pjcau/esp32-emu-turbo/docs/REPO_MAP.md

# Repo map — scripts

<!-- GENERATED by scripts/generate_repo_map.py — do not edit. -->
<!-- Regenerate: make repo-map    Verify: make repo-map-check -->

210 scripts, ~867,666 tokens of source. This index exists so that
finding the right one costs a single read instead of a repo-wide grep.

**gate** = exits non-zero on failure, so it can block a pipeline.
**~tok** = cost of opening the file, in tokens.

## `scripts/`

| script | gate | make | ~tok | purpose |
|---|:--:|---|--:|---|
| `analyze_pad_distances.py` | ✅ |  | 5,229 | Analytical pad distance checker for KiCad PCB files |
| `analyze_pin1_marker.py` |  | `analyze-pin1` | 3,075 | Locate the PHYSICAL pin-1 / polarity marker of an LCSC part, analytically |
| `arcade_art.py` | ✅ |  | 1,116 | arcade_art.py: launcher covers for the Neo Geo and CPS1 games, and the list of CPS1 sets |
| `audio_compare.py` | ✅ |  | 2,374 | audio_compare.py: can a listener tell two renderings of the same sound apart? |
| `board_cam.py` |  |  | 372 | Grab one frame from the webcam pointed at the board's screen |
| `board_ctl.py` |  |  | 4,471 | Drive the ESP32 Emu Turbo board over its USB console (bench remote control) |
| `console_art.py` | ✅ |  | 2,322 | console_art.py: launcher covers for the console games (the arcade ones: arcade_art.py) |
| `context_budget.py` |  | `context-budget` | 2,218 | Measure what this repo costs an AI agent's context window |
| `cps1_modern_sets.py` |  |  | 2,029 | Generate MAME 0.37b5 definitions for modern CPS1 ROM sets |
| `drc_check.py` | ✅ |  | 8,442 | DRC (Design Rule Check) for JLCPCB 4-layer PCB |
| `drc_native.py` | ✅ |  | 5,131 | Smart KiCad DRC analysis with JLCPCB rules and fix suggestions |
| `emu_check.py` |  |  | 1,176 | Quick 60 fps check across the non-SNES emulators on the card |
| `enclosure_placement.py` | ✅ |  | 1,624 | Place the PRINT files in the assembly — the viewer shows what you print |
| `erc_check.py` | ✅ |  | 3,867 | ERC (Electrical Rules Check) automation for KiCad schematics |
| `generate-schematic.py` |  |  | 96 | Thin wrapper: generate multi-sheet KiCad schematics for ESP32 Emu Turbo |
| `generate_board_config.py` | ✅ |  | 1,096 | Generate board_config.h GPIO #defines from config.py GPIO_NETS |
| `generate_docs_bom.py` | ✅ | `docs-bom` | 1,663 | Generate the docs BOM table from release_jlcpcb/bom.csv — the shipped BOM |
| `generate_enclosure_pcb.py` | ✅ | `generate-pcb` | 1,426 | Emit hardware/enclosure/pcb_parts.scad — the PCB, to the millimetre, for |
| `generate_net_explorer.py` | ✅ | `generate-pcb` | 5,986 | Emit the data file behind website/static/net-explorer.html |
| `generate_repo_map.py` | ✅ | `repo-map` | 1,219 | Generate docs/REPO_MAP.md — one line per script, so nobody greps 447k tokens |
| `generate_splash_preview.py` | ✅ |  | 3,457 | Build the web preview of the launcher boot splash from the firmware source |
| `inject-3d-models.py` | ✅ |  | 2,398 | Inject KiCad standard 3D model references into PCB footprints |
| `issue_dispatch.py` |  | `dispatch` | 7,473 | Turn failing hardware gates into briefings addressed to a named agent |
| `jlcpcb_parts.py` | ✅ |  | 2,090 | JLCPCB BOM parser and parts checker |
| `kicad_fill_zones.py` | ✅ |  | 1,582 | Fill all zones in a KiCad PCB file using the pcbnew Python API |
| `neogeo_frames.py` | ✅ |  | 2,808 | neogeo_frames.py: build and run the x86 harness (retro-go/mame-go/tools/neoframes.c) |
| `neogeo_modern_sets.py` |  |  | 2,583 | Generate MAME 0.37b5 ROM definitions for modern Neo Geo ROM sets |
| `neogeo_prepare.py` | ✅ |  | 1,203 | Prepare Neo Geo games for mame-go on the PC instead of on the board |
| `net_classifier.py` |  |  | 1,559 | Net Function Classifier — infers signal function from net names |
| `open_issues_report.py` | ✅ | `open-issues` | 1,832 | Report which hardware gates are currently failing, at session start |
| `order_manifest.py` | ✅ | `order-manifest` | 1,448 | Order manifest — SHA256 fingerprint of exactly what goes to JLCPCB |
| `pcb_cache.py` |  |  | 3,554 | PCB parse cache — parse .kicad_pcb once, cache as JSON for all consumers |
| `pcb_copper_graph.py` |  |  | 3,634 | Zone-aware copper graph — what the fabricated board is actually connected to |
| `pcb_optimize.py` |  |  | 5,102 | PCB Layout Optimization Analysis |
| `pcb_query.py` |  |  | 1,098 | Copper queries against the pcb_cache — answers in ~10 lines, not 265k tokens |
| `pcb_review.py` | ✅ |  | 11,434 | Comprehensive PCB Design Review |
| `render_3v3_rework_figures.py` |  |  | 4,058 | Render the +3V3 split-plane rework figures from the real PCB geometry |
| `saveload_check.py` |  |  | 2,810 | saveload_check.py: save / resume / in-session load of every game, on the board |
| `sd_update.py` |  |  | 878 | Firmware update through the SD card (roadmap Phase 6) |
| `short_circuit_analysis.py` | ✅ | `pcb-check` | 2,546 | Short circuit and zone fill analysis for JLCPCB 4-layer PCB |
| `simulate_circuit.py` | ✅ | `simulate` | 10,560 | Electrical verification and simulation for ESP32 Emu Turbo |
| `snes_bench.py` |  |  | 1,008 | SNES renderer benchmark on the first article: resume each saved scene, capture PROF |
| `spice_power_check.py` | ✅ |  | 1,917 | SPICE power supply simulation for ESP32 Emu Turbo |
| `test_claims_ledger.py` | ✅ |  | 912 | Mutation tests for verify_claims_ledger.py — the ledger gate must be |
| `test_collision_pad_nets.py` | ✅ |  | 2,208 | Mutation tests for the pad side of generate_pcb/collision.py |
| `test_collision_via_metric.py` | ✅ |  | 1,550 | Mutation tests for the via clearance checker in generate_pcb/collision.py |
| `test_cpl_rotation_law.py` | ✅ | `test-cpl-law` | 1,436 | Mutation tests for the CPL rotation law gate |
| `test_enclosure_requirements.py` | ✅ | `test-enclosure-requirements` | 1,770 | Mutation tests for verify_enclosure_requirements.py — every user |
| `test_enclosure_stl_solidity.py` | ✅ | `test-enclosure-stl-solidity` | 986 | Mutation tests for the S12 solidity check in verify_enclosure_stl.py |
| `test_enclosure_sync.py` | ✅ | `test-enclosure-sync` | 1,416 | Mutation tests for verify_enclosure_sync.py — the sync gate must fail |
| `test_erc_severity.py` | ✅ |  | 1,738 | Mutation tests for the ERC verdict in erc_check.py |
| `test_esd_protection.py` | ✅ |  | 898 | Mutation tests for verify_esd_protection.py — the promoted gate must fail |
| `test_gate_coverage.py` | ✅ |  | 1,449 | Mutation tests for verify_gate_coverage.py — the auditor must itself |
| `test_gerber_etest.py` | ✅ |  | 1,676 | Mutation tests for verify_gerber_etest.py — prove the gate can fail |
| `test_issue_dispatch.py` | ✅ |  | 1,958 | Mutation tests for the issue dispatcher's routing law |
| `test_order_manifest.py` | ✅ |  | 973 | Mutation tests for order_manifest.py — the freshness gate must be |
| `test_pcb_connectivity.py` | ✅ |  | 7,342 | Comprehensive PCB connectivity verification |
| `test_power_net_integrity.py` | ✅ | `test-power-nets` | 2,886 | Regression tests for the power-net integrity detector |
| `test_power_via_ampacity.py` | ✅ |  | 3,019 | Mutation tests for verify_power_via_ampacity.py — the gate must object |
| `test_strapping_en_rc.py` | ✅ |  | 2,222 | Mutation tests for the EN check in verify_strapping_pins.test_en_rc_delay |
| `test_test_points.py` | ✅ |  | 852 | Mutation tests for verify_test_points.py — the promoted gate must fail |
| `test_vbench.py` | ✅ | `bench-test` | 17,519 | Mutation tests for the Virtual Bench (Phase 0 foundation, Phase 1 physics, |
| `test_vbench_display.py` | ✅ | `bench-display-test` | 7,090 | Mutation tests for the Virtual Bench display half (T3.1) |
| `test_vbench_dynamics.py` | ✅ |  | 1,488 | Mutation-paired gate for vbench/dynamics.py — the dynamic scenarios |
| `test_vbench_sdcard.py` | ✅ | `bench-sdcard-test` | 5,988 | Mutation tests for the modelled microSD card (Virtual Bench T3.3) |
| `test_verify_memory.py` |  | `test-memory` | 3,325 | Mutation tests for verify_memory.py |
| `test_zone_fill_sanity.py` | ✅ | `test-zone-fill` | 4,118 | Regression tests for the zone-fill duplication bug and its detector |
| `update_component.py` | ✅ |  | 2,854 | Update a component across all BOM, CPL, and documentation files |
| `validate_jlcpcb.py` | ✅ | `validate-jlcpcb` | 7,487 | JLCPCB DFM Validation — comprehensive manufacturing rule checks |
| `validate_skills.py` | ✅ |  | 2,936 | Validator for Claude Code skills, slash commands, and plugin metadata |
| `verify_antenna_keepout.py` | ✅ |  | 3,178 | Antenna Keep-Out Zone verification for ESP32-S3-WROOM-1 (U1) |
| `verify_battery_protection.py` | ✅ |  | 1,517 | Battery Protection Verification — check reverse-polarity and over-voltage protection |
| `verify_bom_cpl_pcb.py` | ✅ |  | 3,391 | Cross-check BOM, CPL, and PCB for consistency |
| `verify_bom_values.py` | ✅ |  | 3,110 | BOM vs Schematic Value Cross-Check |
| `verify_bringup_fresh.py` | ✅ |  | 308 | Fail when the bring-up firmware is stale w.r.t. board_config.h |
| `verify_claims_ledger.py` | ✅ | `verify-claims` | 1,300 | Gate the load-bearing claims ledger — hardware/CLAIMS.md |
| `verify_component_bodies.py` | ✅ |  | 3,614 | Component BODY collision + board-edge gate (JLC SMT DFM classes) |
| `verify_component_connectivity.py` | ✅ |  | 2,224 | Component connectivity verification — catches phantom components |
| `verify_context_budget.py` |  |  | 722 | Gate on the context budget: fail when the repo's per-session cost regresses |
| `verify_copper_balance.py` | ✅ |  | 4,029 | Copper Balance Between Layers — verify copper distribution across all 4 layers |
| `verify_copper_clearance.py` | ✅ | `verify-copper-clearance` | 3,961 | Copper-to-copper clearance gate — catches what DRC misses at ≥ 0.09mm |
| `verify_cpl_rotation_law.py` | ✅ | `verify-cpl-law` | 4,314 | Assert that every CPL rotation obeys ONE global law, instead of a table |
| `verify_crosstalk.py` | ✅ |  | 7,582 | Fail on tightly coupled parallel runs between signals that cannot tolerate them |
| `verify_dangling_copper.py` | ✅ | `verify-dangling` | 865 | Fail on copper that stops in the air — track ends reaching nothing |
| `verify_datasheet.py` | ✅ |  | 6,541 | Datasheet vs PCB physical characteristics cross-verification |
| `verify_datasheet_nets.py` | ✅ | `verify-datasheet` | 2,546 | Verify PCB pad-to-net assignments against datasheet specifications |
| `verify_decoupling_adequacy.py` | ✅ |  | 3,179 | Decoupling Capacitor Adequacy Check |
| `verify_decoupling_paths.py` | ✅ |  | 2,432 | Decoupling Cap Path Length — verify caps have short routing paths to ICs |
| `verify_design_intent.py` | ✅ | `verify-intent` | 13,576 | Design Intent Adversary — cross-checks PCB against ALL design sources |
| `verify_dfa.py` | ✅ | `verify-dfa` | 5,600 | Design for Assembly (DFA) verification — Tier 1 + Tier 2 SMT DFM checks |
| `verify_dfm_v2.py` | ✅ | `verify-fast` | 39,241 | Verify DFM v2 fixes: CPL alignment, silkscreen, spacing, gerbers |
| `verify_drill_standards.py` | ✅ |  | 2,669 | Standard Drill Size Audit |
| `verify_easyeda_footprint.py` | ✅ | `verify-easyeda` | 13,008 | Proactive EasyEDA reference-footprint verification |
| `verify_enclosure_collision.py` | ✅ | `verify-enclosure-collision` | 1,269 | Enclosure interference gate — the shells must not share volume with |
| `verify_enclosure_requirements.py` | ✅ | `verify-enclosure-requirements` | 8,721 | Enclosure REQUIREMENTS gate — the user's constraints, one check each |
| `verify_enclosure_stl.py` | ✅ | `verify-enclosure-stl` | 9,121 | The OTHER road: measure the exported STLs, not the scad |
| `verify_enclosure_sync.py` | ✅ | `verify-enclosure-sync` | 9,434 | Enclosure <-> PCB mechanical sync gate — the shell must fit the board |
| `verify_erc.py` | ✅ | `verify-erc` | 1,080 | Gate: KiCad ERC on the generated schematic — zero findings, ANY severity |
| `verify_esd_protection.py` | ✅ |  | 5,039 | ESD Protection Verification — net-verified evidence for external interfaces |
| `verify_firmware_retrogo_sync.py` | ✅ |  | 3,248 | Retro-go target ↔ board GPIO sync gate |
| `verify_gate_coverage.py` | ✅ | `verify-gate-coverage` | 4,893 | Gate-coverage audit — inject known faults, demand the gate NETWORK object |
| `verify_gerber_etest.py` | ✅ | `verify-gerber-etest` | 5,818 | Gerber-level electrical test — opens and shorts from the SHIPPED artifacts |
| `verify_gerber_integrity.py` | ✅ |  | 1,950 | Gerber Integrity Verification — verify gerber files match the PCB layout |
| `verify_ground_loops.py` | ✅ |  | 1,503 | Test 11: Ground Loop Analysis |
| `verify_isolation.py` | ✅ | `verify-isolation` | 1,564 | Every conductor is connected where intended and isolated everywhere else |
| `verify_jlcpcb_capabilities.py` | ✅ |  | 4,956 | JLCPCB Official Capabilities Cross-Check |
| `verify_jlcpcb_via_rules.py` | ✅ | `verify-jlcpcb-vias` | 1,878 | Via and hole rules straight from JLCPCB's own design guide |
| `verify_length_match.py` | ✅ |  | 5,282 | Trace-length matching on the buses whose members must switch together |
| `verify_memory.py` | ✅ | `verify-memory` | 4,386 | Memory / context-preamble integrity verification |
| `verify_net_class_widths.py` | ✅ |  | 4,128 | Net Class Width Enforcement verification |
| `verify_net_connectivity.py` | ✅ | `verify-net-connectivity` | 6,863 | Net connectivity verification — walks the per-net copper graph and |
| `verify_net_explorer_fresh.py` |  |  | 226 | Fail when the Net Explorer data is stale vs the .kicad_pcb |
| `verify_netlist_diff.py` | ✅ |  | 6,645 | Netlist Diff — exports KiCad schematic netlist and cross-checks it against PCB cache |
| `verify_netlist_vs_kicad.py` | ✅ | `verify-netlist-kicad` | 1,242 | Cross-check our parsed netlist against KiCad's own IPC-D-356 export |
| `verify_order_manifest.py` |  | `verify-order-manifest` | 189 | Fail when release_jlcpcb/order-manifest.json is stale vs the order files |
| `verify_pad_land.py` | ✅ |  | 1,592 | Pad-vs-reference-land coverage gate (JLC SMT DFM pin/lead classes) |
| `verify_polarity.py` |  |  | 10,998 | Polarity and pin-to-net verification for ALL components on the PCB |
| `verify_power_net_integrity.py` | ✅ | `verify-power-nets` | 2,109 | Power-net integrity gate — every power net must be ONE piece of copper |
| `verify_power_paths.py` | ✅ |  | 3,296 | Power Delivery Path Tracing |
| `verify_power_resonance.py` | ✅ |  | 1,715 | Power Plane Resonance Check — estimate LC resonance of +3V3 plane |
| `verify_power_sequence.py` | ✅ |  | 4,008 | Power Sequencing Verification |
| `verify_power_trace_ampacity.py` | ✅ |  | 4,980 | Power-TRACE ampacity — can the copper itself carry the declared rail? |
| `verify_power_via_ampacity.py` | ✅ |  | 8,236 | Power-via ampacity gate — the layer transitions must carry the rail |
| `verify_reference_plane.py` | ✅ |  | 6,247 | Fail on signals whose reference plane changes underneath them mid-run |
| `verify_rpp_polarity.py` | ✅ |  | 1,068 | Q1 reverse-polarity-protection orientation, proven from the ORDER artifacts |
| `verify_schematic_crossings.py` | ✅ | `verify-sch-crossings` | 1,362 | Fail when two schematic wires cross without being connected |
| `verify_schematic_label_attach.py` | ✅ | `verify-sch-labels` | 1,292 | Fail when a schematic label does not lie on the wire it is meant to name |
| `verify_schematic_overlaps.py` | ✅ | `verify-sch-overlaps` | 3,276 | Schematic legibility gate — nothing printable may overlap anything else |
| `verify_schematic_pcb.py` |  | `firmware-sync-check` | 1,708 | Verify consistency between schematic sheets, main schematic, PCB, and JLCPCB exports |
| `verify_schematic_pcb_sync.py` | ✅ |  | 5,826 | Verify that the Python-generated schematic and the Python-generated PCB agree |
| `verify_schematic_pin_connectivity.py` | ✅ | `verify-sch-pins` | 2,110 | Fail when a placed schematic symbol has a pin that nothing lands on |
| `verify_schematic_render_overlaps.py` | ✅ | `verify-sch-render-overlaps` | 1,869 | Schematic legibility gate #2 — no two RENDERED text runs may overlap |
| `verify_sd_interface.py` | ✅ |  | 1,742 | SD Card Interface Verification — check SPI signal routing and support circuitry |
| `verify_signal_chain_complete.py` | ✅ |  | 3,504 | Signal chain completeness verification — catches broken copper paths |
| `verify_silk_holes.py` | ✅ |  | 2,287 | Silkscreen legibility gate — silk vs drill holes and mask openings |
| `verify_stackup.py` | ✅ |  | 1,794 | Stackup Layer-Net Verification for 4-layer PCB |
| `verify_stencil_aperture.py` | ✅ |  | 2,446 | IPC-7525 Stencil Aperture Analysis |
| `verify_strapping_pins.py` | ✅ |  | 4,172 | ESP32-S3 Strapping Pin Verification — check boot configuration |
| `verify_test_points.py` | ✅ |  | 2,379 | Test 12: Test Point Accessibility — blocking gate |
| `verify_thermal_budget.py` | ✅ |  | 2,839 | Thermal Budget Verification — junction temperature for power ICs |
| `verify_thermal_relief.py` | ✅ |  | 1,414 | Test 10: Thermal Relief Verification |
| `verify_trace_crossings.py` | ✅ | `verify-trace-crossings` | 1,884 | Trace-crossings check — detect pairs of copper segments on the same |
| `verify_trace_through_pad.py` | ✅ | `verify-trace-through-pad` | 2,196 | Trace-through-pad overlap check — detect copper traces physically |
| `verify_usb_impedance.py` | ✅ |  | 6,014 | USB D+/D- signal-integrity check, calibrated to the link's actual bit rate |
| `verify_usb_impedance_stackup.py` | ✅ |  | 2,699 | USB D+/D- Impedance Verification from JLCPCB 4-layer stackup parameters |
| `verify_usb_return_path.py` | ✅ |  | 1,283 | USB GND Return Path Density — verify GND via stitching near USB D+/D- traces |
| `verify_via_discontinuity.py` | ✅ |  | 4,221 | Via count and pair symmetry on the nets where layer changes matter |
| `verify_via_in_pad.py` | ✅ |  | 1,745 | Via-in-Pad Comprehensive Check — via holes must clear SMD pad edges |
| `verify_zone_connectivity.py` | ✅ |  | 2,616 | Zone Connectivity Verification — verify vias/pads on zone nets are covered by fill |
| `verify_zone_fill_sanity.py` | ✅ | `verify-zone-fill` | 2,376 | Zone-fill sanity gate — catches duplicated / impossible poured copper |
| `violation_matrix.py` |  |  | 3,340 | Violation matrix: parse .kicad_pcb and find ALL pad/via spacing violations |
| `zone_fill_inject.py` |  |  | 818 | Pure-text injection of zone fill data into a .kicad_pcb |

## `scripts/generate_pcb/`

| script | gate | make | ~tok | purpose |
|---|:--:|---|--:|---|
| `__main__.py` | ✅ |  | 56 | CLI entry point: python -m scripts.generate_pcb <output_dir> |
| `board.py` |  |  | 8,866 | Generate the complete KiCad PCB board |
| `collision.py` |  |  | 8,752 | Spatial collision detection for PCB trace routing |
| `footprints.py` |  |  | 12,472 | KiCad PCB footprint definitions with real pad geometries |
| `jlcpcb_export.py` |  |  | 8,483 | Generate JLCPCB CPL (Component Placement List) from board data |
| `pad_positions.py` |  |  | 1,550 | Compute absolute PCB-level pad positions for all components |
| `primitives.py` |  |  | 4,092 | KiCad PCB S-expression primitives |

## `scripts/generate_pcb/routing/`

| script | gate | make | ~tok | purpose |
|---|:--:|---|--:|---|
| `_assemble.py` |  |  | 2,268 | Split from routing.py 2026-07-26 — mechanical, AST-driven, proven by a |
| `_shared.py` |  |  | 17,758 | Complete PCB trace routing with Manhattan (orthogonal) paths |
| `audio.py` |  | `bench-audio` | 9,068 | Split from routing.py 2026-07-26 — mechanical, AST-driven, proven by a |
| `buttons.py` |  | `bench-buttons` | 29,484 | Split from routing.py 2026-07-26 — mechanical, AST-driven, proven by a |
| `display.py` |  | `bench-display` | 10,887 | Split from routing.py 2026-07-26 — mechanical, AST-driven, proven by a |
| `passives.py` |  |  | 8,336 | Split from routing.py 2026-07-26 — mechanical, AST-driven, proven by a |
| `power.py` |  |  | 29,065 | Split from routing.py 2026-07-26 — mechanical, AST-driven, proven by a |
| `sd.py` |  |  | 3,604 | Split from routing.py 2026-07-26 — mechanical, AST-driven, proven by a |
| `usb.py` |  |  | 8,917 | Split from routing.py 2026-07-26 — mechanical, AST-driven, proven by a |

## `scripts/generate_schematics/`

| script | gate | make | ~tok | purpose |
|---|:--:|---|--:|---|
| `__main__.py` |  |  | 187 | CLI entry point: python -m generate_schematics /output/dir |
| `config.py` |  |  | 984 | Shared configuration: GPIO mapping, ESP32 pin definitions, layout constants |
| `kicad_primitives.py` |  |  | 3,591 | KiCad S-expression primitives for schematic generation |
| `lib_symbols.py` |  |  | 11,708 | KiCad library symbol definitions for all components |
| `root_schematic.py` |  |  | 757 | Generate a hierarchical root schematic referencing all sub-sheets |
| `sheet_base.py` |  |  | 1,721 | Base class for KiCad schematic sheet generation |

## `scripts/generate_schematics/sheets/`

| script | gate | make | ~tok | purpose |
|---|:--:|---|--:|---|
| `audio.py` |  | `bench-audio` | 3,541 | Sheet 4: Audio - I2S DAC -> PAM8403 -> Speaker |
| `controls.py` |  |  | 2,296 | Sheet 6: Controls - 12 buttons with pull-ups and debounce capacitors |
| `display.py` |  | `bench-display` | 2,912 | Sheet 3: Display — ILI9488 3.95" 320×480 8-bit 8080 parallel interface |
| `mcu.py` |  |  | 4,677 | Sheet 2: MCU - ESP32-S3-WROOM-1 N16R8 with decoupling and GPIO labels |
| `power_supply.py` |  |  | 14,594 | Sheet 1: Power Supply - USB-C -> IP5306 bare IC -> SY8089 buck -> 3.3V |
| `sd_card.py` |  |  | 910 | Sheet 5: SD Card - SPI interface for ROM storage |

## `scripts/mamebench/`

| script | gate | make | ~tok | purpose |
|---|:--:|---|--:|---|
| `mbsum.py` |  |  | 597 | mbsum.py <log>: MAMEBENCH hashes, the average NEOPROF ms (68000, video, total core 0) |
| `wait_launcher.py` |  |  | 120 | wait_launcher.py: wait (60 s max) until the board answers ping from the launcher |

## `scripts/vbench/`

| script | gate | make | ~tok | purpose |
|---|:--:|---|--:|---|
| `audio.py` | ✅ | `bench-audio` | 3,017 | Virtual Bench T3.2 — the audio chain, and the current it pulls off the rail |
| `buttons.py` | ✅ | `bench-buttons` | 3,760 | Virtual Bench T2.2 + T2.3 — the buttons' debounce RC, and the power switch |
| `conflicts.py` | ✅ | `bench-conflicts` | 2,316 | Virtual Bench T1.3 — electrical conflicts: two things fighting over one net |
| `corpus.py` | ✅ | `bench-retro` | 3,420 | Virtual Bench T0.3 — the retro corpus, and the proof it is not fiction |
| `detectors.py` |  |  | 3,016 | Virtual Bench T5.1 — does the bench actually rediscover the known bugs? |
| `display.py` | ✅ | `bench-display` | 5,696 | Virtual Bench T3.1 — the display: the panel's wiring, and the controller |
| `dynamics.py` | ✅ | `bench-dynamics` | 4,387 | Virtual Bench T1.4b — dynamic corner scenarios (containment layer 3) |
| `export_header.py` | ✅ | `bench-header` | 2,935 | Virtual Bench T4.1 — export the derived board facts as a C header |
| `ili9488_ctrl.py` | ✅ | `bench-display-frame` | 7,983 | Virtual Bench T3.1 — the ILI9488 controller, as a state machine |
| `mutate.py` |  |  | 1,861 | Break the board on purpose, in memory, so the bench can be measured |
| `netlist.py` | ✅ | `bench-netlist` | 7,575 | Virtual Bench T0.1 — the netlist the bench stands on, and its disputes |
| `pins.py` | ✅ | `bench-pins` | 2,442 | Virtual Bench T2.1 + T2.4 — the pin fabric, and what this board boots into |
| `rails.py` | ✅ | `bench-rails` | 5,336 | Virtual Bench T1.1 — the DC operating point: what voltage sits on every net |
| `scenario.py` | ✅ | `bench-ci` | 2,501 | Virtual Bench T4.3 — scenarios with assertions, headless, for CI |
| `sdcard.py` | ✅ | `bench-sd` | 2,424 | Virtual Bench T3.3 — the SD card's bus, and the pads it shares with signals |
| `sdcard_protocol.py` | ✅ | `bench-sdcard` | 9,830 | Virtual Bench T3.3 — a microSD card that answers, and a host that asks |
| `sources.py` |  |  | 988 | Virtual PSU and virtual LiPo — what the bench connects the board to |
| `thermal.py` | ✅ | `bench-thermal` | 3,214 | Virtual Bench T1.5 — junction temperatures, and which ones are guesses |
| `transients.py` | ✅ | `bench-transients` | 5,190 | Virtual Bench T1.4 — transients: cold start, inrush, load steps, brownout |

## `scripts/vbench/models/`

| script | gate | make | ~tok | purpose |
|---|:--:|---|--:|---|
| `_schema.py` |  |  | 3,691 | Virtual Bench T0.2 — what a component model must prove before it counts |
| `bt1_lp105080.py` |  |  | 907 | BT1 — the 105080 LiPo cell, modelled from a FAMILY datasheet |
| `card_microsd.py` |  |  | 5,058 | CARD — the microSD card itself, in SPI mode. The part the socket holds |
| `ds1_ili9488.py` |  |  | 6,333 | DS1 — the ILI9488 CONTROLLER, from the ILITEK specification itself |
| `q1_ao3401a.py` |  |  | 2,129 | Q1/Q2 — AO3401A P-channel MOSFET: battery RPP gate and +5V load switch |
| `u1_esp32s3.py` |  |  | 1,748 | U1 — ESP32-S3-WROOM-1-N16R8: the strapping pins and what they decide |
| `u2_ip5306.py` |  |  | 1,969 | U2 — IP5306, the charger + 5 V boost that feeds everything else |
| `u3_sy8089.py` |  |  | 1,890 | U3 — SY8089AAAC synchronous step-down regulator, the +3V3 source |
| `u5_pam8403.py` |  |  | 1,934 | U5 — PAM8403 filterless class-D amplifier, the speaker driver |
