pjcau/esp32-emu-turbo/docs/first-boot-session-2026-08-29.md

# First-boot session log — 2026-08-29 — article 0003 (v4.9.0, W2026081721393881)

Live session log for the staged sequence in
`website/docs/manufacturing/first-boot.md`. Resume point for any machine.

| Stage | Exit criterion | Result | Evidence |
|---|---|---|---|
| 0 pre-flight | board matches renders, both sides | ✅ PASS | `docs/first-article-phaseB-2026-08-29.md` (continuity check skipped — no multimeter, per "as far as your tools allow") |
| 1 USB only | VBUS LED on | ✅ PASS | `hardware/first-article/v4.9.0-W2026081721393881/IMG_5905.jpeg` — VBUS lit with SW16 OFF (rails correctly dark: Q2 gating works) |
| 2 rails | 5V/3V3 LEDs | ✅ PASS | `IMG_5906.jpeg` — SW16 ON: VBUS+5V+3V3 lit, HB dark (chip blank — expected). **Resolves the doc's open question: IP5306 DOES supply 5V batteryless.** CHG+FULL both lit with no cell (undefined-but-harmless, re-check at Stage 4) |
| 3 boot | HB LED 1 Hz + BRINGUP verdict | ✅ PASS | `hardware/first-article/v4.9.0-W2026081721393881/bringup-stage3-serial-2026-08-29.log` — **GREEN, 47 PASS / 0 FAIL / 11 expected SKIP**, reproduced on two consecutive warm resets; HB at 1 Hz confirmed by eye (operator, 2026-08-29). Two latent bring-up firmware bugs found and fixed on the way (see below) |
| 4 battery | boots from cell alone | ✅ PASS (2026-09-11) | 105080 cell on J3 via a soldered JST-PH pigtail: boots from the cell alone, charge-and-play (CHG with USB while running), OFF kills 5V/3V3/HB on battery and stays off, charge-only with USB in OFF (VBUS only), **wake test PASS — C33 4.7 µF closes its BENCH-VALIDATE**. Cell cool under load. See "Stage 4" below |
| 5 subsystems | blink codes clear one by one | ✅ PASS (SD, LCD, audio) | **SD: PASS** — `bringup-stage5-sd-serial-2026-08-29.log`, GREEN 52/0/6 with a 16GB card: full chain incl. FAT mount at 20 MHz. (A no-name 128GB card was rejected at CMD59/CRC_ON_OFF by the IDF driver on every try incl. freshly powered — card-side fault, do not use it.) **LCD: PASS (2026-09-11)** — `bringup-stage5-lcd-serial-2026-09-11.log`, GREEN 53/0/6 with the panel on the R37 workaround (40P extension board + type-B FFC): `lcd.data.risetime` 1000–1200 ns on all of D0–D7 (was ~200 ns unloaded), 8 colour bars confirmed by eye in the documented order, then the black/white load-test fills; no 3V3 event. R37-HIGH-1 stays open only as the v2 top-contact J4 item. **Audio: PASS (operator-confirmed)** — speaker soldered, 3×1 kHz beep pattern clearly recognizable over the R38 carrier hiss (test tone reworked for it; channel now silenced after the check). Clean audio deferred to the R38 v2 fix. Nothing remaining at stage 5 |

## R37-HIGH-1 — J4 contact face is inverted for the purchased panel (found at first article, 2026-08-29)

The purchased panel (marked **LHC400IT005-9488**, ILI9488, 40P 0.5 mm,
separate 4-wire resistive-touch tail left unconnected) carries its tail
contacts on the **opposite face** from what J4 expects. J4 (FPC-05F-NPH20,
C2856812) is a flip-lock **bottom-contact** ("翻盖下接") connector, and its
mouth faces the FPC slot, so the ribbon's entry direction is fixed —
which locks contact-face and pin-order parity together: **no fold or
twist can give "contacts toward PCB + pin 40 on pad 1" at the same
time.** Confirmed on the bench both ways: contacts-up = correct 41−N
order but zero contact (rise-time probe flat at ~200 ns, backlight dark);
flipped = contact but mirrored order → **+3V3 rail collapse** (panel GND
onto 3V3 — operator cut power immediately, board unharmed, next runs
GREEN).

- **First-article workaround**: 40P 0.5 mm FPC extension adapter board +
  **type-B ("opposite side") FFC cable**, as short as possible (3-5 cm —
  the 8080 bus runs at 20 MHz). Type A does not invert; do not use it.
- **v2 fix**: change J4 to the **top-contact** variant of the same
  connector family ("翻盖上接", same footprint) — inverts the face,
  keeps the routed 41−N order, no adapter needed.
- New bring-up check `lcd.data.risetime` (added this session) is the
  no-multimeter contact probe: ~200 ns = panel not loading the data
  lines; a seated panel must slow every line.

## R38-MED-1 — no PDM reconstruction filter in the audio path (found at first article, 2026-08-29)

Speaker soldered (SPK+/SPK− pads, BTL) and the 440 Hz bring-up tone IS
audible — the chain GPIO17 → C22 → PAM8403 → speaker is electrically
alive — but it sounds like a loud fan-like hiss with a faint tone under
it, and cutting the tone amplitude −12 dB did not reduce the hiss:
**the PDM carrier dominates**. Root cause: the board has NO low-pass
between the PDM pin and the amplifier input — C22 is a series DC-block
(a high-pass), and the `audio.c` comment claiming the "existing RC
network acts as a low-pass filter" was wrong (there is no shunt element).
The full-swing MHz PDM stream drives the PAM8403 input directly.

- **v2 fix**: series R (~1k) + shunt C (~10 nF) between C22 and
  PAM_IN_AC — or moot entirely under the planned v2 audio coprocessor
  with a true I2S DAC.
- **First-article rework (optional, fiddly)**: requires inserting a
  series element — deferred unless audio testing needs it.
- Firmware mitigation this session: the bring-up suite now calls
  `audio_stop()` after the audio checks — an enabled-but-idle PDM
  channel emits its 50%-density carrier continuously, which was a
  constant hiss for as long as the board stayed on.
- `audio.audible` verdict: chain alive = the check's purpose met;
  fidelity is R38's problem, not the board assembly's.

## Session close (2026-08-29 evening)

Final board state: **BRINGUP GREEN 53/0/6, HB steady at 1 Hz,
operator-verified.** LED legend learned on the bench: 10-blinks/s
flutter + 1 s pause = "failure with no code", in practice almost always
`bringup.previous_run` after a capture-harness reset killed a run
mid-flight — one clean run (or SW16 power-cycle) clears it; a flutter
that survives a power-cycle would be a real failure.

Resume points, in arrival order:
1. ~~**~2026-09-12** — type-B FFC adapter arrives → LCD retry~~ **DONE
   2026-09-11, PASS** — see "LCD retry" below.
2. Battery cell → stage 4 (LIVE operation, C33 wake test).
3. v2 backlog from today: R37 (top-contact J4), R38 (PDM RC filter),
   plus a +/− silkscreen for the SPK pads.

## LCD retry (2026-09-11) — R37-HIGH-1 workaround validated, stage 5 complete

Parts arrived: 40P 0.5 mm FPC extension board + type-B ("opposite side")
FFC, operator-verified as type B (contacts on opposite faces at the two
ends) and kept short. Chain: panel tail → extension board → type-B FFC →
J4, pin 40 toward the "LCD" silk. Powered from USB, 3V3 LED steady.

Operator observation at power-up: panel white (backlight on, panel not
yet initialised — normal), then **8 vertical colour bars** in the
documented order, then the slow black and white full-screen wipes of
`power.load` (each `display_fill` takes ~1.5 s while both cores are
saturated by the load tasks — 2 fills in 3 s — so the wipes read as a
"curtain"; not a panel symptom), ending on white. HB 1 Hz throughout.

Serial: `bringup-stage5-lcd-serial-2026-09-11.log`, **GREEN 53/0/6**,
`bringup.previous_run` clean (reset=11). The contact probe that was
flat at ~200 ns in August now reads **D0–D3 = 1000 ns, D4–D7 = 1200 ns**
— every data line is loaded by the panel, which with the bars by eye
closes the only LCD check the firmware cannot make itself
(`lcd.panel.readback` is SKIP by design, LCD_RD tied HIGH).

Capture recipe used (same as August, now as a one-shot script): open the
port with DTR=RTS=1 (no reset on open), drain 12 s, one esptool-style
reset (DTR low → RTS high 0.2 s → RTS low), read until a line starting
with `BRINGUP-END`.

Stage 5 is therefore complete on article 0003: SD, LCD and audio all
PASS. Still open on the board: stage 4 (battery — no cell yet). The v2
backlog is unchanged: R37 top-contact J4 (the adapter is a first-article
workaround, not a fix), R38 PDM RC filter, SPK +/− silkscreen.

All seven LED polarities are now physically confirmed (HB beating at 1 Hz
at Stage 3 closed the last one) — the LED `_PENDING_VALIDATION` is fully
closed.

## Stage 3 — how to flash (machine-specific)

Binaries are reproducible from the repo: `make bringup-build` (Docker;
`bringup-check` must stay green). Flash offsets (from
`software/bringup_test/build/flasher_args.json`): `0x0` bootloader,
`0x8000` partition-table, `0x20000` app; DIO, 80 MHz, 16 MB.

- **Linux**: `make bringup-flash` works natively (Docker maps the port).
  The blank S3's USB-Serial-JTAG enumerates as **`/dev/ttyACM0`**, not
  ttyUSB0 — run `ESP_PORT=/dev/ttyACM0 make bringup-flash`.
- **macOS**: Docker cannot pass USB through — flash with local esptool
  (`pip3 install --user esptool`), port `/dev/cu.usbmodem*`:
  `python3 -m esptool --chip esp32s3 -p /dev/cu.usbmodem* -b 460800 \
   write_flash --flash_mode dio --flash_freq 80m --flash_size 16MB \
   0x0 build/bootloader/bootloader.bin 0x8000 build/partition_table/partition-table.bin \
   0x20000 build/esp32-emu-turbo-bringup.bin` (from `software/bringup_test/`).

Board prerequisites for flashing: **USB-C to the computer, SW16 ON** (with
the switch OFF there is no +3V3 and the chip never enumerates). Flash is
factory-blank so the ROM enters download mode by itself; after the first
flash, reset (replug) and expect HB at 1 Hz + the 58-check serial report at
115200 baud (`BRINGUP-SUMMARY` / `BRINGUP-LED` lines are the verdict).

## Stage 3 findings (2026-08-29) — two firmware bugs, zero board defects

Both bugs lived in the bring-up firmware itself and produced false RED
verdicts on a healthy board; both fixed in `generate.py` and re-verified:

1. **`bringup.previous_run` self-poisoning** — `run_check()` stamps the
   crash-forensics marker with the check's own id *before* running it, so
   check 01 read its own freshly-written marker instead of the previous
   run's, and failed on every warm (USB) reset by construction. It only
   ever passed on a true power-on, which is why the doc's "replug" flow
   never showed it. Fix: snapshot the marker in `app_main()` before the
   first `run_check()`.
2. **`usb.serial_jtag` FIFO race** — the check sampled
   `usb_serial_jtag_ll_txfifo_writable()` once, while the report itself
   was filling that FIFO; whenever the host's read cadence left the FIFO
   momentarily full, a live link was reported dead. Fix: poll up to 50 ms
   (an attached host drains it in microseconds).

Capture-harness gotchas for any future machine (all reproduced here):
- **Any DTR/RTS edge on the port resets the chip** (USB-Serial-JTAG reset
  logic; `rst:0x15 USB_UART_CHIP_RESET`): Linux cdc-acm raises DTR on
  open, drops it on close — so `stty`+`cat`, idf_monitor attach, or a
  pyserial open/close each reboot the board mid-run.
- To capture a clean full run: open the port plainly (lines settle at
  DTR=RTS=1, no reset), wait ~12 s for any in-flight run to finish, then
  do one esptool-style reset (DTR low → RTS high 0.2 s → RTS low) and
  read to `BRINGUP-END` while draining continuously.
- Grep for `BRINGUP-END` at start-of-line only: check 01's PASS detail
  contains the literal string "reached BRINGUP-END".

## Retro-Go first boot (2026-09-11) — Phase 2.8 reached, R39-HIGH-1 found

Retro-Go (fork, target `esp32-emu-turbo`) built from the submodule and
flashed as a full image (`rg_tool.py install` at 0x0 — `make
retro-go-flash` cannot be the first flash: it writes per-partition and
the board still carried the bring-up partition table). Card: the 16 GB
SD, FAT32, `roms/<system>/` with the free test ROMs from `test-roms/`.
Four firmware findings, all fixed in the fork (commit 0e533078 +
follow-ups) — none is a board defect:

1. **Half-drawn windows.** `rg_display` streams a window as 4-line DMA
   chunks and the IDF i80 IO sends a command with every chunk; the driver
   sent 0x2C each time, which resets the write pointer to the window
   origin, so only the first 4 rows of every rectangle were written (half
   glyphs, stale rows from the previous image). Fix: 0x2C on the first
   chunk after `set_window`, 0x3C (Memory Write Continue) after. The
   bring-up never showed it because `esp_lcd` sends a whole bitmap in one
   0x2C.
2. **Portrait target on a landscape handheld.** The panel sits along the
   board's long axis (D-pad left, ABXY right); the target was 320x480
   portrait. Now 480x320, MADCTL 0x28 — operator-confirmed upright with
   the clusters on the correct sides. The docs' "2x vertical" scaling
   plan is void (see Phase 2 docs).
3. **PDM carrier hiss in the launcher.** With no reconstruction filter
   (R38) an enabled PDM channel is a loud hiss even on zero samples.
   `pdm.c` now keeps the channel disabled while muted or at volume 0
   (time-paced like the dummy driver) and this target starts at volume 0
   (`RG_AUDIO_DEFAULT_VOLUME`, generic default 50 unchanged).
4. **R39-HIGH-1 — module pins 38/39 swapped in every project table.**
   Symptom: D-pad RIGHT opened the game menu (the A action) and A did
   nothing. The WROOM-1 datasheet on disk (`hardware/datasheets/U1_…pdf`,
   "Pin Definitions") has **pin 38 = IO2, pin 39 = IO1**; `_PIN_TO_GPIO`,
   `datasheet_specs.py`, the schematic symbol/pin table, `board_config.h`
   and the Retro-Go target all had 38=GPIO1/39=GPIO2, and the gate
   `Pin 38 = GPIO1` asserted the wrong fact (a table copied into its own
   check). Pins 4-37 verified against the datasheet: only this pair.
   **The copper is right**: BTN_RIGHT lands on pad 38 = GPIO2, BTN_A on
   pad 39 = GPIO1 — so the fix is names only: `BTN_RIGHT=GPIO2`,
   `BTN_A=GPIO1` in board_config.h / config.py / Retro-Go target, tables
   and symbol corrected, gate now asserts 38=GPIO2 and 39=GPIO1. The
   regenerated PCB is byte-identical to the built board. Bring-up
   firmware regenerated (its 2026-09-11 log predates the rename: its
   `btn.RIGHT` lines really exercised GPIO1 = the A button, and vice
   versa — idle/pull checks only, verdict unaffected).

Result: launcher usable (L/R added as system prev/next), all 12 buttons
operator-verified in the launcher, **Owlia (NES) launched and played** —
Phase 2.8 done on free homebrew; Super Mario Bros is the user's own copy,
kept out of git (`.gitignore` now ignores every ROM under `test-roms/`
except the committed homebrew set).

## Stage 4 — battery (2026-09-11), PASS

Cell: the 105080 LiPo, wired to a JST-PH pigtail by solder joints (J3 has
no "+" silkscreen — only "BATT"; pad 1 = BAT_IN, pad 2 = GND; v2: add a
polarity mark). Polarity checked by continuity to the USB-C shell before
joining. Screen and SD fitted, bring-up firmware re-flashed for the HB
LED (GREEN 53/0/6 on USB first).

Sequence and results:
- **First cold start from a freshly connected cell**: SW16 ON gave only a
  faint 5V LED (the IP5306 load-detect pulses), nothing else. A USB
  "kick" (charger, 2 s) started the IP5306; from then on every test
  below passed, including the wake test. Reading: an IP5306 that has
  just been connected to a cell does not start from the KEY pulse
  alone; once it has seen VIN it wakes from KEY reliably. Once per cell
  insertion, not a defect — note it in the user docs.
- Boots from the cell alone, USB unplugged while running → keeps
  running: boost (U2, L1), Q1 and the BAT+ copper are good.
- Charge-and-play: CHG lights with USB while running. On battery,
  CHG+FULL both lit = the IP5306's discharge-mode level display, not a
  fault (closes the August "CHG+FULL with no cell" question).
- SW16 OFF on battery: 5V/3V3/HB/screen all off, still off after a
  minute (Q2 gates the loads on battery too).
- USB in with SW16 OFF: VBUS only — charge-only path works. CHG stayed
  dark with this (fresh, likely full) cell; re-check with a partly
  discharged cell that CHG lights in charge-only.
- **Wake test: USB out, OFF for a full minute (IP5306 32 s light-load
  shutdown has fired), ON → 5V → 3V3 → HB on its own.** C33 4.7 µF is
  validated; SW17 stays DNP.
- Cell cool throughout; no thermal observation on Q1/U2.
- **Bench rule, proven the hard way**: with the cell on J3 the board does
  NOT enumerate on the MacBook's USB port (`device not accepting
  address, error -71`, chip resetting in a loop) — the IP5306 starts
  charging as soon as it sees VBUS and the 500 mA port collapses. Unplug
  J3 for any flash/serial session from a laptop port (a wall charger or a
  powered hub is fine for charge-and-play). Matches the schematics.md
  note that "battery isolation for bench work is unplug J3".

First article status: **stages 0-5 all PASS.** Remaining bench items are
performance (SNES fps on the real board) and the v2 backlog (R37
top-contact J4, R38 PDM RC filter, SPK and J3 polarity silkscreen).

## SNES on the real board — first numbers (2026-09-11, late)

Read from the USB serial (`[debug] ... BUSY:x%, FPS:t (S:s R:r+p)` line,
printed once a second by `rg_system`; t = emulated frames/s, s = skipped,
r = rendered). Board on the Mac's USB, battery unplugged.

| ROM | Core state | Emulated fps | Drawn fps | BUSY |
|---|---|---|---|---|
| Super Boss Gaiden (homebrew) | reading later identified as the LAUNCHER idle loop (107 fps, 2% busy) — game not actually measured | — | — | — |
| Super Mario World (U) | runs, playable | **42 / 60 = 70%** | ~11 (frameskip 3 fixed in `main_snes.c`) | 68–75% |

Baseline for Phase 4 (30→60 fps) is therefore **70% speed, 11 drawn fps,
~28% of wall time NOT spent in the core** — worth checking whether the
audio pacing (`rg_audio_submit`, PDM channel off at volume 0 so paced by
sleep) or `rg_display_sync` is the idle 28% before touching the emulator.
Audio: crackles as expected (R38 + underruns at 70% speed). Free heap
under SNES: 167 KB internal, 566 KB PSRAM.

## SNES — where the time goes (2026-09-12, instrumented build)

After fixing the per-frame audio size (533 samples for NTSC, fork
8164755a) Super Mario World runs at 45-52 emulated fps. Instrumenting the
loop (`RG_ENABLE_PROFILING`, fork commit after 8164755a) and the audio
pacing sleep gave the breakdown per frame:

| Piece | Time | Note |
|---|---|---|
| `S9xMainLoop`, frame NOT rendered | ~8.5 ms | CPU + APU emulation alone would do 60 fps with margin |
| `S9xMainLoop`, frame rendered | ~40-50 ms | PPU tile renderer — the bottleneck |
| `rg_display_submit` | 5 µs | asynchronous, display path is not a factor |
| audio mix | 1.5 ms | |
| audio pacing sleep | exact (requested = actual) | Dummy and PDM identical; the ~3 ms/frame "idle" was the late arrival after rendered frames |

With `frameskip = 3` (fixed in `main_snes.c`) ~13 rendered frames/s eat
about half the machine time. Consequences: emulated speed 75-85%, ~10-13
visual fps. Phase 4's target is therefore the snes9x renderer (gfx/tile):
a ~5x speed-up on rendered frames is what 30 visual fps at real speed
needs. Super Boss Gaiden (homebrew) hangs snes9x and is not usable as a
benchmark; Super Mario Kart (Mode 7) behaves like Super Mario World.

## NES 60 fps + PDM DAC mode (2026-09-12)

- **Super Mario Bros (NES, nofrendo): 60 fps, BUSY 35%** — Phase 2.8's
  stated target met on the first article.
- Audio: the PDM driver now uses IDF's **DAC line mode** (fork, carrier
  128 x 48 kHz, tuned sigma-delta scaling) instead of codec line mode.
  Operator A/B: "much better, the music is distinct", a hiss remains —
  the expected R38 residual; the RC rework sheet (1 kΩ + 10 nF at C22) is
  the next step, software has no further lever on a full-swing carrier.
- The per-frame SNES audio size fix is confirmed by ear: pitch and tempo
  correct.

## Phase 4 step 4.0 — the renderer instrumented, two fixes, SMW at 60 fps (2026-09-13)

Bench: board on USB (`/dev/ttyACM0`), battery off J3, volume 0, Super Mario
World, the heavy scene (1 strip/frame, ~2950 tiles/frame, Mode 1). Fork
commit 3e444cd9 + the Transparency knob.

**Tooling correction.** Yesterday's 40–50 ms "rendered frame" came from
`rg_tool.py profile` = `RG_ENABLE_PROFILING`, which also passes
`-finstrument-functions` to every component (mutex + linear lookup on every
function entry/exit — the tile writers are called thousands of times a
frame). New switch `SNES_PROF=1` (env var, `retro-core/CMakeLists.txt`):
counters and timer reads only, `PROF` / `PROF/drawn-frame` lines once a
second, plus a 7-column HUD in the 57 px letterbox bar left of the viewport
(drawn from the loop only when the display is idle, outside the timed
sections). Build: docker `retro-go-flash` service with `-e SNES_PROF=1`,
`rg_tool.py build retro-core` then `flash retro-core`.

**Measured, production code (per drawn frame):**

| | before | blank-tile fix | + pacing credit | Transparency Off (not a fix) |
|---|---|---|---|---|
| emulated fps | 45–47 | 47–48 | **60** | 60 |
| drawn fps | 11–12 | 12 | 15 (auto-frameskip 3–5), 20–30 in light scenes | 30 |
| busy | 65–72% | 66–71% | 80–95% | 92–95% |
| `S9xMainLoop` drawn / skipped | 34.5 / 8–10.5 ms | 36 / 9 | 30 / 9 | 17.5 / 10 |
| **R** (renderer) | **24.0 ms** | 21.3 | 21.0 | 7.5 |
| `S9xUpdateScreen` = clear + sub + main + combine | 24.2 = 3.1 + 6.1 + 8.1 + 6.7 | 21.8 = 3.1 + 5.8 + 6.4 + 6.2 | same | 9.0 = 4.5 + 0 + 4.4 + 0 |
| BG0 / BG1 / BG2 / OBJ | 3.1 / 6.1 / 4.3 / 0.7 | 2.4 / 5.8 / 3.7 / 0.3 | same | 3.2 / **0** / 0.7 / 0.5 |
| tiles entered / blank / ConvertTile | 3050 / 1500 / **1520** | 2900 / 1480 / **25** | same | 2100 / 1570 / 30 |
| audio submit (skipped frames) | 3.5–5.5 ms | same | 0.1–2 | |

- **Blank tiles were never cached.** `ConvertTile()` returned a depth-less
  `BLANK_TILE` that could not satisfy the "cached at this depth"
  test, so every blank tile was re-converted every draw (VRAM read + 64 B
  cache write, both PSRAM). Now `0x20|depth` is a cached state. R −11%.
- **The audio pacing threw away the skipped frames' slack.** Muted PDM path
  slept "chunk duration from now" on each submit: the three 12 ms frames of
  a frameskip-3 group were stretched to 16.7 ms each while the 36 ms drawn
  frame's overrun was never recovered → 86 ms per 4 frames = 46 fps at
  65–72% busy. `busy_until` now models a queue allowed to run up to the DMA
  lead ahead, and DMA goes 4 → 8 × 256 frames (32 → 64 ms) so the unmuted
  path matches. **SMW at 60 fps, 100% speed**; audio ON re-measured:
  identical (58–62 fps, R 22, 20 drawn).
- `rg_system`'s auto-frameskip (1..5 on speed/busy) is live — the plan doc's
  "adaptive branch is dead code" was wrong; only the initial value is 3.
- **Colour math is on in every frame of this scene and BG1 lives on the
  sub-screen only** (`bg1=0` with transparency off): the new
  "Transparency Off" option drops that layer (operator-confirmed missing
  elements in several screens), so it stays a knob, not a fix. Its numbers
  give the ceiling: the colour-math path costs ~14 of the 21 ms.

**Next**: 4.1 cache config (I-cache 32 KB, D-cache 64 KB / 64 B — bootloader
applies it, full `install`), 4.2 z-buffers internal + `IRAM_ATTR` writers,
then the combine loop (6.5 ms = 113 ns/pixel in C) and the sub-screen pass.
Milestone A (60 emulated / 20 drawn on the heavy scene) needs R ≤ 14 ms.

### Same day, later — cache, z-buffer, Super Mario Kart (fork 48cedc75)

Second reference scene: **Super Mario Kart, race** (Mode 7 + DSP-1
coprocessor, 27 strips/frame from HDMA, OAM rewritten mid-frame). Before
any of this it ran at 38–40 fps: a **non-drawn frame costs 17.3 ms** there
(CPU + DSP-1 + APU alone exceed the 16.7 ms budget — the DSP-1 is emulated
in software, `dsp.c`), R 28 ms, `S9xSetupOBJ` 24×/frame = 6 ms, Mode 7 main
pass 20 ms.

| Mario Kart race | before | I-cache 32 KB + D-cache 64 KB/64 B | + main z-buffer internal |
|---|---|---|---|
| non-drawn frame | 17.3 ms | **11.7** | 10.7 |
| R | 28 | 24.5 | 22 |
| fps | 38–40 | 56–58 | **60** |
| busy | 96% | 98% | 96–97% |
| free internal heap | 164 KB | 117 | 80 (largest block 31 KB) |

- The cache change is the biggest single win so far and it helps the CPU
  side more than the renderer: everything the 65C816/DSP-1 touches (WRAM,
  ROM, SRAM) is in PSRAM. Gotcha: `rg_tool.py` passes the target sdkconfig
  as `SDKCONFIG_DEFAULTS`, which never rewrites an existing app sdkconfig —
  the first "install" changed nothing; `clean` + `install` did.
- The second z-buffer (61 KB) no longer fits internal (31 KB largest block).
- **Tried and reverted**: per-strip `S9xSetupOBJ` with per-line OAM
  generations. Calls rose 24 → 46–61/frame and the time did not move —
  137 µs per 8-line strip, not proportional to lines, i.e. the cost is
  fetching the function from flash on every strip, not the work. 60 → 53
  fps. The lever is `IRAM_ATTR` on the strip-path code, not fewer lines.
- Benchmark set agreed with the user (light → heavy, one save state each):
  Super Mario World, Zelda ALttP, Mega Man X, Super Metroid, Super Mario
  Kart. Super FX / SA-1 titles are out of scope.
- Open cosmetic: a light-blue rectangle refreshing every ~2 s on Mario
  Kart's selection screen (SNES_PROF builds only — most likely the HUD
  write colliding with a full-viewport update; not seen in-race).

State at close: fork 48cedc75, SMW and Mario Kart both at 60 fps emulated
on the profiling build; drawn 10–15/s on the heavy scenes. Next: IRAM
placement of the tile writers / UpdateScreen / SetupOBJ, then the
colour-math combine loop.

## 2026-09-15 — article 0004: bring-up GREEN, R38 rework on the bench

Second board of the same order (W2026081721393881), bare: no SD, no
panel, no speaker at first power-on. Bring-up flashed with local esptool
(pipx) and captured with the August recipe.

- **Stage 3: GREEN 48 PASS / 0 FAIL / 11 SKIP**, two consecutive warm
  resets (`art0004-bringup-stage3-run{1,2}-serial-2026-09-15.log`). Same
  baseline as article 0003 pre-peripherals: button RC 706–737 µs, D0–D7
  ~200 ns unloaded, load test +2.0 °C, no brownout. Capture artifact seen
  once: a `BRINGUP;` prefix dropped on the `psram.pattern` line in run 2
  (USB-serial, the SUMMARY still counted it) — not a board finding.
- **R38 rework applied** (1 kΩ + 10 nF at C22 / PAM_IN_AC, per the rework
  sheet) and the 28 mm 8 Ω / 2 W speaker soldered. Post-rework run
  GREEN 48/0/11 (`art0004-bringup-stage5-audio-rework-serial-2026-09-15.log`);
  DC checks on U5: pin 7 = 2.5 V (bias intact after the rework), pin 12 =
  4.8–5 V (not shut down), pins 14–16 = 0–1.6 V AC pulsing with the tone.
- **First "no sound" was the speaker wiring, not the board**: pins 14–16
  read OL with the amp driving; the speaker itself measured 8 Ω before
  fitting. Re-done joints on the SPK pads → audible. SPK pads are two
  unmarked 2×3 mm SMD rectangles 19 mm apart under the speaker (the
  missing ± silk is already a v2 item).
- **R38 verdict: carrier hiss reduced but still present** with 1 kΩ + 10 nF
  (fc ≈ 16 kHz). Next try if it matters: 22 nF (fc ≈ 7 kHz) — the ear
  should not miss anything below that on this speaker.
- Firmware added this session: `audio_play_note()` / `audio_play_melody()`
  (SMB overworld intro) in the production driver, and an opt-in bench
  build of the bring-up (`EXTRA_CFLAGS=-DBRINGUP_TONE_LOOP`) that repeats
  the melody every ~4 s after the report, disabling the PDM channel
  between repeats so the gaps are true silence. The report itself is
  unchanged. Article 0004 is left with this build on it.
