pjcau/esp32-emu-turbo/website/docs/claude-agents.md

---
id: claude-agents
title: Claude Code Agents
sidebar_position: 12
---

# Claude Code Agent Infrastructure

This project uses **Claude Code** as its AI-powered development assistant, with a multi-agent architecture that coordinates PCB design, firmware development, and CAD engineering.

## Architecture Overview

The system uses a **team-lead + 3 specialist agents** model:

```
team-lead (Sonnet) ──── orchestrator, task coordination
  ├── pcb-engineer (Opus) ───── 24 skills, PCB design + manufacturing
  ├── software-dev (Opus) ───── 4 skills, firmware + website
  └── cad-engineer (Haiku) ──── 3 skills, OpenSCAD enclosure

scout (Opus) ──── 1 skill, GitHub pattern discovery (weekly via GitHub Action)
```

### Architecture Graph

```mermaid
graph TB
    TL["TEAM-LEAD<br/><i>sonnet - orchestrator</i>"]

    PCB["PCB-ENGINEER<br/><i>opus - 24 skills</i>"]
    SW["SOFTWARE-DEV<br/><i>opus - 4 skills</i>"]
    CAD["CAD-ENGINEER<br/><i>haiku - 3 skills</i>"]

    TL -->|coordinates| PCB
    TL -->|coordinates| SW
    TL -->|coordinates| CAD

    PCB <-.->|"GPIO sync<br/>config.py - board_config.h"| SW
    PCB <-.->|"dimensions sync<br/>board.py 160x75mm - enclosure.scad"| CAD
    SW <-.->|"docs + renders"| CAD

    subgraph PCB_PIPE["Pipeline 7"]
        s_gen["/generate"]
        s_rel["/release"]
        s_relp["/release-prep"]
        s_frel["/full-release"]
        s_ren["/render"]
        s_pcba["/pcba-render"]
        s_chk["/check"]
    end

    subgraph PCB_VER["Verification 9"]
        s_ver["/verify"]
        s_dfm["/dfm-test"]
        s_drc["/drc-native"]
        s_opt["/pcb-optimize"]
        s_rev["/pcb-review"]
        s_dsv["/datasheet-verify"]
        s_pad["/pad-analysis"]
        s_jalign["/jlcpcb-alignment"]
        s_jval["/jlcpcb-validate"]
    end

    subgraph PCB_FIX["Fix and Debug 4"]
        s_dfix["/dfm-fix"]
        s_frot["/fix-rotation"]
        s_jchk["/jlcpcb-check"]
        s_jpar["/jlcpcb-parts"]
    end

    subgraph PCB_MCP["MCP Design 5"]
        s_sch["/pcb-schematic"]
        s_comp["/pcb-components"]
        s_rout["/pcb-routing"]
        s_lib["/pcb-library"]
        s_brd["/pcb-board"]
    end

    PCB --- PCB_PIPE
    PCB --- PCB_VER
    PCB --- PCB_FIX
    PCB --- PCB_MCP

    subgraph SW_SK["Firmware and Web 4"]
        s_fw["/firmware-build"]
        s_sync["/firmware-sync"]
        s_web["/website-dev"]
        s_doc["/doc"]
    end
    SW --- SW_SK

    subgraph CAD_SK["Enclosure 3"]
        s_edesign["/enclosure-design"]
        s_erender["/enclosure-render"]
        s_eexport["/enclosure-export"]
    end
    CAD --- CAD_SK

    subgraph CROSS["Cross-Agent 1"]
        s_ufb["/user-feedback"]
    end
    TL --- CROSS

    SCOUT["SCOUT<br/>opus - 1 skill<br/>weekly GitHub Action"]
    subgraph SCOUT_SK["Pattern Discovery 1"]
        s_scout["/scout"]
    end
    SCOUT --- SCOUT_SK
    SCOUT -.->|"integrates patterns"| TL

    s_sch ==>|"nets"| s_brd
    s_brd ==>|"outline"| s_comp
    s_comp ==>|"placed"| s_rout
    s_rout ==>|"routed"| s_gen
    s_gen ==>|"PCB ready"| s_ver
    s_ver ==>|"must pass"| s_rel
    s_dfix -->|"fixes then regen"| s_gen
```

### Why This Structure?

- **Isolated contexts**: each agent has its own conversation context, preventing RAM bloat
- **Parallel execution**: independent tasks run simultaneously (e.g., PCB verify + render)
- **Right-sized models**: Haiku for repetitive CAD tasks (cheaper, faster), Opus for complex PCB/firmware reasoning
- **Skill-based dispatch**: 33 skills map to specific workflows, reducing prompt engineering overhead

### Why Opus for PCB and Software?

- **pcb-engineer**: routing with JLCPCB constraints (clearance, drill, annular ring) requires deep multi-step reasoning. DFM violations need root-cause analysis across multiple scripts. Errors cost real money (JLCPCB rework)
- **software-dev**: ESP-IDF firmware involves low-level GPIO, DMA, I2S, SPI debugging. Cross-domain sync (firmware ↔ schematic ↔ PCB) requires broad contextual understanding

## Skills System (33 Skills)

### PCB Engineer — 25 Skills

| Category | Skills | Description |
|---|---|---|
| **Pipeline (7)** | `/generate`, `/release`, `/release-prep`, `/full-release`, `/render`, `/pcba-render`, `/check` | Full PCB generation → JLCPCB export flow |
| **Verification (9)** | `/verify`, `/dfm-test`, `/drc-native`, `/pcb-optimize`, `/pcb-review`, `/datasheet-verify`, `/pad-analysis`, `/jlcpcb-alignment`, `/jlcpcb-validate` | 115 DFM + 9 DFA + 26 JLCPCB tests, DRC checks, layout scoring |
| **Fix & Debug (4)** | `/dfm-fix`, `/fix-rotation`, `/jlcpcb-check`, `/jlcpcb-parts` | Automated issue resolution |
| **MCP Design (5)** | `/pcb-schematic`, `/pcb-components`, `/pcb-routing`, `/pcb-library`, `/pcb-board` | Direct KiCad manipulation via MCP protocol |

**Standard workflow:** `/pcb-schematic` → `/pcb-board` → `/pcb-components` → `/pcb-routing` → `/generate` → `/verify` → `/release`

### Software Dev — 4 Skills

| Skill | Description |
|---|---|
| `/firmware-build` | Build, flash, test ESP-IDF firmware via Docker |
| `/firmware-sync` | Verify GPIO pins match between firmware and schematic |
| `/website-dev` | Develop, build, deploy this Docusaurus website |
| `/doc` | Audit docs against source-of-truth files, fix outdated values |

### CAD Engineer — 3 Skills

| Skill | Description |
|---|---|
| `/enclosure-design` | OpenSCAD parametric enclosure design |
| `/enclosure-render` | Render enclosure views to PNG via Docker |
| `/enclosure-export` | Export STL files for 3D printing |

### Cross-Agent — 1 Skill

| Skill | Description |
|---|---|
| `/user-feedback` | Record user preferences and distribute to agents/memory |

### Scout (Autonomous) — 1 Skill

| Skill | Description |
|---|---|
| `/scout` | Search GitHub for new Claude Code patterns, evaluate relevance, integrate, create PR |

The scout agent runs **autonomously** via a weekly GitHub Action (Monday 02:00 UTC) or on-demand via `/scout`. It searches GitHub for new Claude Code skills, agents, hooks, and CLAUDE.md patterns, evaluates their relevance to this project, and creates PRs with useful integrations.

**State tracking**: `.claude/scout-state.json` persists seen repos and integrated patterns across runs.

## Cross-Agent Dependencies

```
PCB ↔ SW:   config.py ↔ board_config.h   (GPIO pins sync)
PCB ↔ CAD:  board.py 160×75mm ↔ enclosure.scad   (dimensions sync)
SW  ↔ CAD:  website/docs/   (renders + documentation)
```

The `/firmware-sync` skill verifies GPIO consistency between the schematic Python scripts and the C firmware header, preventing hardware/software mismatches.

## Performance Optimizations

### Token Optimization: RTK

[RTK (Rust Token Killer)](https://github.com/rtk-ai/rtk) is a token-optimized CLI proxy that reduces Claude Code token consumption by **60-90%** on dev operations. It works as a transparent hook-based rewriter — commands like `git status` are automatically routed through `rtk git status`, which filters and compresses output before it reaches the LLM context window.

Key features:
- **Zero-config**: hooks rewrite commands transparently, no workflow changes needed
- **Analytics**: `rtk gain` shows cumulative token savings across sessions
- **Discovery**: `rtk discover` analyzes Claude Code history for missed optimization opportunities
- **Rust-native**: minimal overhead, single binary

### Container Runtime: OrbStack

Replaced Docker Desktop with **OrbStack** for dramatically faster container operations:

| Metric | Docker Desktop | OrbStack | Improvement |
|---|---|---|---|
| Container startup | 3.2s | 0.2s | **16x faster** |
| Idle RAM | 2+ GB | ~180 MB | **11x less** |
| Idle CPU | ~5% | ~0.1% | **50x less** |

### Hybrid Local + Docker Pipeline

Instead of running everything inside Docker containers, critical operations use local `kicad-cli` while Docker handles only what requires the full KiCad Python API:

| Operation | All-Docker | Hybrid | Speedup |
|---|---|---|---|
| Full check pipeline | 15-20s | ~5s | **3-4x** |
| Gerber export | 4.7s | 4.0s | 1.2x |
| DFM quick check | N/A | 1.4s | Local only |

### PCB Parse Cache

The `.kicad_pcb` file (~750 KB) was parsed independently by 9 verification scripts using near-identical regex patterns. A centralized cache (`scripts/pcb_cache.py`) now parses once and stores results in `.pcb_cache.json`:

- **Parse once**: canonical parser extracts pads, vias, segments, zones, nets, refs
- **SHA-256 invalidation**: cache auto-rebuilds when `.kicad_pcb` changes
- **Auto-build**: cache is rebuilt automatically after every `make generate-pcb`
- **Lazy loading**: consumers call `load_cache()` (~8ms) instead of parsing (~120ms)

| Metric | Before | After | Improvement |
|---|---|---|---|
| Single script parse | ~120ms | ~8ms load | **93% faster** |
| 9 scripts total parse | ~1000ms | ~190ms (1 parse + 9 loads) | **81% less** |
| `make verify-all` | ~3.0s | 0.11s | **27x faster** |

### Parallel Execution

Build and verification targets run in parallel where possible:

- **`verify-all`**: 6 Python verification scripts run simultaneously (DFM + DFA + DRC + sim + consistency + short-circuit)
- **`render-all`**: schematics, enclosure, and PCB renders run in parallel (~8s vs ~20s)
- **Docker cached builds**: skip rebuild when images are unchanged (0s vs 15-20s)

### Session Management

Claude Code conversation history can grow to gigabytes over time. Our management strategy:

| Strategy | Impact |
|---|---|
| Max session length: 1-2 hours | Prevents context window bloat |
| Weekly session archive (>7 days) | Reduced from 1.4 GB to ~100 MB |
| Subagent delegation | Isolates heavy work from main context |
| Max 3 concurrent subagents | Prevents API contention |

## Automated Guards (Hooks)

Hooks run automatically to prevent workflow errors (committed in `.claude/settings.json`):

| Trigger | Condition | Action |
|---|---|---|
| After `Bash` | Command contains `generate_pcb` | Reminds to run DFM verification |
| After `Edit` | File path in `scripts/generate_pcb/` | Reminds to regenerate PCB |
| After `Edit` | PCB/PCBA file modified | Reminds to run DFA verification |
| After `Write` | PCB/PCBA file modified | Reminds to run DFA verification |
| **Pre-commit** | PCB files staged | Runs `make verify-fast` (blocks commit on failure) |

These prevent common mistakes: editing PCB generation scripts without regenerating and re-verifying.

## Anti-Stall Protocol

Rules that prevent agents from getting stuck in loops:

1. **Max 3 failed attempts** per approach — then change strategy
2. **Max 4 steps per agent task** — split larger tasks into sub-tasks
3. **Verify after each fix** — regenerate + analyze after every change
4. **User feedback every 2-3 minutes** during long tasks
5. **Kill stalled agents after 5 minutes** — relaunch with narrower scope
6. **Analytical over heuristic** — always parse actual files, never guess

## Makefile Quick Reference

| Target | Time | Description |
|---|---|---|
| `make verify-fast` | ~1.5s | Quick DFM check (115 tests) |
| `make verify-dfa` | ~1.1s | Quick DFA check (9 assembly tests) |
| `make verify-all` | ~1.6s | All verification checks (DFM + DFA + DRC + sim + consistency) |
| `make fast-check` | ~5s | Full pipeline (local kicad-cli) |
| `make render-all` | ~8s | Full render pipeline (parallel) |
| `make release-prep` | ~15s | Generate → gerbers → verify → render |
| `make firmware-sync-check` | under 1s | GPIO sync verification |
