pjcau/esp32-emu-turbo/hardware/enclosure/preview-v3/back.png

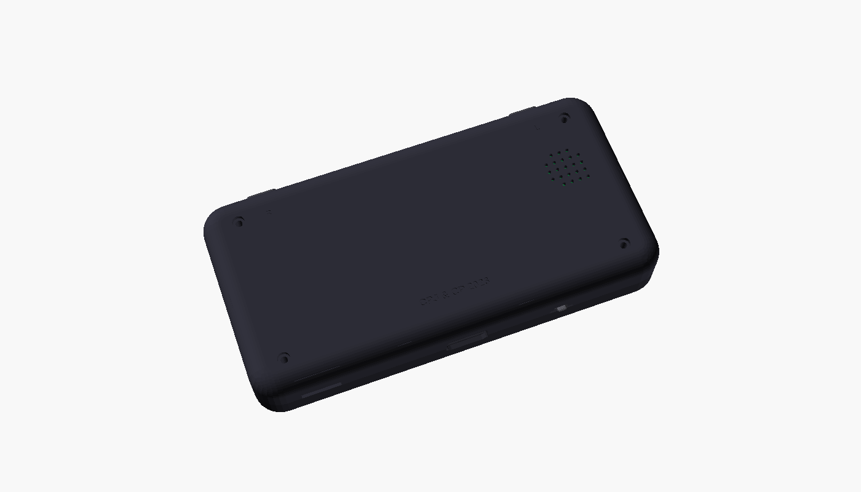
hardware/enclosure/preview-v3/back.png
