pjcau/esp32-emu-turbo/hardware/enclosure/preview-v3/exploded.png

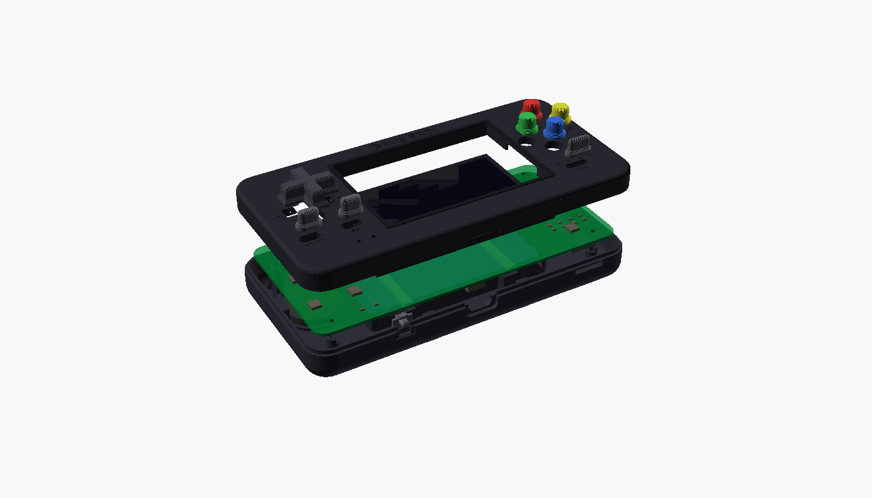
hardware/enclosure/preview-v3/exploded.png
