pjcau/esp32-emu-turbo/hardware/enclosure/preview-v3/leva-3d.png

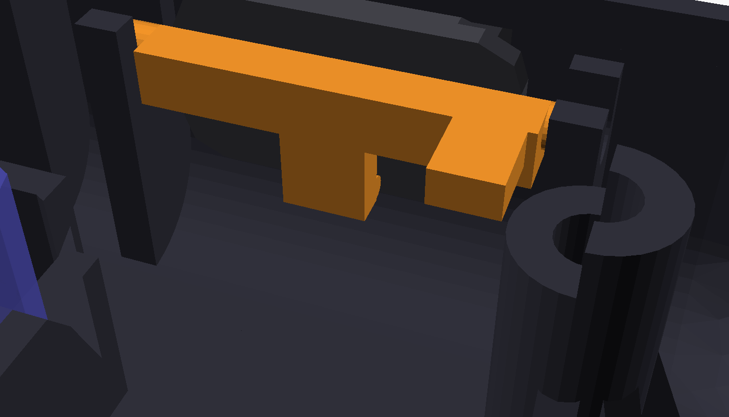
hardware/enclosure/preview-v3/leva-3d.png
