pjcau/esp32-emu-turbo/hardware/enclosure/preview-v3/lr-detail.png

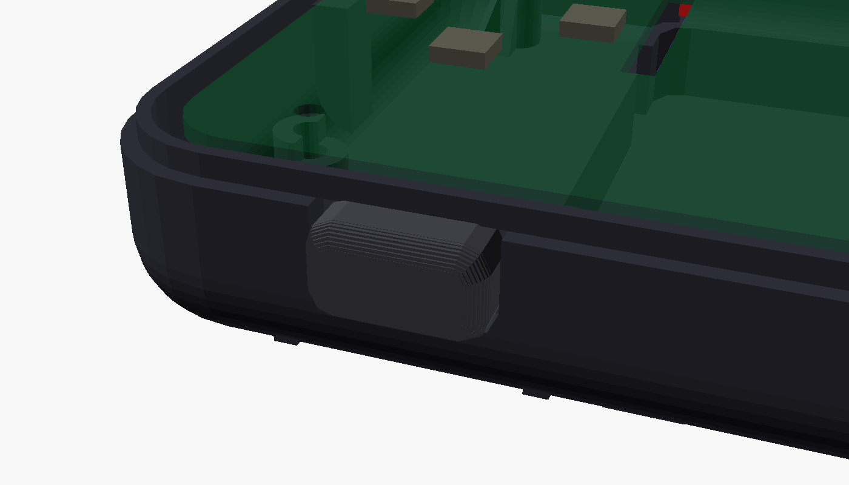
hardware/enclosure/preview-v3/lr-detail.png
