pjcau/esp32-emu-turbo/hardware/enclosure/preview-v3/meccanismo-lr-giro.gif

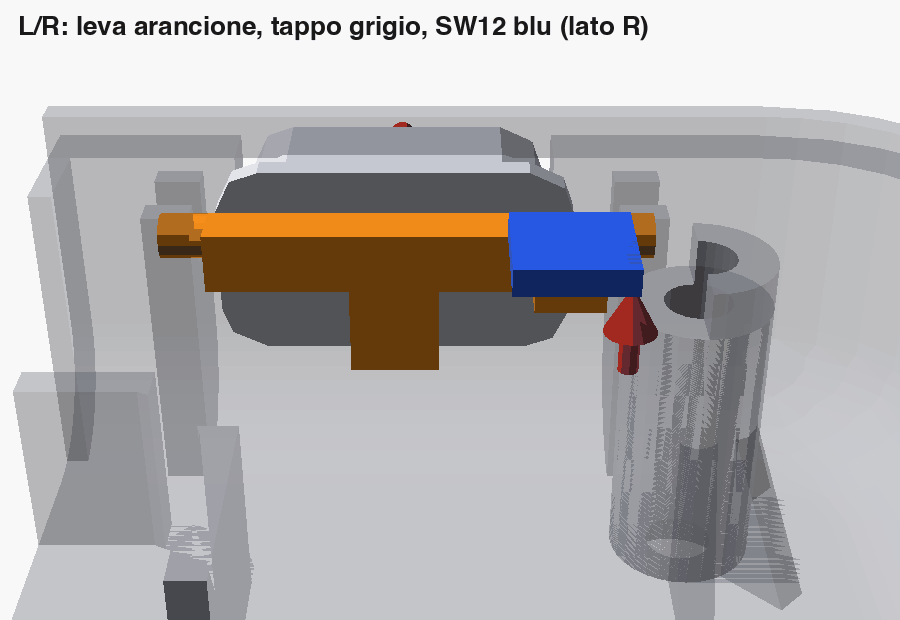
hardware/enclosure/preview-v3/meccanismo-lr-giro.gif
