pjcau/esp32-emu-turbo/hardware/enclosure/preview-v3/pwr-detail.png

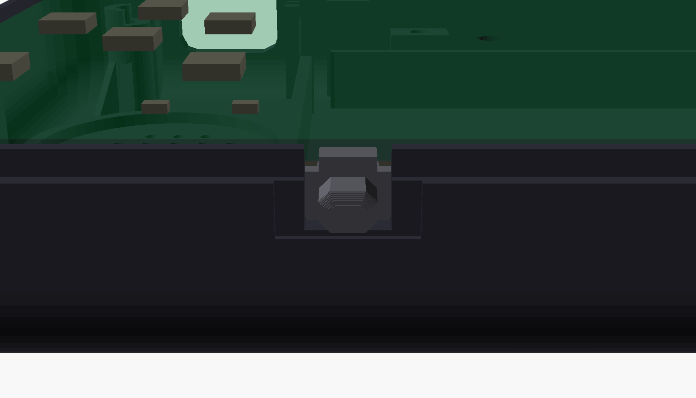
hardware/enclosure/preview-v3/pwr-detail.png
