pjcau/esp32-emu-turbo/hardware/enclosure/preview-v3/xsec.png

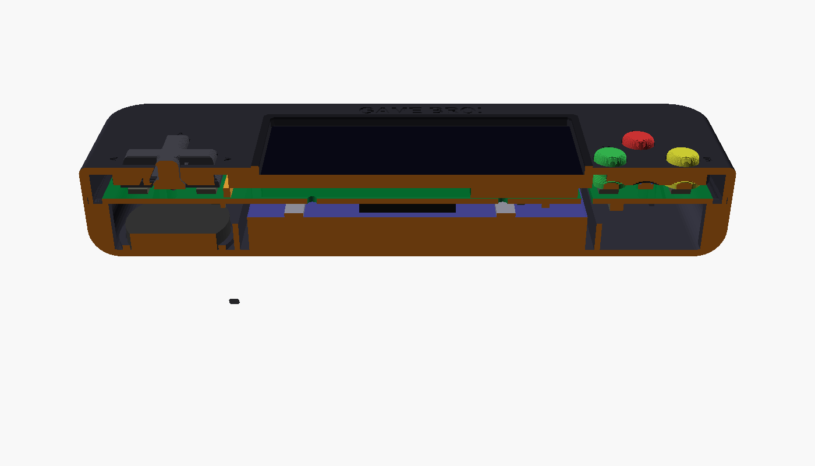
hardware/enclosure/preview-v3/xsec.png
