pjcau/esp32-emu-turbo/hardware/first-article/v4.9.0-W2026081721393881/IMG_5901.jpeg

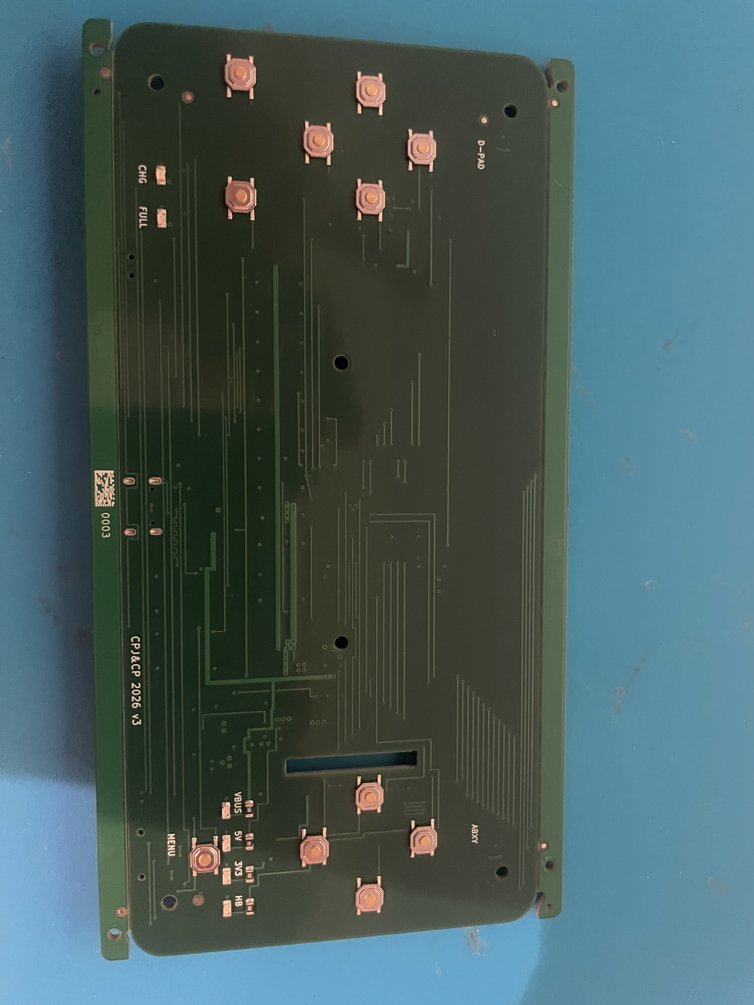
hardware/first-article/v4.9.0-W2026081721393881/IMG_5901.jpeg
