pjcau/esp32-emu-turbo/hardware/enclosure/preview-v3/parts.png

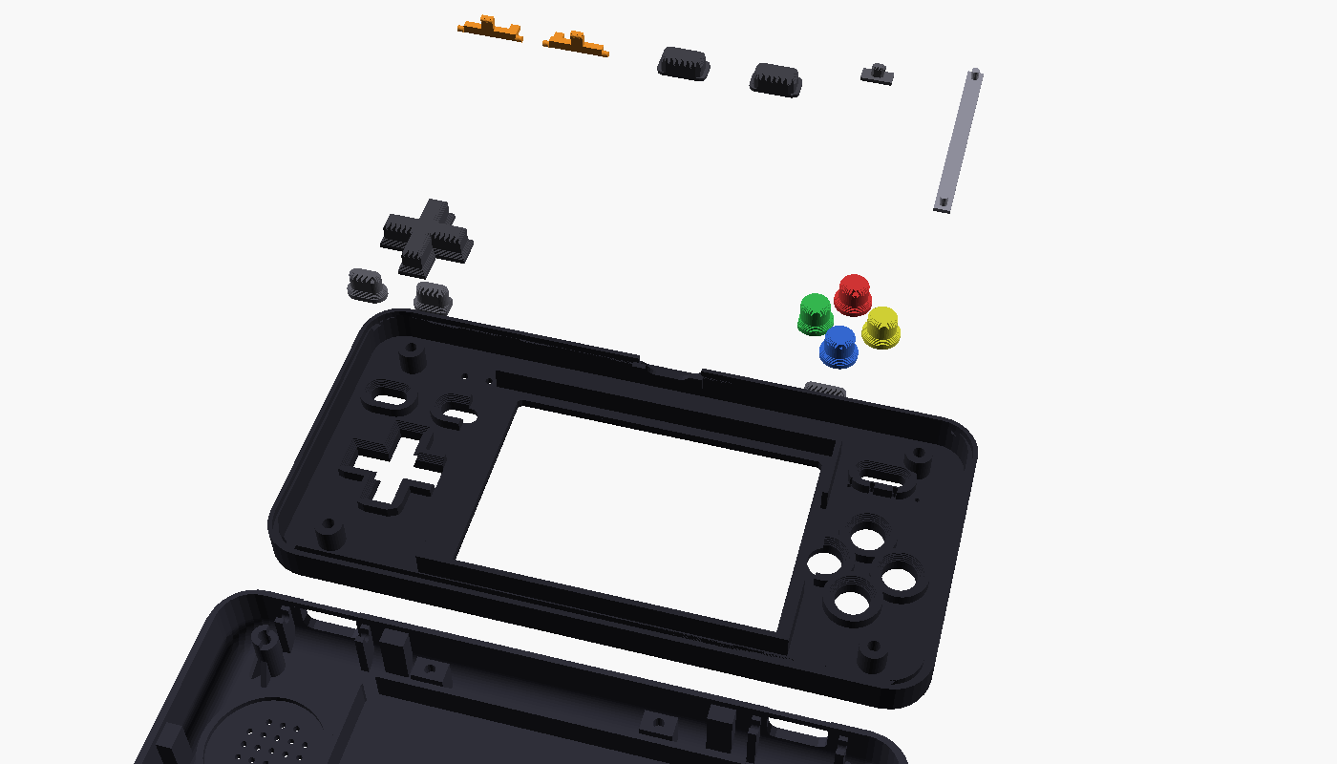
hardware/enclosure/preview-v3/parts.png
