pjcau/esp32-emu-turbo/hardware/enclosure/reference/part_btn_y.stl

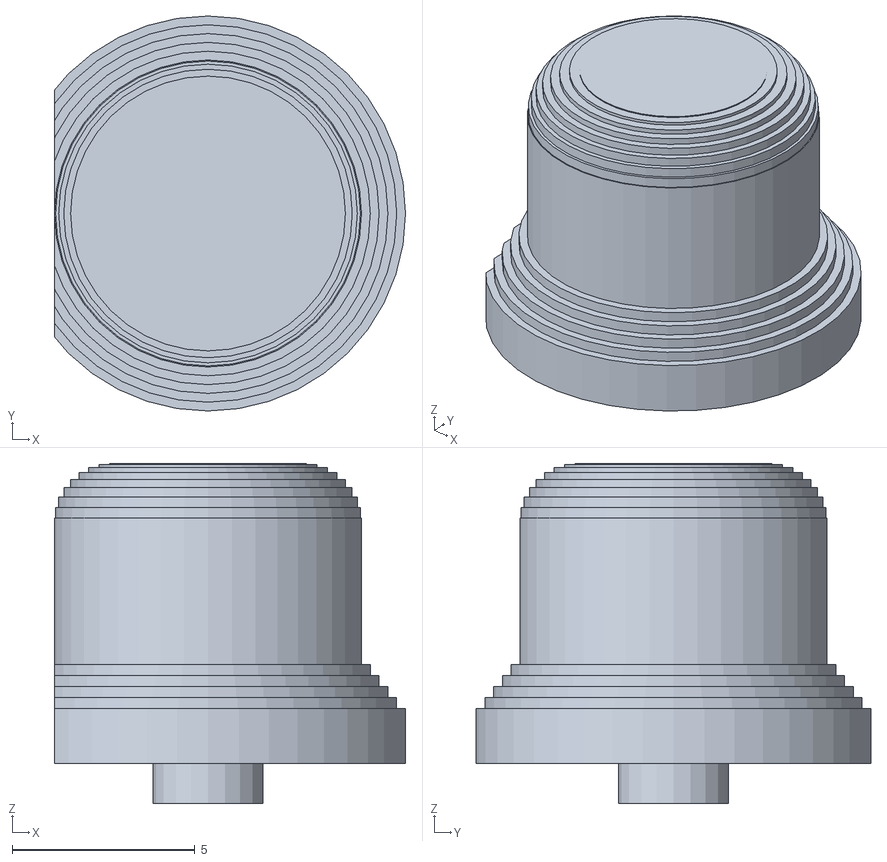
[picture p79: CAD file, 2026-10-10]
hardware/enclosure/reference/part_btn_y.stl
9.60 x 10.8 x 9.31
