pjcau/esp32-emu-turbo/hardware/enclosure/reference/part_straps.stl

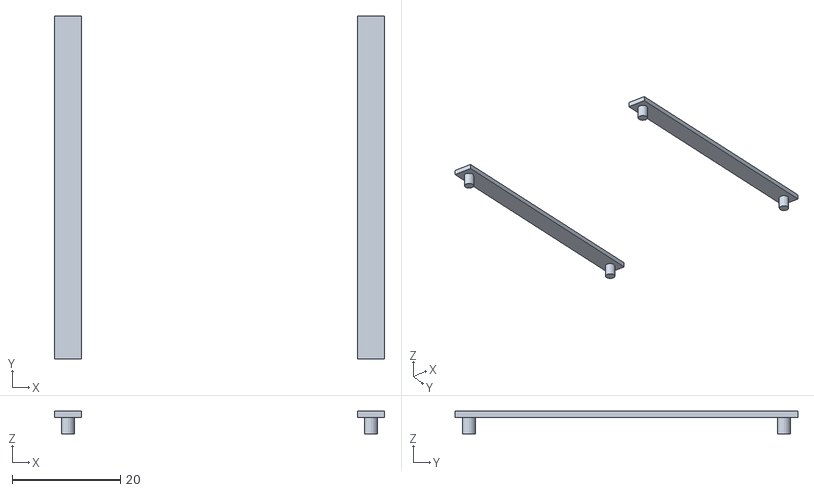
[picture p80: CAD file, 2026-10-10]
hardware/enclosure/reference/part_straps.stl
61.0 x 63.4 x 4.20
