pjcau/esp32-emu-turbo/3d_case/case_bottom.stl

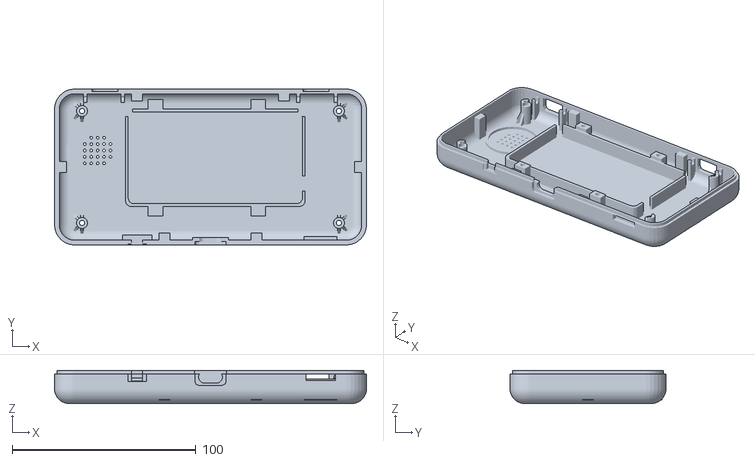
[picture p81: CAD file, 2026-10-10]
3d_case/case_bottom.stl
170.0 x 85.0 x 18.0
