pjcau/esp32-emu-turbo/hardware/enclosure/preview-v3/pwr-guide.png

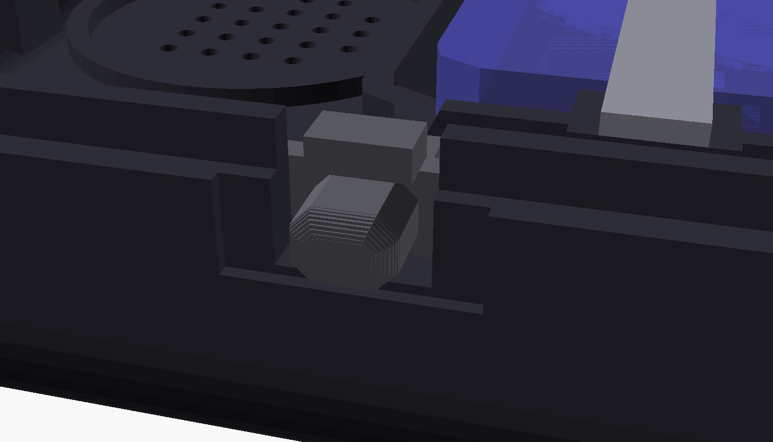
hardware/enclosure/preview-v3/pwr-guide.png
