pjcau/esp32-emu-turbo/website/docs/manufacturing/production-test-map.md

---
id: production-test-map
title: Production Test Map
sidebar_position: 4
---

# Production Test Map

**99 automated gates** stand between `make generate` and a JLCPCB order.
This page is the picture of them: what each one prevents, how the EMC surface
is covered, and how the network grew release by release.

:::info Source of truth
The roster below is `VERIFY_ALL_SCRIPTS` in the `Makefile` (95 gates) plus the
4 EMC gates being registered now. Severity is not editorial — it is what
`scripts/issue_dispatch.py` assigns each gate through its routing law.
:::

---

## A. Production test coverage map

### Severity ranking

<div style={{display: "flex", flexWrap: "wrap", gap: "0.5rem", margin: "1rem 0 1.5rem"}}>
<div style={{flex: "1 1 220px", display: "flex", gap: "0.5rem", alignItems: "flex-start", padding: "0.5rem 0.65rem", borderRadius: "8px", background: "#a855f71a", border: "1px solid #a855f755"}}><span style={{width: "10px", height: "10px", borderRadius: "50%", background: "#a855f7", marginTop: "0.32rem", flexShrink: 0}} /><span><strong style={{fontSize: "0.85rem"}}>blind-spot</strong><br /><span style={{fontSize: "0.75rem", opacity: 0.75}}>the gate network itself is broken, so no other verdict is trustworthy</span></span></div>
<div style={{flex: "1 1 220px", display: "flex", gap: "0.5rem", alignItems: "flex-start", padding: "0.5rem 0.65rem", borderRadius: "8px", background: "#ef44441a", border: "1px solid #ef444455"}}><span style={{width: "10px", height: "10px", borderRadius: "50%", background: "#ef4444", marginTop: "0.32rem", flexShrink: 0}} /><span><strong style={{fontSize: "0.85rem"}}>dead-board</strong><br /><span style={{fontSize: "0.75rem", opacity: 0.75}}>the board does not work, or is assembled wrong</span></span></div>
<div style={{flex: "1 1 220px", display: "flex", gap: "0.5rem", alignItems: "flex-start", padding: "0.5rem 0.65rem", borderRadius: "8px", background: "#f59e0b1a", border: "1px solid #f59e0b55"}}><span style={{width: "10px", height: "10px", borderRadius: "50%", background: "#f59e0b", marginTop: "0.32rem", flexShrink: 0}} /><span><strong style={{fontSize: "0.85rem"}}>degraded</strong><br /><span style={{fontSize: "0.75rem", opacity: 0.75}}>it works, but out of spec — margin, heat, EMC</span></span></div>
<div style={{flex: "1 1 220px", display: "flex", gap: "0.5rem", alignItems: "flex-start", padding: "0.5rem 0.65rem", borderRadius: "8px", background: "#94a3b81a", border: "1px solid #94a3b855"}}><span style={{width: "10px", height: "10px", borderRadius: "50%", background: "#94a3b8", marginTop: "0.32rem", flexShrink: 0}} /><span><strong style={{fontSize: "0.85rem"}}>cosmetic</strong><br /><span style={{fontSize: "0.75rem", opacity: 0.75}}>documentation and rendering only</span></span></div>
</div>

### Pipeline

Production test pipeline: eight gate stages between make generate and the JLCPCB order

<p style={{fontSize: "0.8rem", opacity: 0.7, marginTop: "-0.5rem"}}>
Stage colour = the severity most of its gates carry. Individual gates vary — the roster below is per-gate.
</p>

### The 99 gates

<div style={{margin: "1.25rem 0"}}>
<div style={{display: "flex", alignItems: "baseline", gap: "0.6rem", flexWrap: "wrap", marginBottom: "0.35rem"}}>
<strong style={{fontSize: "1.02rem"}}>Source sync</strong>
<code style={{fontSize: "0.78rem"}}>11 gates</code>
<span style={{fontSize: "0.85rem", opacity: 0.75}}>Does the copper still match the drawing?</span>
</div>
<div style={{display: "flex", flexWrap: "wrap", gap: "0.3rem"}}>
<span title="blind-spot" style={{display: "inline-flex", alignItems: "center", gap: "0.3rem", padding: "0.15rem 0.5rem", borderRadius: "999px", fontSize: "0.74rem", fontFamily: "var(--ifm-font-family-monospace)", background: "#a855f722", border: "1px solid #a855f777"}}><span style={{width: "6px", height: "6px", borderRadius: "50%", background: "#a855f7", flexShrink: 0}} />test_enclosure_sync</span>
<span title="degraded" style={{display: "inline-flex", alignItems: "center", gap: "0.3rem", padding: "0.15rem 0.5rem", borderRadius: "999px", fontSize: "0.74rem", fontFamily: "var(--ifm-font-family-monospace)", background: "#f59e0b22", border: "1px solid #f59e0b77"}}><span style={{width: "6px", height: "6px", borderRadius: "50%", background: "#f59e0b", flexShrink: 0}} />verify_enclosure_sync</span>
<span title="dead-board" style={{display: "inline-flex", alignItems: "center", gap: "0.3rem", padding: "0.15rem 0.5rem", borderRadius: "999px", fontSize: "0.74rem", fontFamily: "var(--ifm-font-family-monospace)", background: "#ef444422", border: "1px solid #ef444477"}}><span style={{width: "6px", height: "6px", borderRadius: "50%", background: "#ef4444", flexShrink: 0}} />verify_firmware_retrogo_sync</span>
<span title="dead-board" style={{display: "inline-flex", alignItems: "center", gap: "0.3rem", padding: "0.15rem 0.5rem", borderRadius: "999px", fontSize: "0.74rem", fontFamily: "var(--ifm-font-family-monospace)", background: "#ef444422", border: "1px solid #ef444477"}}><span style={{width: "6px", height: "6px", borderRadius: "50%", background: "#ef4444", flexShrink: 0}} />verify_netlist_diff</span>
<span title="dead-board" style={{display: "inline-flex", alignItems: "center", gap: "0.3rem", padding: "0.15rem 0.5rem", borderRadius: "999px", fontSize: "0.74rem", fontFamily: "var(--ifm-font-family-monospace)", background: "#ef444422", border: "1px solid #ef444477"}}><span style={{width: "6px", height: "6px", borderRadius: "50%", background: "#ef4444", flexShrink: 0}} />verify_netlist_vs_kicad</span>
<span title="dead-board" style={{display: "inline-flex", alignItems: "center", gap: "0.3rem", padding: "0.15rem 0.5rem", borderRadius: "999px", fontSize: "0.74rem", fontFamily: "var(--ifm-font-family-monospace)", background: "#ef444422", border: "1px solid #ef444477"}}><span style={{width: "6px", height: "6px", borderRadius: "50%", background: "#ef4444", flexShrink: 0}} />verify_schematic_crossings</span>
<span title="dead-board" style={{display: "inline-flex", alignItems: "center", gap: "0.3rem", padding: "0.15rem 0.5rem", borderRadius: "999px", fontSize: "0.74rem", fontFamily: "var(--ifm-font-family-monospace)", background: "#ef444422", border: "1px solid #ef444477"}}><span style={{width: "6px", height: "6px", borderRadius: "50%", background: "#ef4444", flexShrink: 0}} />verify_schematic_label_attach</span>
<span title="dead-board" style={{display: "inline-flex", alignItems: "center", gap: "0.3rem", padding: "0.15rem 0.5rem", borderRadius: "999px", fontSize: "0.74rem", fontFamily: "var(--ifm-font-family-monospace)", background: "#ef444422", border: "1px solid #ef444477"}}><span style={{width: "6px", height: "6px", borderRadius: "50%", background: "#ef4444", flexShrink: 0}} />verify_schematic_overlaps</span>
<span title="dead-board" style={{display: "inline-flex", alignItems: "center", gap: "0.3rem", padding: "0.15rem 0.5rem", borderRadius: "999px", fontSize: "0.74rem", fontFamily: "var(--ifm-font-family-monospace)", background: "#ef444422", border: "1px solid #ef444477"}}><span style={{width: "6px", height: "6px", borderRadius: "50%", background: "#ef4444", flexShrink: 0}} />verify_schematic_pcb</span>
<span title="dead-board" style={{display: "inline-flex", alignItems: "center", gap: "0.3rem", padding: "0.15rem 0.5rem", borderRadius: "999px", fontSize: "0.74rem", fontFamily: "var(--ifm-font-family-monospace)", background: "#ef444422", border: "1px solid #ef444477"}}><span style={{width: "6px", height: "6px", borderRadius: "50%", background: "#ef4444", flexShrink: 0}} />verify_schematic_pcb_sync</span>
<span title="dead-board" style={{display: "inline-flex", alignItems: "center", gap: "0.3rem", padding: "0.15rem 0.5rem", borderRadius: "999px", fontSize: "0.74rem", fontFamily: "var(--ifm-font-family-monospace)", background: "#ef444422", border: "1px solid #ef444477"}}><span style={{width: "6px", height: "6px", borderRadius: "50%", background: "#ef4444", flexShrink: 0}} />verify_schematic_pin_connectivity</span>
</div>
</div>

<div style={{margin: "1.25rem 0"}}>
<div style={{display: "flex", alignItems: "baseline", gap: "0.6rem", flexWrap: "wrap", marginBottom: "0.35rem"}}>
<strong style={{fontSize: "1.02rem"}}>Copper integrity</strong>
<code style={{fontSize: "0.78rem"}}>14 gates</code>
<span style={{fontSize: "0.85rem", opacity: 0.75}}>Is every net one piece of copper, and nothing else touching it?</span>
</div>
<div style={{display: "flex", flexWrap: "wrap", gap: "0.3rem"}}>
<span title="dead-board" style={{display: "inline-flex", alignItems: "center", gap: "0.3rem", padding: "0.15rem 0.5rem", borderRadius: "999px", fontSize: "0.74rem", fontFamily: "var(--ifm-font-family-monospace)", background: "#ef444422", border: "1px solid #ef444477"}}><span style={{width: "6px", height: "6px", borderRadius: "50%", background: "#ef4444", flexShrink: 0}} />short_circuit_analysis</span>
<span title="blind-spot" style={{display: "inline-flex", alignItems: "center", gap: "0.3rem", padding: "0.15rem 0.5rem", borderRadius: "999px", fontSize: "0.74rem", fontFamily: "var(--ifm-font-family-monospace)", background: "#a855f722", border: "1px solid #a855f777"}}><span style={{width: "6px", height: "6px", borderRadius: "50%", background: "#a855f7", flexShrink: 0}} />test_collision_pad_nets</span>
<span title="blind-spot" style={{display: "inline-flex", alignItems: "center", gap: "0.3rem", padding: "0.15rem 0.5rem", borderRadius: "999px", fontSize: "0.74rem", fontFamily: "var(--ifm-font-family-monospace)", background: "#a855f722", border: "1px solid #a855f777"}}><span style={{width: "6px", height: "6px", borderRadius: "50%", background: "#a855f7", flexShrink: 0}} />test_collision_via_metric</span>
<span title="dead-board" style={{display: "inline-flex", alignItems: "center", gap: "0.3rem", padding: "0.15rem 0.5rem", borderRadius: "999px", fontSize: "0.74rem", fontFamily: "var(--ifm-font-family-monospace)", background: "#ef444422", border: "1px solid #ef444477"}}><span style={{width: "6px", height: "6px", borderRadius: "50%", background: "#ef4444", flexShrink: 0}} />test_pcb_connectivity</span>
<span title="dead-board" style={{display: "inline-flex", alignItems: "center", gap: "0.3rem", padding: "0.15rem 0.5rem", borderRadius: "999px", fontSize: "0.74rem", fontFamily: "var(--ifm-font-family-monospace)", background: "#ef444422", border: "1px solid #ef444477"}}><span style={{width: "6px", height: "6px", borderRadius: "50%", background: "#ef4444", flexShrink: 0}} />test_power_net_integrity</span>
<span title="dead-board" style={{display: "inline-flex", alignItems: "center", gap: "0.3rem", padding: "0.15rem 0.5rem", borderRadius: "999px", fontSize: "0.74rem", fontFamily: "var(--ifm-font-family-monospace)", background: "#ef444422", border: "1px solid #ef444477"}}><span style={{width: "6px", height: "6px", borderRadius: "50%", background: "#ef4444", flexShrink: 0}} />verify_component_connectivity</span>
<span title="dead-board" style={{display: "inline-flex", alignItems: "center", gap: "0.3rem", padding: "0.15rem 0.5rem", borderRadius: "999px", fontSize: "0.74rem", fontFamily: "var(--ifm-font-family-monospace)", background: "#ef444422", border: "1px solid #ef444477"}}><span style={{width: "6px", height: "6px", borderRadius: "50%", background: "#ef4444", flexShrink: 0}} />verify_dangling_copper</span>
<span title="dead-board" style={{display: "inline-flex", alignItems: "center", gap: "0.3rem", padding: "0.15rem 0.5rem", borderRadius: "999px", fontSize: "0.74rem", fontFamily: "var(--ifm-font-family-monospace)", background: "#ef444422", border: "1px solid #ef444477"}}><span style={{width: "6px", height: "6px", borderRadius: "50%", background: "#ef4444", flexShrink: 0}} />verify_isolation</span>
<span title="dead-board" style={{display: "inline-flex", alignItems: "center", gap: "0.3rem", padding: "0.15rem 0.5rem", borderRadius: "999px", fontSize: "0.74rem", fontFamily: "var(--ifm-font-family-monospace)", background: "#ef444422", border: "1px solid #ef444477"}}><span style={{width: "6px", height: "6px", borderRadius: "50%", background: "#ef4444", flexShrink: 0}} />verify_net_connectivity</span>
<span title="dead-board" style={{display: "inline-flex", alignItems: "center", gap: "0.3rem", padding: "0.15rem 0.5rem", borderRadius: "999px", fontSize: "0.74rem", fontFamily: "var(--ifm-font-family-monospace)", background: "#ef444422", border: "1px solid #ef444477"}}><span style={{width: "6px", height: "6px", borderRadius: "50%", background: "#ef4444", flexShrink: 0}} />verify_power_net_integrity</span>
<span title="degraded" style={{display: "inline-flex", alignItems: "center", gap: "0.3rem", padding: "0.15rem 0.5rem", borderRadius: "999px", fontSize: "0.74rem", fontFamily: "var(--ifm-font-family-monospace)", background: "#f59e0b22", border: "1px solid #f59e0b77"}}><span style={{width: "6px", height: "6px", borderRadius: "50%", background: "#f59e0b", flexShrink: 0}} />verify_trace_crossings</span>
<span title="dead-board" style={{display: "inline-flex", alignItems: "center", gap: "0.3rem", padding: "0.15rem 0.5rem", borderRadius: "999px", fontSize: "0.74rem", fontFamily: "var(--ifm-font-family-monospace)", background: "#ef444422", border: "1px solid #ef444477"}}><span style={{width: "6px", height: "6px", borderRadius: "50%", background: "#ef4444", flexShrink: 0}} />verify_trace_through_pad</span>
<span title="dead-board" style={{display: "inline-flex", alignItems: "center", gap: "0.3rem", padding: "0.15rem 0.5rem", borderRadius: "999px", fontSize: "0.74rem", fontFamily: "var(--ifm-font-family-monospace)", background: "#ef444422", border: "1px solid #ef444477"}}><span style={{width: "6px", height: "6px", borderRadius: "50%", background: "#ef4444", flexShrink: 0}} />verify_zone_connectivity</span>
<span title="dead-board" style={{display: "inline-flex", alignItems: "center", gap: "0.3rem", padding: "0.15rem 0.5rem", borderRadius: "999px", fontSize: "0.74rem", fontFamily: "var(--ifm-font-family-monospace)", background: "#ef444422", border: "1px solid #ef444477"}}><span style={{width: "6px", height: "6px", borderRadius: "50%", background: "#ef4444", flexShrink: 0}} />verify_zone_fill_sanity</span>
</div>
</div>

<div style={{margin: "1.25rem 0"}}>
<div style={{display: "flex", alignItems: "baseline", gap: "0.6rem", flexWrap: "wrap", marginBottom: "0.35rem"}}>
<strong style={{fontSize: "1.02rem"}}>Fabrication</strong>
<code style={{fontSize: "0.78rem"}}>14 gates</code>
<span style={{fontSize: "0.85rem", opacity: 0.75}}>Will the fab build it as drawn, without silently correcting it?</span>
</div>
<div style={{display: "flex", flexWrap: "wrap", gap: "0.3rem"}}>
<span title="dead-board" style={{display: "inline-flex", alignItems: "center", gap: "0.3rem", padding: "0.15rem 0.5rem", borderRadius: "999px", fontSize: "0.74rem", fontFamily: "var(--ifm-font-family-monospace)", background: "#ef444422", border: "1px solid #ef444477"}}><span style={{width: "6px", height: "6px", borderRadius: "50%", background: "#ef4444", flexShrink: 0}} />analyze_pad_distances</span>
<span title="dead-board" style={{display: "inline-flex", alignItems: "center", gap: "0.3rem", padding: "0.15rem 0.5rem", borderRadius: "999px", fontSize: "0.74rem", fontFamily: "var(--ifm-font-family-monospace)", background: "#ef444422", border: "1px solid #ef444477"}}><span style={{width: "6px", height: "6px", borderRadius: "50%", background: "#ef4444", flexShrink: 0}} />drc_check</span>
<span title="dead-board" style={{display: "inline-flex", alignItems: "center", gap: "0.3rem", padding: "0.15rem 0.5rem", borderRadius: "999px", fontSize: "0.74rem", fontFamily: "var(--ifm-font-family-monospace)", background: "#ef444422", border: "1px solid #ef444477"}}><span style={{width: "6px", height: "6px", borderRadius: "50%", background: "#ef4444", flexShrink: 0}} />validate_jlcpcb</span>
<span title="degraded" style={{display: "inline-flex", alignItems: "center", gap: "0.3rem", padding: "0.15rem 0.5rem", borderRadius: "999px", fontSize: "0.74rem", fontFamily: "var(--ifm-font-family-monospace)", background: "#f59e0b22", border: "1px solid #f59e0b77"}}><span style={{width: "6px", height: "6px", borderRadius: "50%", background: "#f59e0b", flexShrink: 0}} />verify_copper_balance</span>
<span title="dead-board" style={{display: "inline-flex", alignItems: "center", gap: "0.3rem", padding: "0.15rem 0.5rem", borderRadius: "999px", fontSize: "0.74rem", fontFamily: "var(--ifm-font-family-monospace)", background: "#ef444422", border: "1px solid #ef444477"}}><span style={{width: "6px", height: "6px", borderRadius: "50%", background: "#ef4444", flexShrink: 0}} />verify_copper_clearance</span>
<span title="dead-board" style={{display: "inline-flex", alignItems: "center", gap: "0.3rem", padding: "0.15rem 0.5rem", borderRadius: "999px", fontSize: "0.74rem", fontFamily: "var(--ifm-font-family-monospace)", background: "#ef444422", border: "1px solid #ef444477"}}><span style={{width: "6px", height: "6px", borderRadius: "50%", background: "#ef4444", flexShrink: 0}} />verify_dfm_v2</span>
<span title="dead-board" style={{display: "inline-flex", alignItems: "center", gap: "0.3rem", padding: "0.15rem 0.5rem", borderRadius: "999px", fontSize: "0.74rem", fontFamily: "var(--ifm-font-family-monospace)", background: "#ef444422", border: "1px solid #ef444477"}}><span style={{width: "6px", height: "6px", borderRadius: "50%", background: "#ef4444", flexShrink: 0}} />verify_drill_standards</span>
<span title="dead-board" style={{display: "inline-flex", alignItems: "center", gap: "0.3rem", padding: "0.15rem 0.5rem", borderRadius: "999px", fontSize: "0.74rem", fontFamily: "var(--ifm-font-family-monospace)", background: "#ef444422", border: "1px solid #ef444477"}}><span style={{width: "6px", height: "6px", borderRadius: "50%", background: "#ef4444", flexShrink: 0}} />verify_gerber_integrity</span>
<span title="dead-board" style={{display: "inline-flex", alignItems: "center", gap: "0.3rem", padding: "0.15rem 0.5rem", borderRadius: "999px", fontSize: "0.74rem", fontFamily: "var(--ifm-font-family-monospace)", background: "#ef444422", border: "1px solid #ef444477"}}><span style={{width: "6px", height: "6px", borderRadius: "50%", background: "#ef4444", flexShrink: 0}} />verify_jlcpcb_capabilities</span>
<span title="dead-board" style={{display: "inline-flex", alignItems: "center", gap: "0.3rem", padding: "0.15rem 0.5rem", borderRadius: "999px", fontSize: "0.74rem", fontFamily: "var(--ifm-font-family-monospace)", background: "#ef444422", border: "1px solid #ef444477"}}><span style={{width: "6px", height: "6px", borderRadius: "50%", background: "#ef4444", flexShrink: 0}} />verify_jlcpcb_via_rules</span>
<span title="degraded" style={{display: "inline-flex", alignItems: "center", gap: "0.3rem", padding: "0.15rem 0.5rem", borderRadius: "999px", fontSize: "0.74rem", fontFamily: "var(--ifm-font-family-monospace)", background: "#f59e0b22", border: "1px solid #f59e0b77"}}><span style={{width: "6px", height: "6px", borderRadius: "50%", background: "#f59e0b", flexShrink: 0}} />verify_net_class_widths</span>
<span title="degraded" style={{display: "inline-flex", alignItems: "center", gap: "0.3rem", padding: "0.15rem 0.5rem", borderRadius: "999px", fontSize: "0.74rem", fontFamily: "var(--ifm-font-family-monospace)", background: "#f59e0b22", border: "1px solid #f59e0b77"}}><span style={{width: "6px", height: "6px", borderRadius: "50%", background: "#f59e0b", flexShrink: 0}} />verify_stackup</span>
<span title="degraded" style={{display: "inline-flex", alignItems: "center", gap: "0.3rem", padding: "0.15rem 0.5rem", borderRadius: "999px", fontSize: "0.74rem", fontFamily: "var(--ifm-font-family-monospace)", background: "#f59e0b22", border: "1px solid #f59e0b77"}}><span style={{width: "6px", height: "6px", borderRadius: "50%", background: "#f59e0b", flexShrink: 0}} />verify_thermal_relief</span>
<span title="dead-board" style={{display: "inline-flex", alignItems: "center", gap: "0.3rem", padding: "0.15rem 0.5rem", borderRadius: "999px", fontSize: "0.74rem", fontFamily: "var(--ifm-font-family-monospace)", background: "#ef444422", border: "1px solid #ef444477"}}><span style={{width: "6px", height: "6px", borderRadius: "50%", background: "#ef4444", flexShrink: 0}} />verify_via_in_pad</span>
</div>
</div>

<div style={{margin: "1.25rem 0"}}>
<div style={{display: "flex", alignItems: "baseline", gap: "0.6rem", flexWrap: "wrap", marginBottom: "0.35rem"}}>
<strong style={{fontSize: "1.02rem"}}>Assembly</strong>
<code style={{fontSize: "0.78rem"}}>13 gates</code>
<span style={{fontSize: "0.85rem", opacity: 0.75}}>Will the pick-and-place put the right part down the right way round?</span>
</div>
<div style={{display: "flex", flexWrap: "wrap", gap: "0.3rem"}}>
<span title="dead-board" style={{display: "inline-flex", alignItems: "center", gap: "0.3rem", padding: "0.15rem 0.5rem", borderRadius: "999px", fontSize: "0.74rem", fontFamily: "var(--ifm-font-family-monospace)", background: "#ef444422", border: "1px solid #ef444477"}}><span style={{width: "6px", height: "6px", borderRadius: "50%", background: "#ef4444", flexShrink: 0}} />test_cpl_rotation_law</span>
<span title="blind-spot" style={{display: "inline-flex", alignItems: "center", gap: "0.3rem", padding: "0.15rem 0.5rem", borderRadius: "999px", fontSize: "0.74rem", fontFamily: "var(--ifm-font-family-monospace)", background: "#a855f722", border: "1px solid #a855f777"}}><span style={{width: "6px", height: "6px", borderRadius: "50%", background: "#a855f7", flexShrink: 0}} />test_test_points</span>
<span title="dead-board" style={{display: "inline-flex", alignItems: "center", gap: "0.3rem", padding: "0.15rem 0.5rem", borderRadius: "999px", fontSize: "0.74rem", fontFamily: "var(--ifm-font-family-monospace)", background: "#ef444422", border: "1px solid #ef444477"}}><span style={{width: "6px", height: "6px", borderRadius: "50%", background: "#ef4444", flexShrink: 0}} />verify_bom_cpl_pcb</span>
<span title="dead-board" style={{display: "inline-flex", alignItems: "center", gap: "0.3rem", padding: "0.15rem 0.5rem", borderRadius: "999px", fontSize: "0.74rem", fontFamily: "var(--ifm-font-family-monospace)", background: "#ef444422", border: "1px solid #ef444477"}}><span style={{width: "6px", height: "6px", borderRadius: "50%", background: "#ef4444", flexShrink: 0}} />verify_bom_values</span>
<span title="dead-board" style={{display: "inline-flex", alignItems: "center", gap: "0.3rem", padding: "0.15rem 0.5rem", borderRadius: "999px", fontSize: "0.74rem", fontFamily: "var(--ifm-font-family-monospace)", background: "#ef444422", border: "1px solid #ef444477"}}><span style={{width: "6px", height: "6px", borderRadius: "50%", background: "#ef4444", flexShrink: 0}} />verify_cpl_rotation_law</span>
<span title="dead-board" style={{display: "inline-flex", alignItems: "center", gap: "0.3rem", padding: "0.15rem 0.5rem", borderRadius: "999px", fontSize: "0.74rem", fontFamily: "var(--ifm-font-family-monospace)", background: "#ef444422", border: "1px solid #ef444477"}}><span style={{width: "6px", height: "6px", borderRadius: "50%", background: "#ef4444", flexShrink: 0}} />verify_datasheet</span>
<span title="dead-board" style={{display: "inline-flex", alignItems: "center", gap: "0.3rem", padding: "0.15rem 0.5rem", borderRadius: "999px", fontSize: "0.74rem", fontFamily: "var(--ifm-font-family-monospace)", background: "#ef444422", border: "1px solid #ef444477"}}><span style={{width: "6px", height: "6px", borderRadius: "50%", background: "#ef4444", flexShrink: 0}} />verify_datasheet_nets</span>
<span title="dead-board" style={{display: "inline-flex", alignItems: "center", gap: "0.3rem", padding: "0.15rem 0.5rem", borderRadius: "999px", fontSize: "0.74rem", fontFamily: "var(--ifm-font-family-monospace)", background: "#ef444422", border: "1px solid #ef444477"}}><span style={{width: "6px", height: "6px", borderRadius: "50%", background: "#ef4444", flexShrink: 0}} />verify_dfa</span>
<span title="dead-board" style={{display: "inline-flex", alignItems: "center", gap: "0.3rem", padding: "0.15rem 0.5rem", borderRadius: "999px", fontSize: "0.74rem", fontFamily: "var(--ifm-font-family-monospace)", background: "#ef444422", border: "1px solid #ef444477"}}><span style={{width: "6px", height: "6px", borderRadius: "50%", background: "#ef4444", flexShrink: 0}} />verify_easyeda_footprint</span>
<span title="dead-board" style={{display: "inline-flex", alignItems: "center", gap: "0.3rem", padding: "0.15rem 0.5rem", borderRadius: "999px", fontSize: "0.74rem", fontFamily: "var(--ifm-font-family-monospace)", background: "#ef444422", border: "1px solid #ef444477"}}><span style={{width: "6px", height: "6px", borderRadius: "50%", background: "#ef4444", flexShrink: 0}} />verify_polarity</span>
<span title="dead-board" style={{display: "inline-flex", alignItems: "center", gap: "0.3rem", padding: "0.15rem 0.5rem", borderRadius: "999px", fontSize: "0.74rem", fontFamily: "var(--ifm-font-family-monospace)", background: "#ef444422", border: "1px solid #ef444477"}}><span style={{width: "6px", height: "6px", borderRadius: "50%", background: "#ef4444", flexShrink: 0}} />verify_rpp_polarity</span>
<span title="degraded" style={{display: "inline-flex", alignItems: "center", gap: "0.3rem", padding: "0.15rem 0.5rem", borderRadius: "999px", fontSize: "0.74rem", fontFamily: "var(--ifm-font-family-monospace)", background: "#f59e0b22", border: "1px solid #f59e0b77"}}><span style={{width: "6px", height: "6px", borderRadius: "50%", background: "#f59e0b", flexShrink: 0}} />verify_stencil_aperture</span>
<span title="degraded" style={{display: "inline-flex", alignItems: "center", gap: "0.3rem", padding: "0.15rem 0.5rem", borderRadius: "999px", fontSize: "0.74rem", fontFamily: "var(--ifm-font-family-monospace)", background: "#f59e0b22", border: "1px solid #f59e0b77"}}><span style={{width: "6px", height: "6px", borderRadius: "50%", background: "#f59e0b", flexShrink: 0}} />verify_test_points</span>
</div>
</div>

<div style={{margin: "1.25rem 0"}}>
<div style={{display: "flex", alignItems: "baseline", gap: "0.6rem", flexWrap: "wrap", marginBottom: "0.35rem"}}>
<strong style={{fontSize: "1.02rem"}}>Electrical</strong>
<code style={{fontSize: "0.78rem"}}>22 gates</code>
<span style={{fontSize: "0.85rem", opacity: 0.75}}>Once powered, does the circuit do what it was specified to do?</span>
</div>
<div style={{display: "flex", flexWrap: "wrap", gap: "0.3rem"}}>
<span title="dead-board" style={{display: "inline-flex", alignItems: "center", gap: "0.3rem", padding: "0.15rem 0.5rem", borderRadius: "999px", fontSize: "0.74rem", fontFamily: "var(--ifm-font-family-monospace)", background: "#ef444422", border: "1px solid #ef444477"}}><span style={{width: "6px", height: "6px", borderRadius: "50%", background: "#ef4444", flexShrink: 0}} />erc_check</span>
<span title="degraded" style={{display: "inline-flex", alignItems: "center", gap: "0.3rem", padding: "0.15rem 0.5rem", borderRadius: "999px", fontSize: "0.74rem", fontFamily: "var(--ifm-font-family-monospace)", background: "#f59e0b22", border: "1px solid #f59e0b77"}}><span style={{width: "6px", height: "6px", borderRadius: "50%", background: "#f59e0b", flexShrink: 0}} />simulate_circuit</span>
<span title="dead-board" style={{display: "inline-flex", alignItems: "center", gap: "0.3rem", padding: "0.15rem 0.5rem", borderRadius: "999px", fontSize: "0.74rem", fontFamily: "var(--ifm-font-family-monospace)", background: "#ef444422", border: "1px solid #ef444477"}}><span style={{width: "6px", height: "6px", borderRadius: "50%", background: "#ef4444", flexShrink: 0}} />spice_power_check</span>
<span title="dead-board" style={{display: "inline-flex", alignItems: "center", gap: "0.3rem", padding: "0.15rem 0.5rem", borderRadius: "999px", fontSize: "0.74rem", fontFamily: "var(--ifm-font-family-monospace)", background: "#ef444422", border: "1px solid #ef444477"}}><span style={{width: "6px", height: "6px", borderRadius: "50%", background: "#ef4444", flexShrink: 0}} />test_erc_severity</span>
<span title="blind-spot" style={{display: "inline-flex", alignItems: "center", gap: "0.3rem", padding: "0.15rem 0.5rem", borderRadius: "999px", fontSize: "0.74rem", fontFamily: "var(--ifm-font-family-monospace)", background: "#a855f722", border: "1px solid #a855f777"}}><span style={{width: "6px", height: "6px", borderRadius: "50%", background: "#a855f7", flexShrink: 0}} />test_esd_protection</span>
<span title="blind-spot" style={{display: "inline-flex", alignItems: "center", gap: "0.3rem", padding: "0.15rem 0.5rem", borderRadius: "999px", fontSize: "0.74rem", fontFamily: "var(--ifm-font-family-monospace)", background: "#a855f722", border: "1px solid #a855f777"}}><span style={{width: "6px", height: "6px", borderRadius: "50%", background: "#a855f7", flexShrink: 0}} />test_power_via_ampacity</span>
<span title="dead-board" style={{display: "inline-flex", alignItems: "center", gap: "0.3rem", padding: "0.15rem 0.5rem", borderRadius: "999px", fontSize: "0.74rem", fontFamily: "var(--ifm-font-family-monospace)", background: "#ef444422", border: "1px solid #ef444477"}}><span style={{width: "6px", height: "6px", borderRadius: "50%", background: "#ef4444", flexShrink: 0}} />test_strapping_en_rc</span>
<span title="dead-board" style={{display: "inline-flex", alignItems: "center", gap: "0.3rem", padding: "0.15rem 0.5rem", borderRadius: "999px", fontSize: "0.74rem", fontFamily: "var(--ifm-font-family-monospace)", background: "#ef444422", border: "1px solid #ef444477"}}><span style={{width: "6px", height: "6px", borderRadius: "50%", background: "#ef4444", flexShrink: 0}} />verify_battery_protection</span>
<span title="degraded" style={{display: "inline-flex", alignItems: "center", gap: "0.3rem", padding: "0.15rem 0.5rem", borderRadius: "999px", fontSize: "0.74rem", fontFamily: "var(--ifm-font-family-monospace)", background: "#f59e0b22", border: "1px solid #f59e0b77"}}><span style={{width: "6px", height: "6px", borderRadius: "50%", background: "#f59e0b", flexShrink: 0}} />verify_decoupling_adequacy</span>
<span title="degraded" style={{display: "inline-flex", alignItems: "center", gap: "0.3rem", padding: "0.15rem 0.5rem", borderRadius: "999px", fontSize: "0.74rem", fontFamily: "var(--ifm-font-family-monospace)", background: "#f59e0b22", border: "1px solid #f59e0b77"}}><span style={{width: "6px", height: "6px", borderRadius: "50%", background: "#f59e0b", flexShrink: 0}} />verify_decoupling_paths</span>
<span title="dead-board" style={{display: "inline-flex", alignItems: "center", gap: "0.3rem", padding: "0.15rem 0.5rem", borderRadius: "999px", fontSize: "0.74rem", fontFamily: "var(--ifm-font-family-monospace)", background: "#ef444422", border: "1px solid #ef444477"}}><span style={{width: "6px", height: "6px", borderRadius: "50%", background: "#ef4444", flexShrink: 0}} />verify_design_intent</span>
<span title="dead-board" style={{display: "inline-flex", alignItems: "center", gap: "0.3rem", padding: "0.15rem 0.5rem", borderRadius: "999px", fontSize: "0.74rem", fontFamily: "var(--ifm-font-family-monospace)", background: "#ef444422", border: "1px solid #ef444477"}}><span style={{width: "6px", height: "6px", borderRadius: "50%", background: "#ef4444", flexShrink: 0}} />verify_erc</span>
<span title="degraded" style={{display: "inline-flex", alignItems: "center", gap: "0.3rem", padding: "0.15rem 0.5rem", borderRadius: "999px", fontSize: "0.74rem", fontFamily: "var(--ifm-font-family-monospace)", background: "#f59e0b22", border: "1px solid #f59e0b77"}}><span style={{width: "6px", height: "6px", borderRadius: "50%", background: "#f59e0b", flexShrink: 0}} />verify_esd_protection</span>
<span title="degraded" style={{display: "inline-flex", alignItems: "center", gap: "0.3rem", padding: "0.15rem 0.5rem", borderRadius: "999px", fontSize: "0.74rem", fontFamily: "var(--ifm-font-family-monospace)", background: "#f59e0b22", border: "1px solid #f59e0b77"}}><span style={{width: "6px", height: "6px", borderRadius: "50%", background: "#f59e0b", flexShrink: 0}} />verify_ground_loops</span>
<span title="dead-board" style={{display: "inline-flex", alignItems: "center", gap: "0.3rem", padding: "0.15rem 0.5rem", borderRadius: "999px", fontSize: "0.74rem", fontFamily: "var(--ifm-font-family-monospace)", background: "#ef444422", border: "1px solid #ef444477"}}><span style={{width: "6px", height: "6px", borderRadius: "50%", background: "#ef4444", flexShrink: 0}} />verify_power_paths</span>
<span title="dead-board" style={{display: "inline-flex", alignItems: "center", gap: "0.3rem", padding: "0.15rem 0.5rem", borderRadius: "999px", fontSize: "0.74rem", fontFamily: "var(--ifm-font-family-monospace)", background: "#ef444422", border: "1px solid #ef444477"}}><span style={{width: "6px", height: "6px", borderRadius: "50%", background: "#ef4444", flexShrink: 0}} />verify_power_resonance</span>
<span title="dead-board" style={{display: "inline-flex", alignItems: "center", gap: "0.3rem", padding: "0.15rem 0.5rem", borderRadius: "999px", fontSize: "0.74rem", fontFamily: "var(--ifm-font-family-monospace)", background: "#ef444422", border: "1px solid #ef444477"}}><span style={{width: "6px", height: "6px", borderRadius: "50%", background: "#ef4444", flexShrink: 0}} />verify_power_sequence</span>
<span title="degraded" style={{display: "inline-flex", alignItems: "center", gap: "0.3rem", padding: "0.15rem 0.5rem", borderRadius: "999px", fontSize: "0.74rem", fontFamily: "var(--ifm-font-family-monospace)", background: "#f59e0b22", border: "1px solid #f59e0b77"}}><span style={{width: "6px", height: "6px", borderRadius: "50%", background: "#f59e0b", flexShrink: 0}} />verify_power_via_ampacity</span>
<span title="dead-board" style={{display: "inline-flex", alignItems: "center", gap: "0.3rem", padding: "0.15rem 0.5rem", borderRadius: "999px", fontSize: "0.74rem", fontFamily: "var(--ifm-font-family-monospace)", background: "#ef444422", border: "1px solid #ef444477"}}><span style={{width: "6px", height: "6px", borderRadius: "50%", background: "#ef4444", flexShrink: 0}} />verify_sd_interface</span>
<span title="dead-board" style={{display: "inline-flex", alignItems: "center", gap: "0.3rem", padding: "0.15rem 0.5rem", borderRadius: "999px", fontSize: "0.74rem", fontFamily: "var(--ifm-font-family-monospace)", background: "#ef444422", border: "1px solid #ef444477"}}><span style={{width: "6px", height: "6px", borderRadius: "50%", background: "#ef4444", flexShrink: 0}} />verify_signal_chain_complete</span>
<span title="dead-board" style={{display: "inline-flex", alignItems: "center", gap: "0.3rem", padding: "0.15rem 0.5rem", borderRadius: "999px", fontSize: "0.74rem", fontFamily: "var(--ifm-font-family-monospace)", background: "#ef444422", border: "1px solid #ef444477"}}><span style={{width: "6px", height: "6px", borderRadius: "50%", background: "#ef4444", flexShrink: 0}} />verify_strapping_pins</span>
<span title="degraded" style={{display: "inline-flex", alignItems: "center", gap: "0.3rem", padding: "0.15rem 0.5rem", borderRadius: "999px", fontSize: "0.74rem", fontFamily: "var(--ifm-font-family-monospace)", background: "#f59e0b22", border: "1px solid #f59e0b77"}}><span style={{width: "6px", height: "6px", borderRadius: "50%", background: "#f59e0b", flexShrink: 0}} />verify_thermal_budget</span>
</div>
</div>

<div style={{margin: "1.25rem 0"}}>
<div style={{display: "flex", alignItems: "baseline", gap: "0.6rem", flexWrap: "wrap", marginBottom: "0.35rem"}}>
<strong style={{fontSize: "1.02rem"}}>Signal integrity / EMC</strong>
<code style={{fontSize: "0.78rem"}}>8 gates</code>
<span style={{fontSize: "0.85rem", opacity: 0.75}}>Does it still work at speed, and stay quiet while doing it?</span>
</div>
<div style={{display: "flex", flexWrap: "wrap", gap: "0.3rem"}}>
<span title="degraded" style={{display: "inline-flex", alignItems: "center", gap: "0.3rem", padding: "0.15rem 0.5rem", borderRadius: "999px", fontSize: "0.74rem", fontFamily: "var(--ifm-font-family-monospace)", background: "#f59e0b22", border: "1px solid #f59e0b77"}}><span style={{width: "6px", height: "6px", borderRadius: "50%", background: "#f59e0b", flexShrink: 0}} />verify_antenna_keepout</span>
<span title="degraded" style={{display: "inline-flex", alignItems: "center", gap: "0.3rem", padding: "0.15rem 0.5rem", borderRadius: "999px", fontSize: "0.74rem", fontFamily: "var(--ifm-font-family-monospace)", background: "#f59e0b22", border: "1px solid #f59e0b77"}}><span style={{width: "6px", height: "6px", borderRadius: "50%", background: "#f59e0b", flexShrink: 0}} />verify_crosstalk *</span>
<span title="degraded" style={{display: "inline-flex", alignItems: "center", gap: "0.3rem", padding: "0.15rem 0.5rem", borderRadius: "999px", fontSize: "0.74rem", fontFamily: "var(--ifm-font-family-monospace)", background: "#f59e0b22", border: "1px solid #f59e0b77"}}><span style={{width: "6px", height: "6px", borderRadius: "50%", background: "#f59e0b", flexShrink: 0}} />verify_length_match *</span>
<span title="degraded" style={{display: "inline-flex", alignItems: "center", gap: "0.3rem", padding: "0.15rem 0.5rem", borderRadius: "999px", fontSize: "0.74rem", fontFamily: "var(--ifm-font-family-monospace)", background: "#f59e0b22", border: "1px solid #f59e0b77"}}><span style={{width: "6px", height: "6px", borderRadius: "50%", background: "#f59e0b", flexShrink: 0}} />verify_reference_plane *</span>
<span title="degraded" style={{display: "inline-flex", alignItems: "center", gap: "0.3rem", padding: "0.15rem 0.5rem", borderRadius: "999px", fontSize: "0.74rem", fontFamily: "var(--ifm-font-family-monospace)", background: "#f59e0b22", border: "1px solid #f59e0b77"}}><span style={{width: "6px", height: "6px", borderRadius: "50%", background: "#f59e0b", flexShrink: 0}} />verify_usb_impedance</span>
<span title="degraded" style={{display: "inline-flex", alignItems: "center", gap: "0.3rem", padding: "0.15rem 0.5rem", borderRadius: "999px", fontSize: "0.74rem", fontFamily: "var(--ifm-font-family-monospace)", background: "#f59e0b22", border: "1px solid #f59e0b77"}}><span style={{width: "6px", height: "6px", borderRadius: "50%", background: "#f59e0b", flexShrink: 0}} />verify_usb_impedance_stackup</span>
<span title="degraded" style={{display: "inline-flex", alignItems: "center", gap: "0.3rem", padding: "0.15rem 0.5rem", borderRadius: "999px", fontSize: "0.74rem", fontFamily: "var(--ifm-font-family-monospace)", background: "#f59e0b22", border: "1px solid #f59e0b77"}}><span style={{width: "6px", height: "6px", borderRadius: "50%", background: "#f59e0b", flexShrink: 0}} />verify_usb_return_path</span>
<span title="degraded" style={{display: "inline-flex", alignItems: "center", gap: "0.3rem", padding: "0.15rem 0.5rem", borderRadius: "999px", fontSize: "0.74rem", fontFamily: "var(--ifm-font-family-monospace)", background: "#f59e0b22", border: "1px solid #f59e0b77"}}><span style={{width: "6px", height: "6px", borderRadius: "50%", background: "#f59e0b", flexShrink: 0}} />verify_via_discontinuity *</span>
</div>
</div>

<div style={{margin: "1.25rem 0"}}>
<div style={{display: "flex", alignItems: "baseline", gap: "0.6rem", flexWrap: "wrap", marginBottom: "0.35rem"}}>
<strong style={{fontSize: "1.02rem"}}>Release integrity</strong>
<code style={{fontSize: "0.78rem"}}>11 gates</code>
<span style={{fontSize: "0.85rem", opacity: 0.75}}>Is the thing being ordered the thing that was verified?</span>
</div>
<div style={{display: "flex", flexWrap: "wrap", gap: "0.3rem"}}>
<span title="blind-spot" style={{display: "inline-flex", alignItems: "center", gap: "0.3rem", padding: "0.15rem 0.5rem", borderRadius: "999px", fontSize: "0.74rem", fontFamily: "var(--ifm-font-family-monospace)", background: "#a855f722", border: "1px solid #a855f777"}}><span style={{width: "6px", height: "6px", borderRadius: "50%", background: "#a855f7", flexShrink: 0}} />test_claims_ledger</span>
<span title="dead-board" style={{display: "inline-flex", alignItems: "center", gap: "0.3rem", padding: "0.15rem 0.5rem", borderRadius: "999px", fontSize: "0.74rem", fontFamily: "var(--ifm-font-family-monospace)", background: "#ef444422", border: "1px solid #ef444477"}}><span style={{width: "6px", height: "6px", borderRadius: "50%", background: "#ef4444", flexShrink: 0}} />test_gerber_etest</span>
<span title="blind-spot" style={{display: "inline-flex", alignItems: "center", gap: "0.3rem", padding: "0.15rem 0.5rem", borderRadius: "999px", fontSize: "0.74rem", fontFamily: "var(--ifm-font-family-monospace)", background: "#a855f722", border: "1px solid #a855f777"}}><span style={{width: "6px", height: "6px", borderRadius: "50%", background: "#a855f7", flexShrink: 0}} />test_order_manifest</span>
<span title="blind-spot" style={{display: "inline-flex", alignItems: "center", gap: "0.3rem", padding: "0.15rem 0.5rem", borderRadius: "999px", fontSize: "0.74rem", fontFamily: "var(--ifm-font-family-monospace)", background: "#a855f722", border: "1px solid #a855f777"}}><span style={{width: "6px", height: "6px", borderRadius: "50%", background: "#a855f7", flexShrink: 0}} />test_verify_memory</span>
<span title="blind-spot" style={{display: "inline-flex", alignItems: "center", gap: "0.3rem", padding: "0.15rem 0.5rem", borderRadius: "999px", fontSize: "0.74rem", fontFamily: "var(--ifm-font-family-monospace)", background: "#a855f722", border: "1px solid #a855f777"}}><span style={{width: "6px", height: "6px", borderRadius: "50%", background: "#a855f7", flexShrink: 0}} />verify_bringup_fresh</span>
<span title="blind-spot" style={{display: "inline-flex", alignItems: "center", gap: "0.3rem", padding: "0.15rem 0.5rem", borderRadius: "999px", fontSize: "0.74rem", fontFamily: "var(--ifm-font-family-monospace)", background: "#a855f722", border: "1px solid #a855f777"}}><span style={{width: "6px", height: "6px", borderRadius: "50%", background: "#a855f7", flexShrink: 0}} />verify_claims_ledger</span>
<span title="blind-spot" style={{display: "inline-flex", alignItems: "center", gap: "0.3rem", padding: "0.15rem 0.5rem", borderRadius: "999px", fontSize: "0.74rem", fontFamily: "var(--ifm-font-family-monospace)", background: "#a855f722", border: "1px solid #a855f777"}}><span style={{width: "6px", height: "6px", borderRadius: "50%", background: "#a855f7", flexShrink: 0}} />verify_context_budget</span>
<span title="dead-board" style={{display: "inline-flex", alignItems: "center", gap: "0.3rem", padding: "0.15rem 0.5rem", borderRadius: "999px", fontSize: "0.74rem", fontFamily: "var(--ifm-font-family-monospace)", background: "#ef444422", border: "1px solid #ef444477"}}><span style={{width: "6px", height: "6px", borderRadius: "50%", background: "#ef4444", flexShrink: 0}} />verify_gerber_etest</span>
<span title="blind-spot" style={{display: "inline-flex", alignItems: "center", gap: "0.3rem", padding: "0.15rem 0.5rem", borderRadius: "999px", fontSize: "0.74rem", fontFamily: "var(--ifm-font-family-monospace)", background: "#a855f722", border: "1px solid #a855f777"}}><span style={{width: "6px", height: "6px", borderRadius: "50%", background: "#a855f7", flexShrink: 0}} />verify_memory</span>
<span title="cosmetic" style={{display: "inline-flex", alignItems: "center", gap: "0.3rem", padding: "0.15rem 0.5rem", borderRadius: "999px", fontSize: "0.74rem", fontFamily: "var(--ifm-font-family-monospace)", background: "#94a3b822", border: "1px solid #94a3b877"}}><span style={{width: "6px", height: "6px", borderRadius: "50%", background: "#94a3b8", flexShrink: 0}} />verify_net_explorer_fresh</span>
<span title="dead-board" style={{display: "inline-flex", alignItems: "center", gap: "0.3rem", padding: "0.15rem 0.5rem", borderRadius: "999px", fontSize: "0.74rem", fontFamily: "var(--ifm-font-family-monospace)", background: "#ef444422", border: "1px solid #ef444477"}}><span style={{width: "6px", height: "6px", borderRadius: "50%", background: "#ef4444", flexShrink: 0}} />verify_order_manifest</span>
</div>
</div>

<div style={{margin: "1.25rem 0"}}>
<div style={{display: "flex", alignItems: "baseline", gap: "0.6rem", flexWrap: "wrap", marginBottom: "0.35rem"}}>
<strong style={{fontSize: "1.02rem"}}>Meta / blind-spot</strong>
<code style={{fontSize: "0.78rem"}}>6 gates</code>
<span style={{fontSize: "0.85rem", opacity: 0.75}}>Can the gate network still be trusted to notice?</span>
</div>
<div style={{display: "flex", flexWrap: "wrap", gap: "0.3rem"}}>
<span title="blind-spot" style={{display: "inline-flex", alignItems: "center", gap: "0.3rem", padding: "0.15rem 0.5rem", borderRadius: "999px", fontSize: "0.74rem", fontFamily: "var(--ifm-font-family-monospace)", background: "#a855f722", border: "1px solid #a855f777"}}><span style={{width: "6px", height: "6px", borderRadius: "50%", background: "#a855f7", flexShrink: 0}} />test_gate_coverage</span>
<span title="blind-spot" style={{display: "inline-flex", alignItems: "center", gap: "0.3rem", padding: "0.15rem 0.5rem", borderRadius: "999px", fontSize: "0.74rem", fontFamily: "var(--ifm-font-family-monospace)", background: "#a855f722", border: "1px solid #a855f777"}}><span style={{width: "6px", height: "6px", borderRadius: "50%", background: "#a855f7", flexShrink: 0}} />test_issue_dispatch</span>
<span title="blind-spot" style={{display: "inline-flex", alignItems: "center", gap: "0.3rem", padding: "0.15rem 0.5rem", borderRadius: "999px", fontSize: "0.74rem", fontFamily: "var(--ifm-font-family-monospace)", background: "#a855f722", border: "1px solid #a855f777"}}><span style={{width: "6px", height: "6px", borderRadius: "50%", background: "#a855f7", flexShrink: 0}} />test_vbench</span>
<span title="blind-spot" style={{display: "inline-flex", alignItems: "center", gap: "0.3rem", padding: "0.15rem 0.5rem", borderRadius: "999px", fontSize: "0.74rem", fontFamily: "var(--ifm-font-family-monospace)", background: "#a855f722", border: "1px solid #a855f777"}}><span style={{width: "6px", height: "6px", borderRadius: "50%", background: "#a855f7", flexShrink: 0}} />test_vbench_display</span>
<span title="blind-spot" style={{display: "inline-flex", alignItems: "center", gap: "0.3rem", padding: "0.15rem 0.5rem", borderRadius: "999px", fontSize: "0.74rem", fontFamily: "var(--ifm-font-family-monospace)", background: "#a855f722", border: "1px solid #a855f777"}}><span style={{width: "6px", height: "6px", borderRadius: "50%", background: "#a855f7", flexShrink: 0}} />test_vbench_dynamics</span>
<span title="blind-spot" style={{display: "inline-flex", alignItems: "center", gap: "0.3rem", padding: "0.15rem 0.5rem", borderRadius: "999px", fontSize: "0.74rem", fontFamily: "var(--ifm-font-family-monospace)", background: "#a855f722", border: "1px solid #a855f777"}}><span style={{width: "6px", height: "6px", borderRadius: "50%", background: "#a855f7", flexShrink: 0}} />test_vbench_sdcard</span>
</div>
</div>

<p style={{fontSize: "0.8rem", opacity: 0.7}}>
<code>*</code> = new EMC gate. Hover a chip for its severity.
</p>

---

## B. EMC coverage grid

The 16 classic EMC layout mistakes, and which gate catches each one.

<div style={{display: "grid", gridTemplateColumns: "repeat(auto-fit, minmax(210px, 1fr))", gap: "0.6rem", margin: "1.25rem 0"}}>
<div style={{border: "1px solid var(--ifm-color-emphasis-300)", borderTop: "3px solid #f59e0b", borderRadius: "8px", padding: "0.6rem 0.7rem", background: "var(--ifm-background-surface-color)"}}><div style={{display: "flex", justifyContent: "space-between", alignItems: "center", gap: "0.4rem", marginBottom: "0.35rem"}}><span style={{fontSize: "0.72rem", opacity: 0.55, fontVariantNumeric: "tabular-nums"}}>01</span><span style={{padding: "0.1rem 0.45rem", borderRadius: "999px", fontSize: "0.64rem", fontWeight: 700, letterSpacing: "0.04em", background: "#f59e0b26", border: "1px solid #f59e0b88"}}>PARTIAL</span></div><div style={{fontWeight: 600, fontSize: "0.92rem", lineHeight: 1.25, marginBottom: "0.3rem"}}>Broken Return Path</div><div style={{fontSize: "0.7rem", fontFamily: "var(--ifm-font-family-monospace)", opacity: 0.8, lineHeight: 1.35, marginBottom: "0.25rem"}}>verify_usb_return_path</div><div style={{fontSize: "0.72rem", opacity: 0.6, lineHeight: 1.3}}>advisory outside USB</div></div>
<div style={{border: "1px solid var(--ifm-color-emphasis-300)", borderTop: "3px solid #f59e0b", borderRadius: "8px", padding: "0.6rem 0.7rem", background: "var(--ifm-background-surface-color)"}}><div style={{display: "flex", justifyContent: "space-between", alignItems: "center", gap: "0.4rem", marginBottom: "0.35rem"}}><span style={{fontSize: "0.72rem", opacity: 0.55, fontVariantNumeric: "tabular-nums"}}>02</span><span style={{padding: "0.1rem 0.45rem", borderRadius: "999px", fontSize: "0.64rem", fontWeight: 700, letterSpacing: "0.04em", background: "#f59e0b26", border: "1px solid #f59e0b88"}}>PARTIAL</span></div><div style={{fontWeight: 600, fontSize: "0.92rem", lineHeight: 1.25, marginBottom: "0.3rem"}}>Long Loop Area</div><div style={{fontSize: "0.7rem", fontFamily: "var(--ifm-font-family-monospace)", opacity: 0.8, lineHeight: 1.35, marginBottom: "0.25rem"}}>verify_dfm_v2 · verify_decoupling_paths</div><div style={{fontSize: "0.72rem", opacity: 0.6, lineHeight: 1.3}}>buck hot-loop + cap ratio</div></div>
<div style={{border: "1px solid var(--ifm-color-emphasis-300)", borderTop: "3px solid #22c55e", borderRadius: "8px", padding: "0.6rem 0.7rem", background: "var(--ifm-background-surface-color)"}}><div style={{display: "flex", justifyContent: "space-between", alignItems: "center", gap: "0.4rem", marginBottom: "0.35rem"}}><span style={{fontSize: "0.72rem", opacity: 0.55, fontVariantNumeric: "tabular-nums"}}>03</span><span style={{padding: "0.1rem 0.45rem", borderRadius: "999px", fontSize: "0.64rem", fontWeight: 700, letterSpacing: "0.04em", background: "#22c55e26", border: "1px solid #22c55e88"}}>COVERED</span></div><div style={{fontWeight: 600, fontSize: "0.92rem", lineHeight: 1.25, marginBottom: "0.3rem"}}>Split Reference Plane</div><div style={{fontSize: "0.7rem", fontFamily: "var(--ifm-font-family-monospace)", opacity: 0.8, lineHeight: 1.35, marginBottom: "0.25rem"}}>verify_stackup · verify_power_net_integrity</div><div style={{fontSize: "0.72rem", opacity: 0.6, lineHeight: 1.3}}>one piece of copper per plane</div></div>
<div style={{border: "1px solid var(--ifm-color-emphasis-300)", borderTop: "3px solid #22c55e", borderRadius: "8px", padding: "0.6rem 0.7rem", background: "var(--ifm-background-surface-color)"}}><div style={{display: "flex", justifyContent: "space-between", alignItems: "center", gap: "0.4rem", marginBottom: "0.35rem"}}><span style={{fontSize: "0.72rem", opacity: 0.55, fontVariantNumeric: "tabular-nums"}}>04</span><span style={{padding: "0.1rem 0.45rem", borderRadius: "999px", fontSize: "0.64rem", fontWeight: 700, letterSpacing: "0.04em", background: "#22c55e26", border: "1px solid #22c55e88"}}>COVERED</span></div><div style={{fontWeight: 600, fontSize: "0.92rem", lineHeight: 1.25, marginBottom: "0.3rem"}}>Decoupling Placement</div><div style={{fontSize: "0.7rem", fontFamily: "var(--ifm-font-family-monospace)", opacity: 0.8, lineHeight: 1.35, marginBottom: "0.25rem"}}>verify_decoupling_paths · verify_decoupling_adequacy</div><div style={{fontSize: "0.72rem", opacity: 0.6, lineHeight: 1.3}}>path length and capacitance</div></div>
<div style={{border: "1px solid var(--ifm-color-emphasis-300)", borderTop: "3px solid #3b82f6", borderRadius: "8px", padding: "0.6rem 0.7rem", background: "var(--ifm-background-surface-color)"}}><div style={{display: "flex", justifyContent: "space-between", alignItems: "center", gap: "0.4rem", marginBottom: "0.35rem"}}><span style={{fontSize: "0.72rem", opacity: 0.55, fontVariantNumeric: "tabular-nums"}}>05</span><span style={{padding: "0.1rem 0.45rem", borderRadius: "999px", fontSize: "0.64rem", fontWeight: 700, letterSpacing: "0.04em", background: "#3b82f626", border: "1px solid #3b82f688"}}>NEW GATE</span></div><div style={{fontWeight: 600, fontSize: "0.92rem", lineHeight: 1.25, marginBottom: "0.3rem"}}>Signal Crossing Gaps</div><div style={{fontSize: "0.7rem", fontFamily: "var(--ifm-font-family-monospace)", opacity: 0.8, lineHeight: 1.35, marginBottom: "0.25rem"}}>verify_reference_plane</div><div style={{fontSize: "0.72rem", opacity: 0.6, lineHeight: 1.3}}>traces over plane voids</div></div>
<div style={{border: "1px solid var(--ifm-color-emphasis-300)", borderTop: "3px solid #f59e0b", borderRadius: "8px", padding: "0.6rem 0.7rem", background: "var(--ifm-background-surface-color)"}}><div style={{display: "flex", justifyContent: "space-between", alignItems: "center", gap: "0.4rem", marginBottom: "0.35rem"}}><span style={{fontSize: "0.72rem", opacity: 0.55, fontVariantNumeric: "tabular-nums"}}>06</span><span style={{padding: "0.1rem 0.45rem", borderRadius: "999px", fontSize: "0.64rem", fontWeight: 700, letterSpacing: "0.04em", background: "#f59e0b26", border: "1px solid #f59e0b88"}}>PARTIAL</span></div><div style={{fontWeight: 600, fontSize: "0.92rem", lineHeight: 1.25, marginBottom: "0.3rem"}}>Poor Ground Return</div><div style={{fontSize: "0.7rem", fontFamily: "var(--ifm-font-family-monospace)", opacity: 0.8, lineHeight: 1.35, marginBottom: "0.25rem"}}>verify_ground_loops · verify_zone_connectivity</div><div style={{fontSize: "0.72rem", opacity: 0.6, lineHeight: 1.3}}>loops found, area not scored</div></div>
<div style={{border: "1px solid var(--ifm-color-emphasis-300)", borderTop: "3px solid #22c55e", borderRadius: "8px", padding: "0.6rem 0.7rem", background: "var(--ifm-background-surface-color)"}}><div style={{display: "flex", justifyContent: "space-between", alignItems: "center", gap: "0.4rem", marginBottom: "0.35rem"}}><span style={{fontSize: "0.72rem", opacity: 0.55, fontVariantNumeric: "tabular-nums"}}>07</span><span style={{padding: "0.1rem 0.45rem", borderRadius: "999px", fontSize: "0.64rem", fontWeight: 700, letterSpacing: "0.04em", background: "#22c55e26", border: "1px solid #22c55e88"}}>COVERED</span></div><div style={{fontWeight: 600, fontSize: "0.92rem", lineHeight: 1.25, marginBottom: "0.3rem"}}>Trace Spacing</div><div style={{fontSize: "0.7rem", fontFamily: "var(--ifm-font-family-monospace)", opacity: 0.8, lineHeight: 1.35, marginBottom: "0.25rem"}}>verify_copper_clearance</div><div style={{fontSize: "0.72rem", opacity: 0.6, lineHeight: 1.3}}>polygon-accurate gaps</div></div>
<div style={{border: "1px solid var(--ifm-color-emphasis-300)", borderTop: "3px solid #f59e0b", borderRadius: "8px", padding: "0.6rem 0.7rem", background: "var(--ifm-background-surface-color)"}}><div style={{display: "flex", justifyContent: "space-between", alignItems: "center", gap: "0.4rem", marginBottom: "0.35rem"}}><span style={{fontSize: "0.72rem", opacity: 0.55, fontVariantNumeric: "tabular-nums"}}>08</span><span style={{padding: "0.1rem 0.45rem", borderRadius: "999px", fontSize: "0.64rem", fontWeight: 700, letterSpacing: "0.04em", background: "#f59e0b26", border: "1px solid #f59e0b88"}}>PARTIAL</span></div><div style={{fontWeight: 600, fontSize: "0.92rem", lineHeight: 1.25, marginBottom: "0.3rem"}}>RF Shielding</div><div style={{fontSize: "0.7rem", fontFamily: "var(--ifm-font-family-monospace)", opacity: 0.8, lineHeight: 1.35, marginBottom: "0.25rem"}}>verify_antenna_keepout</div><div style={{fontSize: "0.72rem", opacity: 0.6, lineHeight: 1.3}}>no shield can on board by design</div></div>
<div style={{border: "1px solid var(--ifm-color-emphasis-300)", borderTop: "3px solid #f59e0b", borderRadius: "8px", padding: "0.6rem 0.7rem", background: "var(--ifm-background-surface-color)"}}><div style={{display: "flex", justifyContent: "space-between", alignItems: "center", gap: "0.4rem", marginBottom: "0.35rem"}}><span style={{fontSize: "0.72rem", opacity: 0.55, fontVariantNumeric: "tabular-nums"}}>09</span><span style={{padding: "0.1rem 0.45rem", borderRadius: "999px", fontSize: "0.64rem", fontWeight: 700, letterSpacing: "0.04em", background: "#f59e0b26", border: "1px solid #f59e0b88"}}>PARTIAL</span></div><div style={{fontWeight: 600, fontSize: "0.92rem", lineHeight: 1.25, marginBottom: "0.3rem"}}>Return Via Placement</div><div style={{fontSize: "0.7rem", fontFamily: "var(--ifm-font-family-monospace)", opacity: 0.8, lineHeight: 1.35, marginBottom: "0.25rem"}}>verify_usb_return_path</div><div style={{fontSize: "0.72rem", opacity: 0.6, lineHeight: 1.3}}>USB pair only</div></div>
<div style={{border: "1px solid var(--ifm-color-emphasis-300)", borderTop: "3px solid #f59e0b", borderRadius: "8px", padding: "0.6rem 0.7rem", background: "var(--ifm-background-surface-color)"}}><div style={{display: "flex", justifyContent: "space-between", alignItems: "center", gap: "0.4rem", marginBottom: "0.35rem"}}><span style={{fontSize: "0.72rem", opacity: 0.55, fontVariantNumeric: "tabular-nums"}}>10</span><span style={{padding: "0.1rem 0.45rem", borderRadius: "999px", fontSize: "0.64rem", fontWeight: 700, letterSpacing: "0.04em", background: "#f59e0b26", border: "1px solid #f59e0b88"}}>PARTIAL</span></div><div style={{fontWeight: 600, fontSize: "0.92rem", lineHeight: 1.25, marginBottom: "0.3rem"}}>High-Speed Routing</div><div style={{fontSize: "0.7rem", fontFamily: "var(--ifm-font-family-monospace)", opacity: 0.8, lineHeight: 1.35, marginBottom: "0.25rem"}}>verify_usb_impedance</div><div style={{fontSize: "0.72rem", opacity: 0.6, lineHeight: 1.3}}>limits derived from bit rate</div></div>
<div style={{border: "1px solid var(--ifm-color-emphasis-300)", borderTop: "3px solid #3b82f6", borderRadius: "8px", padding: "0.6rem 0.7rem", background: "var(--ifm-background-surface-color)"}}><div style={{display: "flex", justifyContent: "space-between", alignItems: "center", gap: "0.4rem", marginBottom: "0.35rem"}}><span style={{fontSize: "0.72rem", opacity: 0.55, fontVariantNumeric: "tabular-nums"}}>11</span><span style={{padding: "0.1rem 0.45rem", borderRadius: "999px", fontSize: "0.64rem", fontWeight: 700, letterSpacing: "0.04em", background: "#3b82f626", border: "1px solid #3b82f688"}}>NEW GATE</span></div><div style={{fontWeight: 600, fontSize: "0.92rem", lineHeight: 1.25, marginBottom: "0.3rem"}}>Crosstalk 3W</div><div style={{fontSize: "0.7rem", fontFamily: "var(--ifm-font-family-monospace)", opacity: 0.8, lineHeight: 1.35, marginBottom: "0.25rem"}}>verify_crosstalk</div><div style={{fontSize: "0.72rem", opacity: 0.6, lineHeight: 1.3}}>parallel-run coupling</div></div>
<div style={{border: "1px solid var(--ifm-color-emphasis-300)", borderTop: "3px solid #22c55e", borderRadius: "8px", padding: "0.6rem 0.7rem", background: "var(--ifm-background-surface-color)"}}><div style={{display: "flex", justifyContent: "space-between", alignItems: "center", gap: "0.4rem", marginBottom: "0.35rem"}}><span style={{fontSize: "0.72rem", opacity: 0.55, fontVariantNumeric: "tabular-nums"}}>12</span><span style={{padding: "0.1rem 0.45rem", borderRadius: "999px", fontSize: "0.64rem", fontWeight: 700, letterSpacing: "0.04em", background: "#22c55e26", border: "1px solid #22c55e88"}}>COVERED</span></div><div style={{fontWeight: 600, fontSize: "0.92rem", lineHeight: 1.25, marginBottom: "0.3rem"}}>Uncontrolled Impedance</div><div style={{fontSize: "0.7rem", fontFamily: "var(--ifm-font-family-monospace)", opacity: 0.8, lineHeight: 1.35, marginBottom: "0.25rem"}}>verify_usb_impedance_stackup</div><div style={{fontSize: "0.72rem", opacity: 0.6, lineHeight: 1.3}}>JLC04161H-7628 stackup</div></div>
<div style={{border: "1px solid var(--ifm-color-emphasis-300)", borderTop: "3px solid #3b82f6", borderRadius: "8px", padding: "0.6rem 0.7rem", background: "var(--ifm-background-surface-color)"}}><div style={{display: "flex", justifyContent: "space-between", alignItems: "center", gap: "0.4rem", marginBottom: "0.35rem"}}><span style={{fontSize: "0.72rem", opacity: 0.55, fontVariantNumeric: "tabular-nums"}}>13</span><span style={{padding: "0.1rem 0.45rem", borderRadius: "999px", fontSize: "0.64rem", fontWeight: 700, letterSpacing: "0.04em", background: "#3b82f626", border: "1px solid #3b82f688"}}>NEW GATE</span></div><div style={{fontWeight: 600, fontSize: "0.92rem", lineHeight: 1.25, marginBottom: "0.3rem"}}>Trace Length Mismatch</div><div style={{fontSize: "0.7rem", fontFamily: "var(--ifm-font-family-monospace)", opacity: 0.8, lineHeight: 1.35, marginBottom: "0.25rem"}}>verify_length_match</div><div style={{fontSize: "0.72rem", opacity: 0.6, lineHeight: 1.3}}>skew against edge rate</div></div>
<div style={{border: "1px solid var(--ifm-color-emphasis-300)", borderTop: "3px solid #3b82f6", borderRadius: "8px", padding: "0.6rem 0.7rem", background: "var(--ifm-background-surface-color)"}}><div style={{display: "flex", justifyContent: "space-between", alignItems: "center", gap: "0.4rem", marginBottom: "0.35rem"}}><span style={{fontSize: "0.72rem", opacity: 0.55, fontVariantNumeric: "tabular-nums"}}>14</span><span style={{padding: "0.1rem 0.45rem", borderRadius: "999px", fontSize: "0.64rem", fontWeight: 700, letterSpacing: "0.04em", background: "#3b82f626", border: "1px solid #3b82f688"}}>NEW GATE</span></div><div style={{fontWeight: 600, fontSize: "0.92rem", lineHeight: 1.25, marginBottom: "0.3rem"}}>Via Discontinuity</div><div style={{fontSize: "0.7rem", fontFamily: "var(--ifm-font-family-monospace)", opacity: 0.8, lineHeight: 1.35, marginBottom: "0.25rem"}}>verify_via_discontinuity</div><div style={{fontSize: "0.72rem", opacity: 0.6, lineHeight: 1.3}}>stub and count heuristics</div></div>
<div style={{border: "1px solid var(--ifm-color-emphasis-300)", borderTop: "3px solid #f59e0b", borderRadius: "8px", padding: "0.6rem 0.7rem", background: "var(--ifm-background-surface-color)"}}><div style={{display: "flex", justifyContent: "space-between", alignItems: "center", gap: "0.4rem", marginBottom: "0.35rem"}}><span style={{fontSize: "0.72rem", opacity: 0.55, fontVariantNumeric: "tabular-nums"}}>15</span><span style={{padding: "0.1rem 0.45rem", borderRadius: "999px", fontSize: "0.64rem", fontWeight: 700, letterSpacing: "0.04em", background: "#f59e0b26", border: "1px solid #f59e0b88"}}>PARTIAL</span></div><div style={{fontWeight: 600, fontSize: "0.92rem", lineHeight: 1.25, marginBottom: "0.3rem"}}>Termination</div><div style={{fontSize: "0.7rem", fontFamily: "var(--ifm-font-family-monospace)", opacity: 0.8, lineHeight: 1.35, marginBottom: "0.25rem"}}>verify_usb_impedance</div><div style={{fontSize: "0.72rem", opacity: 0.6, lineHeight: 1.3}}>USB series R proven in-path</div></div>
<div style={{border: "1px solid var(--ifm-color-emphasis-300)", borderTop: "3px solid #f59e0b", borderRadius: "8px", padding: "0.6rem 0.7rem", background: "var(--ifm-background-surface-color)"}}><div style={{display: "flex", justifyContent: "space-between", alignItems: "center", gap: "0.4rem", marginBottom: "0.35rem"}}><span style={{fontSize: "0.72rem", opacity: 0.55, fontVariantNumeric: "tabular-nums"}}>16</span><span style={{padding: "0.1rem 0.45rem", borderRadius: "999px", fontSize: "0.64rem", fontWeight: 700, letterSpacing: "0.04em", background: "#f59e0b26", border: "1px solid #f59e0b88"}}>PARTIAL</span></div><div style={{fontWeight: 600, fontSize: "0.92rem", lineHeight: 1.25, marginBottom: "0.3rem"}}>Shield Stitching</div><div style={{fontSize: "0.7rem", fontFamily: "var(--ifm-font-family-monospace)", opacity: 0.8, lineHeight: 1.35, marginBottom: "0.25rem"}}>verify_zone_connectivity</div><div style={{fontSize: "0.72rem", opacity: 0.6, lineHeight: 1.3}}>no lambda/20 spacing rule</div></div>
</div>

<p style={{fontSize: "0.8rem", opacity: 0.7}}>
<strong>4 covered · 4 new gates · 8 partial.</strong> "Partial" means a gate fires on
the failure mode but over a narrower scope than the general rule — usually the USB
pair rather than every net.
</p>

---

## C. Version improvements

Quality improvements per release, v2.9 to v4.5.1 and what comes next

---

## Where to go next

- [Pre-Production Verification](/docs/manufacturing/verification) — what each gate
  actually asserts, and the JLCPCB threshold tables behind them
- [PCBA Manufacturing & Ordering](/docs/manufacturing) — the order package itself
- `make open-issues` — which of these 99 gates is red right now
- `make dispatch` — turn every red gate into an owned work order
