pjcau/esp32-emu-turbo/software/benchmark/partitions_bench.csv

# Name | Type | SubType | Offset | Size
nvs | data | nvs | 0x9000 | 0x8000
phy_init | data | phy | 0x11000 | 0x1000
factory | app | factory | 0x20000 | 0x400000
roms | data | spiffs | 0x420000 | 0x200000
