pjcau/esp32-emu-turbo/scripts/mamebench/results/photos/2026-10-04-board-1.jpg

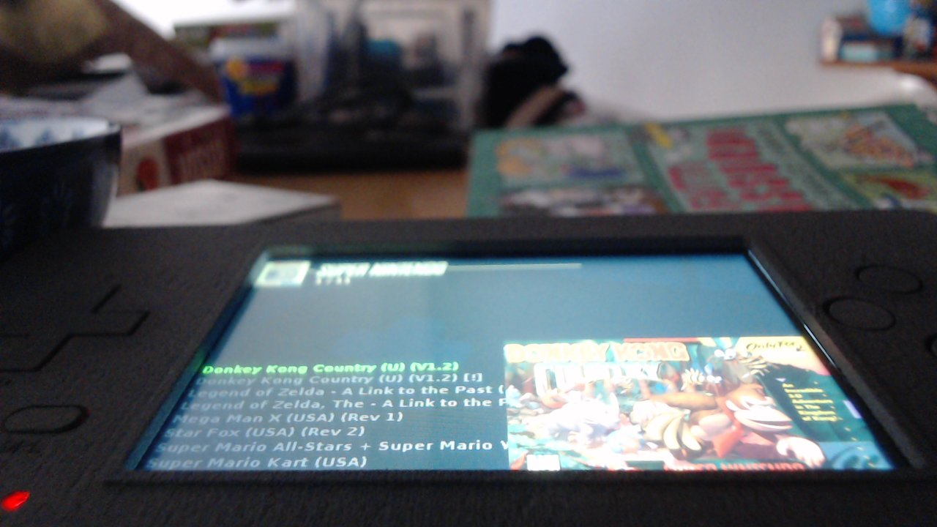
scripts/mamebench/results/photos/2026-10-04-board-1.jpg
