pjcau/esp32-emu-turbo/software/main/audio.h

/*
 * ESP32 Emu Turbo — Audio Driver
 * I2S PDM TX mode → PAM8403 Class-D amplifier → 28mm speaker
 */

#pragma once

#include "esp_err.h"

/**
 * Initialize I2S in PDM TX mode (sigma-delta output).
 * 32 kHz, 16-bit, mono output on GPIO17.
 * The existing RC filter (0.47uF + 20k bias) converts PDM to analog.
 */
esp_err_t audio_init(void);

/**
 * Play a 440 Hz sine wave test tone for the specified duration (ms).
 * Blocks until playback is complete.
 */
esp_err_t audio_play_test_tone(int duration_ms);

/**
 * Play one sine note (freq_hz, 0 = rest) for duration_ms with a 5 ms
 * fade in/out. Blocks until written.
 */
esp_err_t audio_play_note(int freq_hz, int duration_ms);

/**
 * Play a short recognizable melody (SMB overworld intro, ~1.6 s). Blocks.
 */
esp_err_t audio_play_melody(void);

/**
 * Stop audio playback and disable the I2S channel.
 */
void audio_stop(void);
