pjcau/esp32-emu-turbo/scripts/generate_pcb/board.py

"""Generate the complete KiCad PCB board.

Layout philosophy:
  TOP (F.Cu)  — user-facing: face buttons (D-pad, ABXY, Start, Select, Menu)
                + charging LEDs (bottom-left)
  BOTTOM (B.Cu) — all electronics: ESP32, ICs, connectors,
                  speaker, power switch, passives, battery connector
                  + L/R shoulder buttons (rotated 90°, aligned to top edge)

Display (ILI9488 3.95" bare panel) sits on top of PCB.  FPC ribbon passes
through a vertical slot in the board to reach J4 (FPC-40P) on the back.
"""

import math
import re as _re

from . import primitives as P
from . import footprints as FP
from . import routing

# Net ID -> name lookup for pad net injection
_NET_NAME = {nid: name for nid, name in P.NET_LIST}


def _inject_pad_net(pad_str, ref):
    """Replace (net 0 "") in a pad S-expression with the correct net.

    Extracts pad number, looks up (ref, pad_num) in routing.get_pad_nets(),
    and substitutes the correct net ID and name.
    """
    num_m = _re.search(r'\(pad\s+"([^"]*)"', pad_str)
    if not num_m:
        return pad_str
    pad_num = num_m.group(1)
    net_id = routing.get_pad_nets().get((ref, pad_num), 0)
    if net_id == 0:
        return pad_str
    net_name = _NET_NAME.get(net_id, "")
    return _re.sub(
        r'\(net\s+0\s+""\)',
        f'(net {net_id} "{net_name}")',
        pad_str,
    )

# ── Board dimensions (from enclosure.scad) ──────────────────────
BOARD_W = 160.0   # mm (170mm body - 2x5mm clearance)
BOARD_H = 75.0    # mm (85mm body - 2x5mm clearance)
CORNER_R = 6.0    # Corner radius (slightly less than 8mm body)

# PCB origin = top-left corner (KiCad convention: Y+ = down)
# Enclosure uses center origin, so we convert:
#   pcb_x = enclosure_x + BOARD_W/2
#   pcb_y = BOARD_H/2 - enclosure_y  (Y inverted)
CX = BOARD_W / 2   # 80.0
CY = BOARD_H / 2   # 37.5


def enc_to_pcb(ex, ey):
    """Convert enclosure center-origin coords to PCB top-left origin."""
    return (CX + ex, CY - ey)


# ── Mounting hole positions (from enclosure.scad screw_positions) ──
# NOTE: Enclosure only uses 4 corner bosses (center 2 removed for battery).
# PCB keeps all 6 holes for mechanical flexibility and GND zone stitching.
MOUNT_HOLES_ENC = [
    (-70, 30.5), (70, 30.5),
    (-70, -30.5), (70, -30.5),
    (-25, 0), (25, 0),
]

# ── Display area (ILI9488 3.95" bare LCD panel via FPC ribbon) ──
# Active area: 86.4 x 64.8mm, centered with 2mm upward offset
DISPLAY_W = 86.4
DISPLAY_H = 64.8
DISPLAY_ENC = (0, 2)   # enclosure offset

# ── Physical panel — ILI9488 3.95" bare panel, resistive-touch version ──
# Vendor mechanical spec (website/static/img/ili9488-datasheet-specs.png):
#   outline 60.88(W) x 94.57(H) x 3.90(T) with touch (2.60 without)
#   active  55.68(W) x 83.52(H); FPC tail not included
# Landscape on the board: the 94.57 side runs along X. DISPLAY_W/H above
# is the F.Fab reserved zone drawn on the board; the enclosure viewport is
# the ACTIVE area and verify_enclosure_sync reads THESE constants as the
# panel source of truth. Nothing below is used by the generator.
PANEL_ACTIVE_W = 83.52   # along X (landscape)
PANEL_ACTIVE_H = 55.68   # along Y
PANEL_OUTLINE_L = 94.57  # along X
PANEL_OUTLINE_W = 60.88  # along Y
PANEL_T = 3.90           # with the resistive touch layer

# ── FPC slot (vertical cutout for 40-pin ribbon cable) ──
# Between display right edge (x=43.2) and ABXY left button (x=52)
FPC_SLOT_ENC = (47, 2)   # slot center in enclosure coords
FPC_SLOT_W = 3.0         # mm wide (enough for 0.3mm ribbon + clearance)
FPC_SLOT_H = 24.0        # mm tall (for ~22mm wide 40-pin FPC ribbon)

# ── TOP side (F.Cu): face buttons + LEDs ────────────────────────────

# D-pad buttons (left cluster)
DPAD_ENC = (-62, 5)
DPAD_OFFSETS = [(0, 9), (0, -9), (-9, 0), (9, 0)]  # UP, DN, LF, RT

# ABXY buttons (right cluster, wider diamond)
ABXY_ENC = (62, 5)
ABXY_OFFSETS = [(0, 10), (10, 0), (0, -10), (-9, 0)]  # A, B, X, Y — DFM: Y shifted right (enc -9 not -10); SW8 pad left edge at 129.4mm clears FPC slot edge (128.5mm) by 0.9mm >= 0.5mm required

# Start/Select (below D-pad area)
SS_ENC = (-62, -17)
SS_OFFSETS = [(-10, 0), (10, 0)]  # START, SELECT

# Menu button (front, bottom-right — below ABXY, outside display area)
# DFM: was (62,-25.7) → SW13 pads overlapped TF-01A (SD card) pads.
# Moved up 1.5mm: SW13 pad 1 bottom=59.9, TF pad top=61.05, gap=1.15mm ✓
MENU_ENC = (62, -24.2)

# Charging LEDs (front side, bottom-left)
LED_CHARGE_ENC = (-55, -30)    # Red LED — charging
LED_FULL_ENC = (-48, -30)      # LED2 (red, C19171391) — second power indicator; U2 LED pins are NC

# ── BOTTOM side (B.Cu): everything else ───────────────────────────

# ESP32-S3-WROOM-1 (center, back side)
ESP32_ENC = (0, 10)

# Shoulder L/R (near top edge, BACK side — rotated 90°, aligned to PCB top)
SHOULDER_L_ENC = (-65, 32)
SHOULDER_R_ENC = (65, 32)

# FPC display connector (right of slot, VERTICAL orientation)
# Rotated 90° — connector pads run vertically from y=25.75 to y=45.25 at x=135.
# NOTE: Display FPC pin order is REVERSED vs connector pad order.
# Display Pin N contacts connector pad (41-N) due to landscape CCW + straight-through slot.
# Connector body 3mm wide at x=133.5-136.5, slot right edge at 128.5.
FPC_ENC = (55, 2)      # Next to FPC slot, right side (vertical)

# USB-C (bottom center edge)
# R21 (2026-07-25): 3.80 -> 3.85 mm. The rear shield pads had to grow from
# 1.80 to 1.92 mm tall to reach a JLCPCB-legal 0.25 mm annular ring (see
# footprints.usb_c_16p, "ANNULAR BUDGET"), which pushed their outer edge to
# 0.425 mm from the board edge — under the 0.5 mm min_copper_edge_clearance
# in the board setup. Backing J1 off by 0.05 mm restores 0.515 mm while
# still leaving the front shield pads 0.205 mm clear of the BTN_B channel
# above them. Both ends are within ~0.015 mm of their limit: do not move
# J1, the board outline, or channel 5 without redoing that budget.
# The 0.05 mm shift is far inside 3D-print tolerance, so the enclosure
# USB-C cutout does not need to change.
USBC_ENC = (0, -BOARD_H / 2 + 3.85)  # 3.85mm from bottom edge (rear shield pads clear edge by 0.515mm)

# SD card slot (bottom right)
SD_ENC = (60, -BOARD_H / 2 + 8)

# Power slide switch (bottom edge, left of USB-C — accessible from enclosure)
PWR_SWITCH_ENC = (-40, -BOARD_H / 2 + 3)

# Speaker (back side, left area — 22mm diameter)
SPEAKER_ENC = (-50, -15)
SPEAKER_DIAM = 22.0

# IP5306 power management (left-center, back — moved from slot zone)
IP5306_ENC = (30, -5)
# U3 SY8089AAAC synchronous buck (SOT-23-5) — replaces the AMS1117 LDO.
# enc(39.8, -16) = pcb (119.8, 53.5). Placed so the IN/FB column faces WEST
# (inside the In2.Cu +5V pour) and LX/L2/C_OUT sit EAST of the pour on the
# continuous +3V3 plane. See routing._buck_traces().
BUCK_ENC = (39.8, -16.0)
# PAM8403 audio amplifier (left area, back)
PAM8403_ENC = (-50, 8)
# L1 inductor (near IP5306, with clearance)
INDUCTOR_ENC = (30, -15)
# JST PH battery connector (center, below passives, back)
# SMD version (C295747) — pads on B.Cu only, no through-hole
# R32 (2026-08-03): 0 -> -0.25 (pcb x 80.00 -> 79.75). Must stay equal to
# routing._shared.JST, which drives the pad-position table; the reason
# for the move is documented there.
JST_BAT_ENC = (-0.25, -25)
# Reset and Boot buttons (back side, right of USB-C — dev kit style)
RESET_ENC = (15, -28)     # EN pin to GND — hardware reset
BOOT_ENC = (25, -28)      # GPIO0 to GND — download mode when held during reset


def _board_outline():
    """Generate rounded rectangle board outline + FPC slot on Edge.Cuts."""
    r = CORNER_R
    w, h = BOARD_W, BOARD_H
    parts = []

    # Four straight edges
    parts.append(P.gr_line(r, 0, w - r, 0))          # Top
    parts.append(P.gr_line(w, r, w, h - r))           # Right
    parts.append(P.gr_line(w - r, h, r, h))           # Bottom
    parts.append(P.gr_line(0, h - r, 0, r))           # Left

    # Four corner arcs (start, mid, end).
    # The midpoint lies on the minor arc, pointing toward the board corner.
    diag = r * math.sqrt(2) / 2  # offset along 45-degree diagonal

    # Top-left corner (0,0): center (r, r)
    parts.append(P.gr_arc(0, r, r - diag, r - diag, r, 0))
    # Top-right corner (w,0): center (w-r, r)
    parts.append(P.gr_arc(w - r, 0, w - r + diag, r - diag, w, r))
    # Bottom-right corner (w,h): center (w-r, h-r)
    parts.append(P.gr_arc(w, h - r, w - r + diag, h - r + diag, w - r, h))
    # Bottom-left corner (0,h): center (r, h-r)
    parts.append(P.gr_arc(r, h, r - diag, h - r + diag, 0, h - r))

    # FPC slot — internal rectangular cutout for 40-pin ribbon cable
    sx, sy = enc_to_pcb(*FPC_SLOT_ENC)
    sw2 = FPC_SLOT_W / 2
    sh2 = FPC_SLOT_H / 2
    slot_x1 = sx - sw2   # left
    slot_x2 = sx + sw2   # right
    slot_y1 = sy - sh2   # top
    slot_y2 = sy + sh2   # bottom
    parts.append(P.gr_line(slot_x1, slot_y1, slot_x2, slot_y1))  # top
    parts.append(P.gr_line(slot_x2, slot_y1, slot_x2, slot_y2))  # right
    parts.append(P.gr_line(slot_x2, slot_y2, slot_x1, slot_y2))  # bottom
    parts.append(P.gr_line(slot_x1, slot_y2, slot_x1, slot_y1))  # left

    return "".join(parts)


def _mounting_holes():
    """Generate 6 M2.5 mounting holes."""
    parts = []
    for ex, ey in MOUNT_HOLES_ENC:
        px, py = enc_to_pcb(ex, ey)
        parts.append(P.mounting_hole(px, py))
    return "".join(parts)


def _silkscreen_labels():
    """Add labels on Fab layers + selective silkscreen for key components.

    DFM FIX: Most text on Fab layers to avoid silkscreen-to-hole violations.
    Only key IC/connector labels and branding are on SilkS, positioned in
    clear zones away from vias and drill holes.
    """
    parts = []

    # ── Front Fab (buttons + LEDs + display outline) ──

    # Display outline label
    dx, dy = enc_to_pcb(*DISPLAY_ENC)
    dw2, dh2 = DISPLAY_W / 2, DISPLAY_H / 2
    parts.append(P.gr_text(
        "DISPLAY AREA (ILI9488 3.95in)", dx, dy - dh2 - 2,
        "F.Fab", 1.0,
    ))

    # Board title on front Fab layer
    parts.append(P.gr_text(
        "ESP32-EMU-TURBO  CPJ & CP", CX, 73.0,
        "F.Fab", 1.5,
    ))

    # Button group labels (front Fab)
    px, py = enc_to_pcb(*DPAD_ENC)
    parts.append(P.gr_text("D-PAD", px, py - 20, "F.Fab"))
    px, py = enc_to_pcb(*ABXY_ENC)
    parts.append(P.gr_text("ABXY", px, py - 20, "F.Fab"))

    # Menu button label (front)
    px, py = enc_to_pcb(*MENU_ENC)
    parts.append(P.gr_text("MENU", px, py - 5, "F.Fab", 1.0))

    # LED labels (front side, bottom-left)
    px, py = enc_to_pcb(*LED_CHARGE_ENC)
    parts.append(P.gr_text("CHG", px, py + 3, "F.Fab", 1.0))
    px, py = enc_to_pcb(*LED_FULL_ENC)
    parts.append(P.gr_text("FULL", px, py + 3, "F.Fab", 1.0))

    # ── Front Silkscreen — labels + branding ──
    px, py = enc_to_pcb(*DPAD_ENC)
    parts.append(P.gr_text("D-PAD", px, py - 20, "F.SilkS"))
    px, py = enc_to_pcb(*ABXY_ENC)
    parts.append(P.gr_text("ABXY", px, py - 20, "F.SilkS"))
    px, py = enc_to_pcb(*MENU_ENC)
    # BELOW SW13, not above it. At py-5 the label sat at (142.0, 56.7),
    # which is inside the diagnostic LED bank added in workstream H — it
    # overlapped the "3V3" rail label and came within 0.098 mm of LED4's
    # anode pad (KiCad silk_overlap x2). Below the button the band is
    # empty: the nearest F.Cu is the BTN_A run at y=66.8, which stops at
    # x=130.4, and U6 underneath is on B.Cu so it cannot clip front silk.
    # At py+3.8 (142.0, 65.5) the glyph strokes crossed the 0.2mm vias at
    # (139.96, 66) and (141.5, 66) — JLCDFM silk-to-hole 0mm. (px-2.5,
    # py+5.8) sits between the via rows at y=66 and y=67.5/68 with
    # >=0.5mm hole clearance for the whole string.
    parts.append(P.gr_text("MENU", px - 2.5, py + 5.8, "F.SilkS", 1.0))
    px, py = enc_to_pcb(*LED_CHARGE_ENC)
    parts.append(P.gr_text("CHG", px, py + 3, "F.SilkS", 1.0))
    px, py = enc_to_pcb(*LED_FULL_ENC)
    parts.append(P.gr_text("FULL", px, py + 3, "F.SilkS", 1.0))
    # Diagnostic LED bank: name the rail each LED reports on, so the board
    # is readable during bring-up without a schematic. The labels sit in the
    # 2.7 mm gap between the resistor row (y=54) and the LED row (y=58), and
    # are nudged 1.2 mm west of centre to clear the LEDn_RA link, which runs
    # straight down the x+0.95 column between the two pads.
    for _r, _led, _rail, _ra, _lbl_txt in routing.DIAG_LEDS:
        parts.append(P.gr_text(
            _lbl_txt, routing.DIAG_X[_r] - 1.2, routing.DIAG_LABEL_Y,
            "F.SilkS", 1.0,
        ))
    # Front branding.
    # R21 FIX (2026-07-25): moved from (CX=80.0, 73.0) to (110.0, 73.0).
    # At x=80 the string straddled J1's rear shield through-holes, whose
    # solder-mask openings punch through to F.Mask even though the
    # connector itself is on the bottom side — KiCad DRC reported 2x
    # silk_over_copper ("Silkscreen clipped by solder mask", J1 pads 13
    # and 14). Enlarging those pads for the annular-ring fix made the
    # overlap worse, so the text moves instead of the copper.
    # (110.0, 73.0) keeps the branding on the same bottom edge of the
    # front side and is the widest mask-opening-free window there: the
    # whole span x=94.5..127.0 at this y is clear of pads and of any
    # other F.Silkscreen item, so an ~18 mm string at 1.2 mm height fits
    # with margin on both sides.
    parts.append(P.gr_text(
        "CPJ&CP 2026 v3", 110.0, 73.0, "F.SilkS", 1.2,
    ))

    # ── Back Fab (IC + connector labels, visible in 3D renders) ──
    px, py = enc_to_pcb(*ESP32_ENC)
    parts.append(P.gr_text("ESP32-S3", px, py - 16, "B.Fab"))
    px, py = enc_to_pcb(*IP5306_ENC)
    parts.append(P.gr_text("IP5306", px, py - 10, "B.Fab", 1.0))
    px, py = enc_to_pcb(*BUCK_ENC)
    parts.append(P.gr_text("SY8089", px + 1.2, py - 4.7, "B.Fab", 1.0))
    px, py = enc_to_pcb(*PAM8403_ENC)
    parts.append(P.gr_text("PAM8403", px, py - 5, "B.Fab", 1.0))

    # Connector labels (back side)
    px, py = enc_to_pcb(*USBC_ENC)
    parts.append(P.gr_text("USB-C", px, py - 6, "B.Fab", 1.0))
    px, py = enc_to_pcb(*SD_ENC)
    parts.append(P.gr_text("SD", px, py - 8, "B.Fab", 1.0))

    # Battery connector label (back side)
    px, py = enc_to_pcb(*JST_BAT_ENC)
    parts.append(P.gr_text("BATT", px, py - 5, "B.Fab", 1.0))

    # FPC display connector label (back side)
    px, py = enc_to_pcb(*FPC_ENC)
    parts.append(P.gr_text("LCD", px, py - 14, "B.Fab", 1.0))

    # Power switch label (back side)
    px, py = enc_to_pcb(*PWR_SWITCH_ENC)
    parts.append(P.gr_text("PWR", px, py - 5, "B.Fab", 1.0))

    # Speaker label (back side)
    px, py = enc_to_pcb(*SPEAKER_ENC)
    parts.append(P.gr_text("SPEAKER", px, py, "B.Fab", 1.0))

    # Shoulder button labels (back side)
    px, py = enc_to_pcb(*SHOULDER_L_ENC)
    parts.append(P.gr_text("L", px, py + 5, "B.Fab", 1.0))
    px, py = enc_to_pcb(*SHOULDER_R_ENC)
    parts.append(P.gr_text("R", px, py + 5, "B.Fab", 1.0))

    # Board title (back side)
    parts.append(P.gr_text(
        "ESP32-EMU-TURBO  CPJ & CP  2026", CX, 73.0,
        "B.Fab", 1.2,
    ))

    # ── Back Silkscreen — all component labels + branding ──
    # ICs
    px, py = enc_to_pcb(*ESP32_ENC)
    parts.append(P.gr_text("ESP32-S3", px, py - 16, "B.SilkS", 1.0))
    px, py = enc_to_pcb(*IP5306_ENC)
    # py-10 put the glyphs on the 0.2mm via at (111.8, 32.3); py-11.75
    # clears the via rows at y=32.3/33.0 by >=0.5mm.
    parts.append(P.gr_text("IP5306", px, py - 11.75, "B.SilkS", 1.0))
    # U3 buck label: the old spot (px+1.2, py-4.7) = (121.0, 48.8) crossed
    # the 0.2mm vias at (119.75, 48.75) and (121.7, 48.5). The next one,
    # (116.75, 47.3), was clear of C18.1 and the FPC slot — and then the
    # SW16 respin put Q2 at (118.2, 45.0), whose drain pad reaches down to
    # y=46.60. A centred 6-character label at 1.0 mm is ~4.3 mm wide, so
    # it ran east to x=118.9 and came within 0.053 mm of that pad against
    # a 0.14 mm silkscreen rule. Anchored 2.45 mm further west it ends at
    # x=116.5, 1.4 mm clear of the pad, and still north of C18 (y>=48.33)
    # and west of the FPC slot.
    px, py = enc_to_pcb(*BUCK_ENC)
    parts.append(P.gr_text("SY8089", px - 5.5, py - 6.2, "B.SilkS", 1.0))
    px, py = enc_to_pcb(*PAM8403_ENC)
    # py-5 = (30.0, 24.5) sat inside the audio via field (rows y=20.5..28.8,
    # hits at (26.825, 24.8) and (28.095, 23.7)). py-10.5 is the first
    # via-free band north of the amp with >=0.5mm hole clearance.
    parts.append(P.gr_text("PAM8403", px - 2.25, py - 10.5, "B.SilkS", 1.0))
    # Connectors
    px, py = enc_to_pcb(*USBC_ENC)
    # Centered (py-6) the glyphs crossed the 0.2mm via at (79.75, 64.525);
    # px+4.5 shifts the label east of the via cluster (74.9..81.3, y=63.8..67.4).
    parts.append(P.gr_text("USB-C", px + 4.5, py - 6, "B.SilkS", 1.0))
    px, py = enc_to_pcb(*SD_ENC)
    parts.append(P.gr_text("SD", px, py - 8, "B.SilkS", 1.0))
    px, py = enc_to_pcb(*JST_BAT_ENC)
    # v4.0: moved label up to clear Q1 P-MOSFET + debounce caps (DFA: Q1 at y=52.5)
    # Moved again from py-15 (y=47.5): the BAT+ layer transition now stitches
    # a row of 0.45mm barrels along y=47.275 and the anchor sat 0.36mm from
    # the westmost one, under the 0.5mm JLCDFM silk-to-hole rule. py-13.9
    # keeps it in the same corridor between the R11/R12 and C12/C13 rows,
    # 1.35mm from the nearest hole and 0.25mm clear of the C12/C13 pads.
    parts.append(P.gr_text("BATT", px, py - 13.9, "B.SilkS", 1.0))
    px, py = enc_to_pcb(*FPC_ENC)
    # py-14 = (135.0, 21.5) clipped the 0.2mm via at (135.2, 22.2);
    # py-14.75 clears the via rows at y=22.2/22.48 by >=0.5mm.
    parts.append(P.gr_text("LCD", px, py - 14.75, "B.SilkS", 1.0))
    px, py = enc_to_pcb(*PWR_SWITCH_ENC)
    parts.append(P.gr_text("PWR", px, py - 5, "B.SilkS", 1.0))
    # Speaker + shoulder buttons
    px, py = enc_to_pcb(*SPEAKER_ENC)
    parts.append(P.gr_text("SPEAKER", px, py, "B.SilkS", 1.0))
    px, py = enc_to_pcb(*SHOULDER_L_ENC)
    parts.append(P.gr_text("L", px, py + 5, "B.SilkS", 1.0))
    px, py = enc_to_pcb(*SHOULDER_R_ENC)
    parts.append(P.gr_text("R", px, py + 5, "B.SilkS", 1.0))

    # Branding (back side, top edge). At y=3.0 the string crossed the
    # diagonal 0.2mm via run at (76, 2.2)/(77, 2.9)/(78, 3.6); y=5.25 is
    # below that run with >=0.5mm hole clearance across the full width.
    parts.append(P.gr_text(
        "CPJ&CP 2026 v3", CX, 5.25, "B.SilkS", 1.2,
    ))

    # ── Passive component labels (B.Fab) ────────────────────────
    # Group labels for the pull-up and debounce rows (12 components each)
    # Pull-ups: R4-R15 at y=46, x=43..98 (5mm spacing)
    # R9-MED-4 (2026-04-11): R19 and C20 removed (dead BTN_MENU net).
    parts.append(P.gr_text(
        "R4-R15  10k", 70, 43.5, "B.Fab", 0.6,
    ))
    # Debounce caps: C5-C16 at y=50, x=43..98
    parts.append(P.gr_text(
        "C5-C16  100nF", 70, 52.5, "B.Fab", 0.6,
    ))

    # Individual power passives — label offset to clear 0805 body (~2x1.2mm)
    _lbl = 0.5  # text size for individual labels
    _passive_labels = [
        # (ref, value, x, y, label_dx, label_dy)
        # USB CC pull-downs
        ("R1", "5.1k", 74.0, 67.0, 0, -2.0),
        ("R2", "5.1k", 78.0, 67.0, 5.0, -1.0),
        # ESP32 decoupling
        ("C3", "100nF", 69.5, 42.0, 0, -2.0),
        ("C4", "100nF", 92.0, 42.0, 0, -2.0),
        # LED resistors
        ("R17", "1k", 25.0, 65.0, 0, -2.0),
        ("R18", "1k", 32.0, 65.0, 0, -2.0),
        # IP5306 area
        # SW16 respin gate network (R16 deleted — see the placement block)
        ("C33", "4.7uF", 115.0, 52.5, 0, -2.0),
        ("R32", "22k", 116.3, 40.0, 3.4, 0),
        ("C32", "1uF", 116.3, 37.48, 3.4, 0),
        ("R33", "1k", 116.3, 42.0, -3.4, 0),
        ("R34", "1M", 86.1, 55.9, 0, 2.4),
        ("C17", "10uF", 110.0, 35.0, 4.5, 0),
        ("C18", "10uF", 116.0, 49.0, 0, 2.5),
        ("C19", "22uF", 110.0, 58.5, 0, 2.5),
        # U3 SY8089 buck converter cluster (C2 tantalum deleted)
        ("C1", "22uF", 119.8, 56.6, 0, 2.5),
        ("C30", "22uF", 127.8, 58.9, -3.2, 0),
        ("R25", "100k", 118.0, 63.4, 0, -1.6),
        ("R26", "22k", 121.1, 63.4, 0, -1.6),
        ("C29", "22pF", 118.0, 60.3, 0, -1.6),
        # Inductors
        ("L1", "1uH", 110.0, 52.5, -4.5, 0),
        ("L2", "2.2uH", 126.0, 54.45, 0, 3.2),
        # PAM8403 passives — right side of U5
        ("C21", "100nF", 38.0, 23.5, 0, -2.0),
        ("C22", "0.47u", 33.175, 20.0, -3.5, 0),
        ("R20", "20k", 38.0, 26.5, 3.5, 0),
        ("C23", "1uF", 38.0, 29.5, 3.5, 0),
        ("R21", "20k", 38.0, 32.5, 3.5, 0),
        # PAM8403 passives — above/below U5
        ("C24", "1uF", 29.365, 22.0, -3.0, 0),
        ("C25", "1uF", 31.5, 37.5, 0, 2.5),
    ]
    for ref, val, cx, cy, dx, dy in _passive_labels:
        parts.append(P.gr_text(
            f"{ref} {val}", cx + dx, cy + dy, "B.Fab", _lbl,
        ))

    return "".join(parts)


def _display_outline():
    """Draw display module outline on F.SilkS."""
    dx, dy = enc_to_pcb(*DISPLAY_ENC)
    dw2, dh2 = DISPLAY_W / 2, DISPLAY_H / 2
    parts = []
    x1, y1 = dx - dw2, dy - dh2
    x2, y2 = dx + dw2, dy + dh2
    for layer in ("F.Fab",):  # DFM: F.Fab avoids silk_over_copper at bottom edge
        parts.append(P.gr_line(x1, y1, x2, y1, layer=layer, width=0.2))
        parts.append(P.gr_line(x2, y1, x2, y2, layer=layer, width=0.2))
        parts.append(P.gr_line(x2, y2, x1, y2, layer=layer, width=0.2))
        parts.append(P.gr_line(x1, y2, x1, y1, layer=layer, width=0.2))
    return "".join(parts)


def _component_placeholders():
    """Generate footprints with real pad definitions."""
    parts = []
    placements = []

    # ── TOP side (F.Cu): face buttons + LEDs + menu ──

    # D-pad switches (SW1-SW4)
    for i, (dx, dy) in enumerate(DPAD_OFFSETS):
        bx, by = DPAD_ENC
        px, py = enc_to_pcb(bx + dx, by + dy)
        placements.append((f"SW{i+1}", "SW-SMD-5.1x5.1",
                            px, py, 0, "F.Cu"))

    # ABXY switches (SW5-SW8)
    for i, (dx, dy) in enumerate(ABXY_OFFSETS):
        bx, by = ABXY_ENC
        px, py = enc_to_pcb(bx + dx, by + dy)
        placements.append((f"SW{i+5}", "SW-SMD-5.1x5.1",
                            px, py, 0, "F.Cu"))

    # Start/Select (SW9-SW10)
    for i, (dx, dy) in enumerate(SS_OFFSETS):
        bx, by = SS_ENC
        px, py = enc_to_pcb(bx + dx, by + dy)
        placements.append((f"SW{i+9}", "SW-SMD-5.1x5.1",
                            px, py, 0, "F.Cu"))

    # Menu button (SW13, front bottom center)
    px, py = enc_to_pcb(*MENU_ENC)
    placements.append(("SW13", "SW-SMD-5.1x5.1", px, py, 0, "F.Cu"))

    # Charging LEDs (front side, bottom-left)
    px, py = enc_to_pcb(*LED_CHARGE_ENC)
    placements.append(("LED1", "LED_0805", px, py, 0, "F.Cu"))
    px, py = enc_to_pcb(*LED_FULL_ENC)
    placements.append(("LED2", "LED_0805", px, py, 0, "F.Cu"))

    # ── BOTTOM side (B.Cu): everything else ──

    px, py = enc_to_pcb(*ESP32_ENC)
    placements.append(("U1", "ESP32-S3-WROOM-1-N16R8",
                        px, py, 0, "B.Cu"))

    px, py = enc_to_pcb(*SHOULDER_L_ENC)
    placements.append(("SW11", "SW-SMD-5.1x5.1", px, py, 90, "B.Cu"))
    px, py = enc_to_pcb(*SHOULDER_R_ENC)
    placements.append(("SW12", "SW-SMD-5.1x5.1", px, py, 90, "B.Cu"))

    px, py = enc_to_pcb(*FPC_ENC)
    placements.append(("J4", "FPC-40P-0.5mm", px, py, 90, "B.Cu"))

    px, py = enc_to_pcb(*USBC_ENC)
    placements.append(("J1", "USB-C-16P", px, py, 0, "B.Cu"))

    px, py = enc_to_pcb(*SD_ENC)
    placements.append(("U6", "TF-01A", px, py, 0, "B.Cu"))

    px, py = enc_to_pcb(*PWR_SWITCH_ENC)
    placements.append(("SW16", "SS-12D00G3", px, py, 0, "B.Cu"))

    px, py = enc_to_pcb(*SPEAKER_ENC)
    placements.append(("SPK1", "Speaker-28mm", px, py, 0, "B.Cu"))

    px, py = enc_to_pcb(*IP5306_ENC)
    placements.append(("U2", "ESOP-8", px, py, 0, "B.Cu"))

    px, py = enc_to_pcb(*BUCK_ENC)
    placements.append(("U3", "SOT-23-5", px, py, 180, "B.Cu"))

    px, py = enc_to_pcb(*PAM8403_ENC)
    placements.append(("U5", "SOP-16", px, py, 90, "B.Cu"))

    px, py = enc_to_pcb(*INDUCTOR_ENC)
    placements.append(("L1", "SMD-4x4x2", px, py, 0, "B.Cu"))
    # L2: SY8089 buck output inductor (2.2uH, SWPA4030S2R2MT / C36409)
    placements.append(("L2", "IND-SMD-4.0x4.0", *routing.L2_POS, 0, "B.Cu"))

    px, py = enc_to_pcb(*JST_BAT_ENC)
    placements.append(("J3", "JST-PH-2P-SMD", px, py, 180, "B.Cu"))

    # Reset and Boot buttons (B.Cu, right of USB-C — dev kit style)
    px, py = enc_to_pcb(*RESET_ENC)
    placements.append(("SW15", "SW-SMD-5.1x5.1", px, py, 0, "B.Cu"))
    px, py = enc_to_pcb(*BOOT_ENC)
    placements.append(("SW14", "SW-SMD-5.1x5.1", px, py, 0, "B.Cu"))

    # BAT54C dual Schottky diode — menu combo (START+SELECT)
    placements.append(("D1", "SOT-23-3", *routing.D1_POS, routing.D1_ROT, "B.Cu"))

    # P-MOSFET reverse polarity protection (v4.0)
    placements.append(("Q1", "SOT-23-3", *routing.Q1_POS, routing.Q1_ROT, "B.Cu"))
    placements.append(("R24", "R_0805", *routing.R24_POS, routing.R24_ROT, "B.Cu"))

    # ── Passive components (B.Cu) ──
    # Positions must match jlcpcb_export.py for CPL/Gerber alignment.

    # USB-C CC resistors (positions synced with routing.R1_POS/R2_POS)
    placements.append(("R1", "R_0805", *routing.R1_POS, 0, "B.Cu"))
    placements.append(("R2", "R_0805", *routing.R2_POS, 0, "B.Cu"))

    # USB ESD protection (TVS + 22Ω series resistors)
    placements.append(("U4", "SOT-23-6", *routing.U4_POS, 0, "B.Cu"))
    placements.append(("R22", "R_0402", *routing.R22_POS, 90, "B.Cu"))
    placements.append(("R23", "R_0402", *routing.R23_POS, 90, "B.Cu"))

    # ESP32 decoupling (y=42, below ESP32 body edge at 40.25)
    placements.append(("C3", "C_0805", 69.55, 42, 0, "B.Cu"))  # DFM: 0.05mm right (BTN_UP gap 0.095→0.145mm)
    placements.append(("C4", "C_0805", 92, 42, 0, "B.Cu"))  # DFM: moved from 85 (pad1@85.95 hit U1[16]@85.715)
    placements.append(("C26", "C_0805", *routing.C26_POS, 90, "B.Cu"))  # ESP32 VDD bypass (3.6mm from pin 2)

    # EN RC delay network (R25-CRIT-1 respin fix): 10k pull-up + 100nF on
    # the EN trace east of U1 pin 3 — see routing._shared R3_POS comment.
    placements.append(("R3", "R_0805", *routing.R3_POS, 90, "B.Cu"))
    placements.append(("C31", "C_0805", *routing.C31_POS, 90, "B.Cu"))

    # Backlight series resistor (R25-HIGH-1 respin fix): +5V -> R27 -> LED_BLA
    placements.append(("R27", "R_1206", *routing.R27_POS, 90, "B.Cu"))

    # VBUS PTC fuse (R3-HIGH-4 fix): J1 -> VBUS_IN -> F1 -> VBUS
    placements.append(("F1", "F_1812", *routing.F1_POS, 270, "B.Cu"))

    # LED current-limiting resistors (B.Cu, near LEDs on F.Cu)
    placements.append(("R17", "R_0805", 25, 65, 0, "B.Cu"))
    placements.append(("R18", "R_0805", 32, 65, 0, "B.Cu"))

    # Diagnostic LED bank (workstream H) — everything on F.Cu, two rows.
    # Resistors are rot=180 so pad 2 (rail) faces west; see the DIAG_*
    # block in routing/_shared.py for the placement arithmetic.
    for _r, _led, _rail, _ra, _lbl_txt in routing.DIAG_LEDS:
        placements.append((_r, "R_0805", routing.DIAG_X[_r],
                           routing.DIAG_R_Y, 180, "F.Cu"))
        placements.append((_led, "LED_0805", routing.DIAG_X[_r],
                           routing.DIAG_LED_Y, 0, "F.Cu"))

    # Pull-up resistors (y=46, x=43..98, 5mm spacing)
    # R9-MED-4: R19 deleted (was on dead BTN_MENU net).
    pull_up_refs = [f"R{i}" for i in range(4, 16)]
    for i, ref in enumerate(pull_up_refs):
        placements.append((ref, "R_0805", 43 + i * 5, 46, 0, "B.Cu"))

    # SW16 respin — Q2 high-side +5V load switch and its gate network.
    # R16 (the old 100k IP5306_KEY pull-up to +5V) is DELETED: on the new
    # LOAD-side +5V it would invert into a pull-DOWN whenever the switch is
    # OFF and hold KEY asserted. C33, the wake cap, takes over its exact
    # footprint site and its routing.
    placements.append(("Q2", "SOT-23-3", *routing.Q2_POS, routing.Q2_ROT, "B.Cu"))
    placements.append(("R32", "R_0805", *routing.R32_POS, routing.R32_ROT, "B.Cu"))
    placements.append(("C32", "C_0805", *routing.C32_POS, routing.C32_ROT, "B.Cu"))
    placements.append(("R33", "R_0805", *routing.R33_POS, routing.R33_ROT, "B.Cu"))
    placements.append(("R34", "R_0805", *routing.R34_POS, routing.R34_ROT, "B.Cu"))
    placements.append(("C33", "C_0805", *routing.C33_POS, routing.C33_ROT, "B.Cu"))
    # SW17, the manual KEY wake button: the LAND exists on the board, but
    # the part is DNP and is deliberately absent from the CPL, so JLCPCB
    # never populates it. Placement argument in routing/_shared.py.
    placements.append(("SW17", "SW-SMD-2P-TS1088",
                       *routing.SW17_POS, routing.SW17_ROT, "B.Cu"))

    # Debounce caps (y=50, x=43..98, 5mm spacing)
    # R9-MED-4: C20 deleted (was on dead BTN_MENU net).
    debounce_refs = [f"C{i}" for i in range(5, 17)]
    for i, ref in enumerate(debounce_refs):
        placements.append((ref, "C_0805", 43 + i * 5, 50, 0, "B.Cu"))

    # IP5306 support caps
    placements.append(("C17", "C_0805", 110, 35, 0, "B.Cu"))
    placements.append(("C18", "C_0805", 116, 49, 0, "B.Cu"))  # BAT decoupling — 10.7mm from IP5306 pin 6

    # C19 near inductor L1 (VOUT bulk cap)
    lx, ly = enc_to_pcb(*INDUCTOR_ENC)
    placements.append(("C19", "C_1206", lx, ly + 6, 0, "B.Cu"))

    # C27 near IP5306 VOUT (HF decoupling, 2.6mm from pin 8)
    placements.append(("C27", "C_0805", 108, 39, 0, "B.Cu"))

    # C28 ESP32 +3V3 bulk cap (10uF, 2.8mm from U1 pin 2)
    placements.append(("C28", "C_0805", *routing.C28_POS, 90, "B.Cu"))

    # PAM8403 passive components (B.Cu)
    # PAM8403 passives — spread ~2mm from body for clean layout
    placements.append(("C22", "C_0805", *routing.C22_POS, 90, "B.Cu"))  # DC-blocking
    placements.append(("R20", "R_0805", *routing.R20_POS, 0, "B.Cu"))   # INL bias
    placements.append(("R21", "R_0805", *routing.R21_POS, 0, "B.Cu"))   # INR bias
    placements.append(("C21", "C_0805", *routing.C21_POS, 0, "B.Cu"))   # VREF bypass
    placements.append(("C23", "C_0805", *routing.C23_POS, 90, "B.Cu"))  # VDD decoupling
    placements.append(("C24", "C_0805", *routing.C24_POS, 90, "B.Cu"))  # PVDD top
    placements.append(("C25", "C_0805", *routing.C25_POS, 90, "B.Cu"))  # PVDD bottom

    # U3 SY8089 buck passives. C2 (22uF tantalum) is DELETED — a 1 MHz buck
    # needs a low-ESR MLCC output cap, and C2 is the part that destroyed
    # prototype #1 when assembled reversed.
    placements.append(("C1", "C_1206", *routing.C1_POS, 180, "B.Cu"))   # C_IN 22uF MLCC
    placements.append(("C30", "C_1206", *routing.C30_POS, 90, "B.Cu"))  # C_OUT 22uF MLCC
    placements.append(("R25", "R_0805", *routing.R25_POS, 180, "B.Cu"))   # FB upper 100k
    placements.append(("R26", "R_0805", *routing.R26_POS, 180, "B.Cu"))   # FB lower 22k
    placements.append(("C29", "C_0805", *routing.C29_POS, 180, "B.Cu"))   # 22pF feed-forward

    # Board-level fiducials at opposite corners for pick-and-place alignment.
    # 1mm copper dot, 2mm mask opening (0.5mm margin), no paste.
    # FID1 at (12, 12): 5.4mm from MH(10,7), copper gap=3.14mm ✓
    # FID2 at (150, 63): moved from (148,63) — old position overlapped via at
    # (148.76, 62.574) with gap=-0.04mm. New position: 5.0mm from MH(150,68),
    # copper gap=2.75mm ✓. No vias nearby ✓.
    placements.append(("FID1", "Fiducial", 12, 12, 0, "F.Cu"))
    placements.append(("FID2", "Fiducial", 150, 63, 0, "F.Cu"))
    # FID3 at (12, 63): 5.4mm from MH(10,68), provides 3-point alignment
    # for JLCPCB fine-pitch SMT (J4 FPC 0.5mm, ESP32).
    placements.append(("FID3", "Fiducial", 12, 63, 0, "F.Cu"))

    # Per-footprint text Y offsets to clear pads (silkscreen-to-pad DFM)
    _text_offsets = {
        "ESP32-S3-WROOM-1-N16R8": (-15, 15),
        "USB-C-16P": (-6, 4),
        "FPC-40P-0.5mm": (-12, 12),
        "TF-01A": (-8, 8),
        "SOP-16": (-7, 7),
        "ESOP-8": (-5, 5),
        "SOT-223": (-5, 5),
        "SOT-23-5": (-3, 3),
        "Speaker-28mm": (-13, 13),
        "JST-PH-2P-SMD": (-3, 3),
        "SS-12D00G3": (-4, 4),
        "SMD-4x4x2": (-4, 4),
        "IND-SMD-4.0x4.0": (-4, 4),
        "Fiducial": (-2, 2),
        "SOT-23-3": (-3, 3),
    }

    # Passives: text on Fab layer (not silkscreen) to avoid DFM violations
    _passive_fps = {"R_0805", "C_0805", "LED_0805", "C_1206"}

    # Generate footprints with real pad geometries
    # Pads are pre-rotated so the footprint is placed with rotation=0.
    # This ensures gerber apertures have the correct orientation
    # (kicad-cli does not rotate pad aperture shapes for rotated footprints).
    for ref, fp_name, x, y, rot, layer in placements:
        layer_char = "F" if "F." in layer else "B"
        pads = FP.get_pads(fp_name, layer_char, rotation=rot)
        pads = [_inject_pad_net(p, ref) for p in pads]
        pad_str = "".join(pads)
        mirror = " (justify mirror)" if "B." in layer else ""
        ref_y, val_y = _text_offsets.get(fp_name, (-3, 3))

        # ALL refs on Fab layer — SilkS causes silk_over_copper DFM violations.
        # Component labels added as separate gr_text in _silkscreen_labels().
        text_layer = "F.Fab" if layer_char == "F" else "B.Fab"
        ref_layer = text_layer
        text_size = 0.6 if fp_name in _passive_fps else 1

        parts.append(
            f'  (footprint "{fp_name}" (at {x} {y})'
            f' (layer "{layer}")\n'
            f'    (uuid "{P.uid()}")\n'
            f'    (property "Reference" "{ref}"'
            f' (at 0 {ref_y} 0) (layer "{ref_layer}")'
            f' (effects (font (size {text_size} {text_size})'
            f' (thickness 0.2)){mirror}))\n'
            f'    (property "Value" "{fp_name}"'
            f' (at 0 {val_y} 0) (layer "{text_layer}")'
            f' (effects (font (size {text_size} {text_size})'
            f' (thickness 0.2)){mirror}))\n'
            f'{pad_str}'
            f'  )\n'
        )

    return "".join(parts), placements


def _all_routing():
    """Generate all traces, vias, and copper zones via routing module."""
    return routing.generate_all_traces()


def generate_board() -> str:
    """Generate the complete .kicad_pcb content."""
    parts = [
        P.header(),
        P.layers_4layer(),
        P.setup_4layer(),
        "\n",
        P.nets(),
        "\n",
        _board_outline(),
        "\n",
        _mounting_holes(),
        "\n",
        _display_outline(),
        "\n",
        _silkscreen_labels(),
        "\n",
    ]
    # Generate routing FIRST to populate pad-net mapping (_PAD_NETS),
    # then generate footprints with correct net assignments injected.
    routing_str = _all_routing()
    comp_str, _placements = _component_placeholders()
    parts.append(comp_str)
    parts.append("\n")
    parts.append(routing_str)
    parts.append(P.footer())
    return "".join(parts)
