pjcau/esp32-emu-turbo/scripts/verify_dfm_v2.py

#!/usr/bin/env python3
"""Verify DFM v2 fixes: CPL alignment, silkscreen, spacing, gerbers."""

import csv
import json
import math
import os
import re
import shutil
import subprocess
import sys
import zipfile

_ROTATION_LAW = None


def _load_rotation_law():
    """Import verify_cpl_rotation_law as a module (cached).

    Loaded lazily and by path rather than imported at module scope: this file
    is executed directly from several working directories, and evaluate() is
    only needed by the J4 check.
    """
    global _ROTATION_LAW
    if _ROTATION_LAW is None:
        import importlib.util
        path = os.path.join(os.path.dirname(os.path.abspath(__file__)),
                            "verify_cpl_rotation_law.py")
        spec = importlib.util.spec_from_file_location("_cpl_law", path)
        mod = importlib.util.module_from_spec(spec)
        spec.loader.exec_module(mod)
        _ROTATION_LAW = mod
    return _ROTATION_LAW


def _capsule_rect_gap(x1, y1, x2, y2, hw, bx1, by1, bx2, by2):
    """Exact edge-to-edge gap between a trace capsule and an AABB.

    Trace copper is every point within `hw` of the centreline segment, so
    the gap is (segment-to-rectangle distance) - hw. Negative means the
    copper overlaps the rectangle. Both shapes are convex, so the minimum
    is attained at a segment endpoint or a rectangle corner.

    Needed because a segment's own AABB only equals its copper when the
    segment is horizontal or vertical; for a diagonal it is the bounding
    box of the capsule and reports overlaps that do not exist.
    """
    def _point_rect_dist(px, py):
        return math.hypot(max(bx1 - px, 0.0, px - bx2),
                          max(by1 - py, 0.0, py - by2))

    def _point_seg_dist(px, py):
        vx, vy = x2 - x1, y2 - y1
        l2 = vx * vx + vy * vy
        if l2 <= 0.0:
            return math.hypot(px - x1, py - y1)
        t = max(0.0, min(1.0, ((px - x1) * vx + (py - y1) * vy) / l2))
        return math.hypot(px - (x1 + t * vx), py - (y1 + t * vy))

    dist = min(_point_rect_dist(x1, y1), _point_rect_dist(x2, y2))
    for cx, cy in ((bx1, by1), (bx2, by1), (bx1, by2), (bx2, by2)):
        dist = min(dist, _point_seg_dist(cx, cy))
    return dist - hw

BASE = os.path.dirname(os.path.dirname(os.path.abspath(__file__)))
RELEASE = os.path.join(BASE, "release_jlcpcb")
PCB_FILE = os.path.join(BASE, "hardware", "kicad", "esp32-emu-turbo.kicad_pcb")

PASS = 0
FAIL = 0


def check(name, condition, detail=""):
    global PASS, FAIL
    if condition:
        PASS += 1
        print(f"  PASS  {name}")
    else:
        FAIL += 1
        print(f"  FAIL  {name}  {detail}")


def read_cpl():
    rows = {}
    with open(os.path.join(RELEASE, "cpl.csv")) as f:
        reader = csv.DictReader(f)
        for row in reader:
            ref = row["Designator"]
            rows[ref] = row
    return rows


def test_cpl_positions():
    """Test 1-4: CPL position and rotation corrections."""
    print("\n── CPL Position & Rotation Tests ──")
    cpl = read_cpl()

    # J1: footprint now matches JLCPCB C2765186 exactly, no position correction needed
    # R21 (2026-07-25): 71.20 -> 71.15. The rear shield pads grew to 1.92mm
    # tall for a JLCPCB-legal 0.25mm annular ring, so J1 had to back 0.05mm
    # off the board edge (see footprints.usb_c_16p "ANNULAR BUDGET").
    j1_y = float(cpl["J1"]["Mid Y"].replace("mm", ""))
    check("J1 Mid Y = 71.15mm (DFM: shield pads clear board edge)", abs(j1_y - 71.15) < 0.01,
          f"got {j1_y}")

    # SW16: footprint now matches JLCPCB C431540 exactly, no correction needed
    sw_y = float(cpl["SW16"]["Mid Y"].replace("mm", ""))
    check("SW16 Mid Y = 72.00mm (no correction, footprint matches JLCPCB)", abs(sw_y - 72.00) < 0.01,
          f"got {sw_y}")

    # U1: ESP32 correction +3.62 still applied
    u1_y = float(cpl["U1"]["Mid Y"].replace("mm", ""))
    check("U1 Mid Y = 31.12mm (ESP32 correction)", abs(u1_y - 31.12) < 0.01,
          f"got {u1_y}")

    # U5: formula rotation — 180° aligns pre-rotated SOP-16 with JLCPCB C5122557 model
    u5_rot = int(cpl["U5"]["Rotation"])
    check("U5 rotation = 180 (JLCPCB DFM verified)", u5_rot == 180,
          f"got {u5_rot}")


def test_silkscreen_on_fab():
    """Test 5: All footprint Reference/Value text on Fab layers, not SilkS."""
    print("\n── Silkscreen Text Tests ──")
    with open(PCB_FILE) as f:
        content = f.read()

    # Find all footprint blocks and check their text layers
    violations = []
    # Match footprint blocks with their Reference/Value properties
    fp_pattern = re.compile(
        r'\(footprint "([^"]+)".*?\n.*?\(property "Reference" "([^"]*)"'
        r'.*?\(layer "([^"]+)"\)',
        re.DOTALL,
    )
    for m in fp_pattern.finditer(content):
        fp_name, ref, layer = m.group(1), m.group(2), m.group(3)
        if "SilkS" in layer and ref:  # empty ref (mounting holes) is ok
            violations.append(f"{ref} ({fp_name}) on {layer}")

    check("No footprint Reference on SilkS", len(violations) == 0,
          f"{len(violations)} violations: {violations[:5]}")


def test_mounting_hole_text():
    """Test 6: Mounting hole Reference on Fab, not SilkS."""
    print("\n── Mounting Hole Text Tests ──")
    with open(PCB_FILE) as f:
        content = f.read()

    # Find MountingHole footprints
    mh_pattern = re.compile(
        r'\(footprint "MountingHole[^"]*".*?\(property "Reference" ""'
        r'.*?\(layer "([^"]+)"\)',
        re.DOTALL,
    )
    silk_holes = 0
    fab_holes = 0
    for m in mh_pattern.finditer(content):
        layer = m.group(1)
        if "SilkS" in layer:
            silk_holes += 1
        elif "Fab" in layer:
            fab_holes += 1

    check("Mounting hole Reference on Fab (not SilkS)",
          silk_holes == 0 and fab_holes > 0,
          f"SilkS={silk_holes}, Fab={fab_holes}")


def test_c1_c2_spacing():
    """Test 7: SY8089 buck (U3) hot-loop geometry.

    Replaces the old AMS1117 C1/C2 spacing test. C2 (22uF tantalum) no
    longer exists — the buck uses C30, a non-polarized MLCC, on its output.

    What matters for a 1 MHz switcher (datasheet AN_SY8089/A page 8):
      - C1 (C_IN) must sit as close as the land patterns allow to the
        IN/GND pins, so the high-di/dt loop stays small.
      - C30 (C_OUT) must sit close to the inductor output pad.
      - The LX node must stay small.
    These are geometric facts read back from the CPL, so a placement
    regression is caught immediately.
    """
    print("\n── SY8089 Buck Loop Geometry Tests ──")
    import math
    cpl = read_cpl()

    check("C2 (22uF tantalum) removed from CPL", "C2" not in cpl,
          "C2 still present — it must not be assembled")

    c1_x = float(cpl["C1"]["Mid X"].replace("mm", ""))
    c1_y = float(cpl["C1"]["Mid Y"].replace("mm", ""))
    u3_x = float(cpl["U3"]["Mid X"].replace("mm", ""))
    u3_y = float(cpl["U3"]["Mid Y"].replace("mm", ""))
    c30_x = float(cpl["C30"]["Mid X"].replace("mm", ""))
    c30_y = float(cpl["C30"]["Mid Y"].replace("mm", ""))
    l2_x = float(cpl["L2"]["Mid X"].replace("mm", ""))
    l2_y = float(cpl["L2"]["Mid Y"].replace("mm", ""))

    check("U3 Mid = (119.80, 53.50)",
          abs(u3_x - 119.80) < 0.01 and abs(u3_y - 53.50) < 0.01,
          f"got ({u3_x}, {u3_y})")

    # C_IN centre-to-centre distance from the regulator. SOT-23-5 pads end
    # at u3_y+1.25; the 1206 pads start at c1_y-0.90 → 0.95mm edge gap.
    d_c1_u3 = math.hypot(c1_x - u3_x, c1_y - u3_y)
    check("C_IN (C1) within 3.5mm of U3", d_c1_u3 <= 3.5,
          f"dist={d_c1_u3:.2f}mm")
    c1_pad_top = c1_y - 0.90        # 1206 pad half-height
    u3_pad_bot = u3_y + 1.25        # SOT-23-5 pad row + half pad height
    check("C1-U3 pad gap in 0.20..1.50mm (tight hot loop, assemblable)",
          0.20 <= (c1_pad_top - u3_pad_bot) <= 1.50,
          f"gap={c1_pad_top - u3_pad_bot:.2f}mm")

    # C_OUT next to the inductor output pad.
    d_c30_l2 = math.hypot(c30_x - l2_x, c30_y - l2_y)
    check("C_OUT (C30) within 5.5mm of L2", d_c30_l2 <= 5.5,
          f"dist={d_c30_l2:.2f}mm")

    # LX node length: U3 pin 3 (u3_x+1.30, u3_y+0.95) to L2 pad 2
    # (l2_x-1.80, l2_y). Datasheet rule 3: minimise LX copper.
    lx_len = math.hypot((l2_x - 1.80) - (u3_x + 1.30),
                        l2_y - (u3_y + 0.95))
    check("BUCK_LX run <= 4.0mm (minimise switch-node copper)",
          lx_len <= 4.0, f"len={lx_len:.2f}mm")


def test_gr_text_vs_holes():
    """Test 8: No gr_text within 6mm of mounting hole centers."""
    print("\n── gr_text vs Mounting Holes ──")
    # Mounting hole positions (PCB coords)
    holes = [(10, 7), (150, 7), (10, 68), (150, 68), (55, 37.5), (105, 37.5)]

    with open(PCB_FILE) as f:
        content = f.read()

    # Find all gr_text positions
    gr_pattern = re.compile(
        r'\(gr_text "([^"]+)" \(at ([\d.]+) ([\d.]+)\)',
    )
    violations = []
    for m in gr_pattern.finditer(content):
        text, x, y = m.group(1), float(m.group(2)), float(m.group(3))
        for hx, hy in holes:
            dist = ((x - hx)**2 + (y - hy)**2)**0.5
            if dist < 6.0:
                violations.append(f'"{text}" at ({x},{y}) dist={dist:.1f}mm '
                                  f'from hole ({hx},{hy})')

    check("No gr_text within 6mm of mounting holes",
          len(violations) == 0,
          f"{len(violations)} violations: {violations[:3]}")


def test_via_annular_ring():
    """Test 9: All vias have annular ring >= 0.075mm (JLCPCB absolute min).

    JLCPCB standard PCB minimum annular ring is 0.075mm.
    Right-side button approach vias use 0.35mm/0.20mm (ring=0.075mm) to allow
    wider column spacing in the FPC slot corridor.
    """
    print("\n── Via Annular Ring Tests ──")
    with open(PCB_FILE) as f:
        content = f.read()

    via_pattern = re.compile(r'\(via\b.*?\(size ([\d.]+)\).*?\(drill ([\d.]+)\)')
    total = 0
    violations = 0
    for m in via_pattern.finditer(content):
        size = float(m.group(1))
        drill = float(m.group(2))
        ring = (size - drill) / 2
        total += 1
        if ring < 0.074:
            violations += 1

    check(f"Via annular ring >= 0.075mm ({total} vias)",
          violations == 0, f"{violations} violations")


def test_gerber_zip():
    """Test 10: gerbers.zip has >= 12 files (gerbers + drill + optional job)."""
    print("\n── Gerber Zip Tests ──")
    zip_path = os.path.join(RELEASE, "gerbers.zip")
    with zipfile.ZipFile(zip_path) as z:
        names = z.namelist()
    check(f"gerbers.zip has >= 12 files", len(names) >= 12,
          f"got {len(names)}: {names}")


def test_u5_pin_alignment():
    """Test 11: Analyze U5 (PAM8403) pin alignment at all rotations.

    Tests all 4 rotations under JLCPCB convention (Y-mirror + CCW rotation).
    C5122557 = narrow SOP-16 (3.9mm body, pad centers at ±2.7mm).
    Reports which rotation aligns with standard SOIC-16 model assumptions.
    Always passes — JLCPCB C5122557 model may differ from standard.
    """
    print("\n── U5 Pin Alignment Analysis ──")
    import math

    # Narrow SOP-16 model pin positions (body center at origin)
    # C5122557: 3.9mm body width, pad centers at ±2.7mm
    PAD_X = 2.7   # narrow body pad center distance from body center
    model_pins = {}
    for i in range(8):
        model_pins[i + 1] = (-PAD_X, -4.445 + i * 1.27)
    for i in range(8):
        model_pins[i + 9] = (PAD_X, 4.445 - i * 1.27)

    # Our gerber pad positions (from pre-rotation 90° + X-mirror)
    gerber_pins = {}
    for i in range(8):
        x, y = -PAD_X, -4.445 + i * 1.27
        rx, ry = -y, x
        gerber_pins[i + 1] = (-rx, ry)
    for i in range(8):
        x, y = PAD_X, 4.445 - i * 1.27
        rx, ry = -y, x
        gerber_pins[i + 9] = (-rx, ry)

    cpl = read_cpl()
    cpl_rot = int(cpl["U5"]["Rotation"])

    for test_rot in [0, 90, 180, 270]:
        rad = math.radians(-test_rot)
        cos_a, sin_a = math.cos(rad), math.sin(rad)
        max_err = 0
        for pin in sorted(model_pins):
            mx, my = model_pins[pin]
            mx = -mx
            rx = mx * cos_a - my * sin_a
            ry = mx * sin_a + my * cos_a
            gx, gy = gerber_pins[pin]
            err = max(abs(rx - gx), abs(ry - gy))
            max_err = max(max_err, err)
        tag = " ← CPL" if test_rot == cpl_rot else ""
        status = "ALIGN" if max_err < 0.01 else f"err={max_err:.1f}mm"
        print(f"    rot={test_rot:3d}°: {status}{tag}")

    check(f"U5 CPL rotation = {cpl_rot}° (4 variants in release_jlcpcb/)",
          True)


def test_sop16_aperture():
    """Test 12: SOP-16 narrow aperture R,0.6x1.55 exists (pre-rotation working)."""
    print("\n── SOP-16 Aperture Test ──")
    gerber_path = os.path.join(RELEASE, "gerbers", "esp32-emu-turbo-B_Cu.gbl")
    with open(gerber_path) as f:
        content = f.read()

    # Look for rotated aperture (0.6 wide, 1.55 tall — narrow SOP-16)
    has_rotated = bool(re.search(r'R,0\.600000X1\.550000', content))
    check("SOP-16 narrow rotated aperture R,0.6x1.55 exists", has_rotated)


def test_kicad_drc():
    """Test 13-15: KiCad DRC — no real violations (edge, hole, silk)."""
    print("\n── KiCad DRC Tests ──")
    kicad_cli = shutil.which("kicad-cli")
    if not kicad_cli:
        print("  SKIP  kicad-cli not found (install KiCad for DRC tests)")
        return

    drc_out = os.path.join(BASE, "hardware", "kicad", "drc-report.json")
    try:
        subprocess.run(
            [kicad_cli, "pcb", "drc",
             "--output", drc_out, "--format", "json",
             "--severity-all", "--units", "mm", "--all-track-errors",
             PCB_FILE],
            capture_output=True, timeout=60,
        )
    except (subprocess.TimeoutExpired, FileNotFoundError):
        print("  SKIP  kicad-cli drc failed to run")
        return

    if not os.path.exists(drc_out):
        print("  SKIP  DRC report not generated")
        return

    with open(drc_out) as f:
        data = json.load(f)

    # Share the parsed report with test_kicad_drc_edge_clearance so the
    # suite runs kicad-cli DRC once, not twice (~1.1 s each).
    global _DRC_REPORT
    _DRC_REPORT = data

    from collections import Counter
    types = Counter()
    for v in data.get("violations", []):
        types[v["type"]] += 1

    # Real violations that should be zero (or within baseline)
    edge = types.get("copper_edge_clearance", 0)
    hole = types.get("hole_to_hole", 0)
    silk_copper = types.get("silk_over_copper", 0)
    silk_overlap = types.get("silk_overlap", 0)
    silk_edge = types.get("silk_edge_clearance", 0)

    # Allow 5 copper_edge_clearance: J1 (USB-C) rear shield pads 13b/14b extend
    # near board edge (connector sits at board edge by design), plus 3 CC1 trace
    # segments routing near bottom edge. JLCPCB footprint C2765186 has rear tabs
    # designed to be at/near the board edge for structural support.
    check("KiCad DRC: copper_edge_clearance <= 5", edge <= 5,
          f"got {edge}")
    # Allow 1 hole_to_hole: FPC via-in-pad GND/+3V3 at 0.5mm pitch (pins 5/6).
    # KiCad default min is ~0.5mm but JLCPCB requires only 0.25mm.
    # Our actual gap is 0.3mm (0.5 - 0.1 - 0.1) which passes JLCPCB.
    check("KiCad DRC: hole_to_hole <= 1", hole <= 1,
          f"got {hole}")
    # silk_over_copper=2: project text "CPJ&CP 2026 v3" clipped by J1 rear
    # shield THT pads 13b/14b solder mask openings (cosmetic, not functional).
    check("KiCad DRC: silk issues <= 2",
          silk_copper <= 2 and silk_overlap == 0 and silk_edge == 0,
          f"silk_over_copper={silk_copper}, silk_overlap={silk_overlap}, "
          f"silk_edge={silk_edge}")

    # Clean up
    os.remove(drc_out)


# Parsed kicad-cli DRC report, produced by test_kicad_drc and reused by
# test_kicad_drc_edge_clearance. The producing run uses --all-track-errors,
# so every count it reports is >= the count of a flagless run: reusing it
# makes the edge-clearance guard at least as strict, never more permissive.
_DRC_REPORT = None

_CACHE = None


def _get_cache():
    """Lazy-load PCB cache (shared across all test functions)."""
    global _CACHE
    if _CACHE is None:
        from pcb_cache import load_cache
        _CACHE = load_cache()
    return _CACHE


def _cached_segments():
    """Load segments from cache with 'w' key (backward compat)."""
    return [{"x1": s["x1"], "y1": s["y1"], "x2": s["x2"], "y2": s["y2"],
             "w": s["width"], "layer": s["layer"], "net": s["net"]}
            for s in _get_cache()["segments"]]


def _cached_vias():
    """Load vias from cache."""
    return _get_cache()["vias"]


def _seg_min_dist(s1, s2):
    """Approximate minimum distance between two parallel segments on same layer.

    For axis-aligned segments sharing an overlap region, computes edge-to-edge gap.
    Returns None if segments aren't parallel/overlapping axis-aligned.
    """
    tol = 0.01
    # Both vertical
    if abs(s1["x1"] - s1["x2"]) < tol and abs(s2["x1"] - s2["x2"]) < tol:
        x1, x2 = s1["x1"], s2["x1"]
        y1a, y1b = min(s1["y1"], s1["y2"]), max(s1["y1"], s1["y2"])
        y2a, y2b = min(s2["y1"], s2["y2"]), max(s2["y1"], s2["y2"])
        overlap = min(y1b, y2b) - max(y1a, y2a)
        if overlap > 0:
            gap = abs(x1 - x2) - (s1["w"] + s2["w"]) / 2
            return gap
    # Both horizontal
    if abs(s1["y1"] - s1["y2"]) < tol and abs(s2["y1"] - s2["y2"]) < tol:
        y1, y2 = s1["y1"], s2["y1"]
        x1a, x1b = min(s1["x1"], s1["x2"]), max(s1["x1"], s1["x2"])
        x2a, x2b = min(s2["x1"], s2["x2"]), max(s2["x1"], s2["x2"])
        overlap = min(x1b, x2b) - max(x1a, x2a)
        if overlap > 0:
            gap = abs(y1 - y2) - (s1["w"] + s2["w"]) / 2
            return gap
    return None


def _point_to_segment_dist(px, py, s):
    """Distance from point (px, py) to the nearest point on segment s.

    s must be a dict with keys x1, y1, x2, y2.
    Works for any segment orientation (not just axis-aligned).
    """
    ax, ay = s["x1"], s["y1"]
    bx, by = s["x2"], s["y2"]
    dx, dy = bx - ax, by - ay
    len_sq = dx * dx + dy * dy
    if len_sq < 1e-12:
        return ((px - ax) ** 2 + (py - ay) ** 2) ** 0.5
    t = ((px - ax) * dx + (py - ay) * dy) / len_sq
    t = max(0.0, min(1.0, t))
    cx = ax + t * dx
    cy = ay + t * dy
    return ((px - cx) ** 2 + (py - cy) ** 2) ** 0.5


def _segment_to_rect_gap(s, px, py, pw, ph):
    """Minimum copper gap between a trace segment and an axis-aligned rectangular pad.

    The trace has half-width s["w"]/2 and the pad is pw x ph centered at (px, py).
    Returns the edge-to-edge gap (negative means overlap).

    Uses segment-to-rectangle minimum distance: finds the closest point on the
    segment to the rectangle, then subtracts half-trace-width.
    """
    import math
    hw, hh = pw / 2.0, ph / 2.0
    # Rectangle bounds
    rx_min, rx_max = px - hw, px + hw
    ry_min, ry_max = py - hh, py + hh

    # Sample points along the segment and find minimum distance to rectangle
    # For exact computation: clamp each segment point to the rectangle
    ax, ay = s["x1"], s["y1"]
    bx, by = s["x2"], s["y2"]

    def _point_to_rect_dist(qx, qy):
        """Distance from point to axis-aligned rectangle."""
        # Clamp point to rectangle
        cx = max(rx_min, min(rx_max, qx))
        cy = max(ry_min, min(ry_max, qy))
        return math.sqrt((qx - cx) ** 2 + (qy - cy) ** 2)

    # Exact: check segment vs each of the 4 rectangle edges
    # But for axis-aligned pads, a simpler approach:
    # Find closest point on segment to the rectangle (analytical)

    # Check all rectangle corners against segment
    min_dist = float("inf")
    for cx, cy in [(rx_min, ry_min), (rx_min, ry_max),
                   (rx_max, ry_min), (rx_max, ry_max)]:
        d = _point_to_segment_dist(cx, cy, s)
        if d < min_dist:
            min_dist = d

    # Check segment endpoints against rectangle
    for qx, qy in [(ax, ay), (bx, by)]:
        d = _point_to_rect_dist(qx, qy)
        if d < min_dist:
            min_dist = d

    # Check segment vs each rectangle edge (4 edges)
    edges = [
        (rx_min, ry_min, rx_max, ry_min),  # bottom
        (rx_max, ry_min, rx_max, ry_max),  # right
        (rx_max, ry_max, rx_min, ry_max),  # top
        (rx_min, ry_max, rx_min, ry_min),  # left
    ]
    for ex1, ey1, ex2, ey2 in edges:
        d = _seg_seg_dist(ax, ay, bx, by, ex1, ey1, ex2, ey2)
        if d < min_dist:
            min_dist = d

    return min_dist - s["w"] / 2.0


def _seg_seg_dist(ax, ay, bx, by, cx, cy, dx, dy):
    """Minimum distance between two line segments AB and CD."""
    import math

    def _pt_seg(px, py, sx, sy, ex, ey):
        vx, vy = ex - sx, ey - sy
        ln2 = vx * vx + vy * vy
        if ln2 < 1e-12:
            return math.sqrt((px - sx) ** 2 + (py - sy) ** 2)
        t = max(0.0, min(1.0, ((px - sx) * vx + (py - sy) * vy) / ln2))
        qx, qy = sx + t * vx, sy + t * vy
        return math.sqrt((px - qx) ** 2 + (py - qy) ** 2)

    # Check if segments intersect
    def _cross(ux, uy, vx, vy):
        return ux * vy - uy * vx

    rx, ry = bx - ax, by - ay
    sx, sy = dx - cx, dy - cy
    denom = _cross(rx, ry, sx, sy)
    qpx, qpy = cx - ax, cy - ay
    if abs(denom) > 1e-12:
        t = _cross(qpx, qpy, sx, sy) / denom
        u = _cross(qpx, qpy, rx, ry) / denom
        if 0 <= t <= 1 and 0 <= u <= 1:
            return 0.0  # segments intersect

    # No intersection — minimum is endpoint-to-segment
    d1 = _pt_seg(ax, ay, cx, cy, dx, dy)
    d2 = _pt_seg(bx, by, cx, cy, dx, dy)
    d3 = _pt_seg(cx, cy, ax, ay, bx, by)
    d4 = _pt_seg(dx, dy, ax, ay, bx, by)
    return min(d1, d2, d3, d4)


def test_trace_spacing():
    """Test 16: Trace spacing regression guard — no new parallel trace violations.

    Baseline: some trace proximity violations are inherent to the dense design
    (USB-C area, button pull-up arrays, ESP32 pin fan-out).
    This test guards against REGRESSIONS — the count should not increase.
    """
    print("\n── Trace Spacing Tests ──")
    segs = _cached_segments()

    # Group by layer for efficient comparison
    by_layer = {}
    for s in segs:
        by_layer.setdefault(s["layer"], []).append(s)

    violations = []
    min_gap_threshold = 0.10  # JLCPCB DFM Danger threshold

    for layer, layer_segs in by_layer.items():
        if "Cu" not in layer:
            continue
        n = len(layer_segs)
        for i in range(n):
            for j in range(i + 1, n):
                s1, s2 = layer_segs[i], layer_segs[j]
                if s1["net"] == s2["net"]:
                    continue  # same net, no spacing required
                gap = _seg_min_dist(s1, s2)
                if gap is not None and gap < min_gap_threshold:
                    violations.append(
                        f"{layer}: gap={gap:.3f}mm at "
                        f"({s1['x1']},{s1['y1']})-({s1['x2']},{s1['y2']}) vs "
                        f"({s2['x1']},{s2['y1']})-({s2['x2']},{s2['y2']})"
                    )

    # Baseline reduced to 0: all trace-trace spacing violations resolved.
    # History: 27 → 12 (layer-swap) → 0 (routing cleanup)
    BASELINE = 0
    check(f"Trace spacing violations <= baseline {BASELINE} ({len(violations)} found)",
          len(violations) <= BASELINE,
          f"{len(violations)} violations (baseline {BASELINE}): {violations[:3]}")


def test_via_to_via_spacing():
    """Test 17: No via holes closer than 0.25mm (hole-to-hole edge gap)."""
    print("\n── Via-to-Via Spacing Tests ──")
    vias = _cached_vias()

    min_hole_gap = 0.25  # JLCPCB minimum hole-to-hole clearance
    violations = []

    for i in range(len(vias)):
        for j in range(i + 1, len(vias)):
            v1, v2 = vias[i], vias[j]
            dist = ((v1["x"] - v2["x"])**2 + (v1["y"] - v2["y"])**2)**0.5
            edge_gap = dist - (v1["drill"] + v2["drill"]) / 2
            if edge_gap < min_hole_gap:
                # Exclude same-net via-in-pad on ESP32 castellated pads
                # (ESP32 center at 80, 31.12; module 18x25.5mm)
                esp_cx, esp_cy = 80.0, 31.12
                on_esp = (abs(v1["x"] - esp_cx) < 10 and abs(v1["y"] - esp_cy) < 14
                          and abs(v2["x"] - esp_cx) < 10 and abs(v2["y"] - esp_cy) < 14)
                if on_esp and v1["net"] == v2["net"]:
                    continue
                violations.append(
                    f"gap={edge_gap:.3f}mm: ({v1['x']},{v1['y']}) vs "
                    f"({v2['x']},{v2['y']})"
                )

    check(f"Via hole-to-hole gap >= 0.25mm ({len(vias)} vias)",
          len(violations) == 0,
          f"{len(violations)} violations: {violations[:5]}")


def test_display_stagger_vs_esp32():
    """Test 18: Display bottom-pin stagger traces at ESP32 pin midpoints.

    ESP32 left-side pins at y = 22.24 + n*1.27 (n=0..13).
    Bottom-pin stagger traces (y=28..32 region) must use midpoints
    to avoid trace spacing violations with ESP32 side-pin signal traces.

    Excludes button routing traces, which legitimately end at ESP32 pad X
    positions (x=71.25 right side, x=88.75 left side).  Those traces are
    short point-to-point segments terminating at the ESP32 pad — they are
    not display bus stagger traces and cannot be at midpoints.
    """
    print("\n── Display Stagger vs ESP32 Pin Tests ──")
    segs = _cached_segments()

    # ESP32 left-side pin Y positions
    esp_pin_ys = [22.24 + n * 1.27 for n in range(14)]

    # ESP32 right-side pin X coordinates (board level, after B.Cu mirror)
    # Button traces that END at an ESP32 pad x are excluded from stagger check.
    # Right-side ESP32 pads are at x=71.25; left-side at x=88.75.
    ESP32_PAD_XS = {71.25, 88.75}

    # Find F.Cu horizontal traces in the STAGGER REGION (y=28..32)
    # These are display bottom-pin stagger traces that must use midpoints.
    # Exclude:
    #   - short stubs < 5mm (direct pad connections)
    #   - button routing traces that end exactly at an ESP32 pad column
    stagger_segs = []
    for s in segs:
        if s["layer"] != "F.Cu":
            continue
        if abs(s["y1"] - s["y2"]) > 0.01:
            continue  # not horizontal
        length = abs(s["x1"] - s["x2"])
        if length < 5.0:
            continue  # short stub
        y = s["y1"]
        # Critical stagger region: y=28..32 where bottom ESP32 pins are
        if not (28 < y < 32 and min(s["x1"], s["x2"]) < 75):
            continue
        # Exclude button routing traces near ESP32 pad columns.
        # Button stagger traces end at near_epx (epx ± 2-3mm), not exactly at epx.
        # Check both x_min and x_max within 3.5mm of any ESP32 pad X column.
        x_min = min(s["x1"], s["x2"])
        x_max = max(s["x1"], s["x2"])
        if any(abs(x_max - ex) < 3.5 or abs(x_min - ex) < 3.5
               for ex in ESP32_PAD_XS):
            continue  # button stagger trace, not a display stagger
        stagger_segs.append(s)

    violations = []
    min_gap = 0.15  # minimum y-distance from ESP32 pin center

    for s in stagger_segs:
        y = s["y1"]
        for py in esp_pin_ys:
            if abs(y - py) < min_gap:
                violations.append(
                    f"stagger y={y:.3f} len={abs(s['x1']-s['x2']):.1f}mm "
                    f"collides with ESP32 pin y={py:.2f} "
                    f"(gap={abs(y - py):.3f}mm)"
                )

    check(f"Bottom stagger traces at midpoints ({len(stagger_segs)} traces)",
          len(violations) == 0,
          f"{len(violations)} violations: {violations[:5]}")


def test_esop8_ep_pad_clearance():
    """Test 19: ESOP-8 (IP5306) EP pad has >= 0.10mm gap to corner signal pads.

    The EP (exposed pad) is 3.4 x 2.8mm (height reduced from 3.4mm).
    Corner signal pins 1, 4, 5, 8 are at y = ±1.905mm, half-height = 0.3mm.
    EP edge at ±1.4mm.  Gap = 1.605 - 1.4 = 0.205mm > 0.10mm danger threshold.
    Guard against regression that restores the original 3.4mm height.
    """
    print("\n── ESOP-8 EP Pad Clearance Tests ──")
    with open(PCB_FILE) as f:
        content = f.read()

    # Find the ESOP-8 footprint block and locate the EP pad size
    # The EP pad at center (0,0) has name "EP"
    ep_pattern = re.compile(
        r'\(pad "EP" smd rect \(at ([-\d.]+) ([-\d.]+)\)'
        r' \(size ([\d.]+) ([\d.]+)\)',
    )
    found = False
    violations = []
    for m in ep_pattern.finditer(content):
        ex, ey = float(m.group(1)), float(m.group(2))
        ew, eh = float(m.group(3)), float(m.group(4))
        found = True
        # EP edges (in footprint-local coords, before board transform)
        ep_half_h = eh / 2
        # Corner signal pin edge at ±1.605mm (y=±1.905, half-height=0.3)
        pin_edge = 1.605
        gap = pin_edge - ep_half_h
        if gap < 0.10:
            violations.append(
                f"EP size {ew}x{eh}mm: gap={gap:.3f}mm < 0.10mm danger threshold"
            )

    check("ESOP-8 EP pad found", found)
    check(
        "ESOP-8 EP pad height <= 3.2mm (gap >= 0.10mm to corner pins)",
        len(violations) == 0,
        f"{len(violations)} violation(s): {violations[:2]}",
    )


def test_msk12c02_unique_sh_pads():
    """Test 20: MSK12C02 (SW16) shell pads have unique names 4a-4d.

    JLCPCB's DFM checker groups same-named pads and can report 0mm spacing
    between them.  All four shell/mounting pads must have distinct names.
    """
    print("\n── MSK12C02 Unique Shell Pad Names ──")
    with open(PCB_FILE) as f:
        content = f.read()

    # Count pads named exactly "SH" (old shared shell name) — should be 0
    sh_plain_pattern = re.compile(r'\(pad "SH" smd rect')
    sh_plain_count = len(sh_plain_pattern.findall(content))

    # Count uniquely-named 4a-4d pads (JLCPCB-matching shell pad names)
    sh_unique_pattern = re.compile(r'\(pad "4[a-d]" smd rect')
    sh_unique_count = len(sh_unique_pattern.findall(content))

    check(
        "No plain 'SH' pads remain (all renamed to 4a-4d)",
        sh_plain_count == 0,
        f"found {sh_plain_count} plain 'SH' pads (should be 0)",
    )
    check(
        "Exactly 4 unique 4a-4d pads present (one MSK12C02 with 4 shell pads)",
        sh_unique_count == 4,
        f"found {sh_unique_count} 4a-4d pads (expected 4)",
    )


def test_btn_r_routed():
    """Test 21: BTN_R (SW12 shoulder-right button) has a trace to ESP32 GPIO36.

    SW12 is at enc(65, 32) = (145, 5.5) on B.Cu.  Routing uses a B.Cu stub
    down to a channel row, F.Cu across the board, then B.Cu up to GPIO19
    (ESP32 right-side pad at y~37.48).  Verify that at least one B.Cu segment
    originates near SW12 pad 3 (143.15, 8.5).
    """
    print("\n── BTN_R (SW12) Routing Tests ──")
    segs = _cached_segments()

    # SW12 signal pad 3 is at (143.15, 8.5) in board coordinates.
    # Expect a B.Cu segment starting or ending very near this position.
    target_x, target_y = 143.15, 8.5
    tolerance = 0.1

    found_stub = any(
        s["layer"] == "B.Cu"
        and (
            (abs(s["x1"] - target_x) < tolerance and abs(s["y1"] - target_y) < tolerance)
            or (abs(s["x2"] - target_x) < tolerance and abs(s["y2"] - target_y) < tolerance)
        )
        for s in segs
    )

    check(
        "BTN_R B.Cu stub found near SW12 pad 3 (143.15, 8.5)",
        found_stub,
        "no B.Cu segment near SW12 signal pad — BTN_R may be unrouted",
    )

    # Also verify a long F.Cu horizontal segment exists for BTN_R cross-board run.
    # BTN_R routes to GPIO19 at x=88.75, approach at x=92.05,
    # so F.Cu from SW12 pad (x=146.85) to approach_r (x=92.05): length ~54.8mm.
    # chan_y_r was moved from 66.0 to 65.0 to avoid SD_MOSI overlap.
    long_fcu = any(
        s["layer"] == "F.Cu"
        and abs(s["y1"] - s["y2"]) < 0.01
        and 63.0 < s["y1"] < 70.0
        and abs(s["x1"] - s["x2"]) > 40
        and max(s["x1"], s["x2"]) > 140   # must reach near SW12 (x=146.85)
        for s in segs
    )
    check(
        "BTN_R long F.Cu cross-board segment found near y=65mm",
        long_fcu,
        "no long F.Cu segment at y~65mm reaching x>140 — BTN_R channel route may be missing",
    )


def test_kicad_drc_edge_clearance():
    """Test 22: KiCad DRC copper-to-edge clearance — zero violations.

    Guards against traces or vias placed too close to the board outline,
    the FPC slot edge, or any other Edge.Cuts element.
    Passes only when kicad-cli is available.
    """
    print("\n── KiCad DRC Edge Clearance Guard ──")
    data = _DRC_REPORT
    if data is None:
        # test_kicad_drc did not run (or skipped) — run DRC ourselves.
        kicad_cli = shutil.which("kicad-cli")
        if not kicad_cli:
            print("  SKIP  kicad-cli not found")
            return

        drc_out = os.path.join(BASE, "hardware", "kicad",
                               "drc-edge-guard.json")
        try:
            subprocess.run(
                [kicad_cli, "pcb", "drc",
                 "--output", drc_out, "--format", "json",
                 "--severity-all", "--units", "mm",
                 PCB_FILE],
                capture_output=True, timeout=60,
            )
        except (subprocess.TimeoutExpired, FileNotFoundError):
            print("  SKIP  kicad-cli drc failed")
            return

        if not os.path.exists(drc_out):
            print("  SKIP  DRC report not generated")
            return

        with open(drc_out) as f:
            data = json.load(f)
        os.remove(drc_out)

    from collections import Counter
    types = Counter(v["type"] for v in data.get("violations", []))
    edge = types.get("copper_edge_clearance", 0)
    hole = types.get("hole_to_hole", 0)

    # Allow 5: J1 USB-C rear shield pads + CC1 traces near board bottom edge
    check("KiCad DRC: copper_edge_clearance <= 5 (regression guard)", edge <= 5,
          f"got {edge} violations")
    # Allow 1: FPC via-in-pad GND/+3V3 pins 5/6 at 0.5mm pitch
    # (KiCad default 0.5mm rule; JLCPCB needs only 0.25mm, actual gap is 0.3mm)
    check("KiCad DRC: hole_to_hole <= 1 (regression guard)", hole <= 1,
          f"got {hole} violations")


def test_sw8_slot_clearance():
    """Test 23: SW8 (BTN_Y) pad 1 clears FPC slot edge by >= 0.5mm.

    SW8 pad 1 (signal pad) is closest to the FPC slot cutout (right edge
    at x=128.5mm).  Pad center must be at x >= 129.0mm so the copper edge
    (pad_center - pad_half_width = x - 0.6) is at least 0.5mm from slot edge.
    Min center x = 128.5 + 0.5 + 0.6 = 129.6mm.
    Guards against accidental leftward drift of SW8 position.
    """
    print("\n── SW8 Slot Clearance Test ──")
    cpl = read_cpl()
    sw8_x = float(cpl["SW8"]["Mid X"].replace("mm", ""))
    # SW8 pad 1 is 3mm left of center
    pad1_x = sw8_x - 3.0
    slot_edge_x = 128.5
    pad_half_w = 0.6
    gap = pad1_x - pad_half_w - slot_edge_x
    check(
        f"SW8 pad1 clears FPC slot by >= 0.5mm (gap={gap:.2f}mm)",
        gap >= 0.5,
        f"SW8 center={sw8_x:.2f}mm, pad1={pad1_x:.2f}mm, slot={slot_edge_x}mm, gap={gap:.3f}mm",
    )


def test_btn_r_edge_clearance():
    """Test 24: BTN_R F.Cu channel is at least 0.5mm from board bottom edge.

    BTN_R uses an F.Cu horizontal segment to cross the board.  The bottom
    board edge is at y=75.0mm.  The copper must be at most y=74.5mm
    (0.5mm clearance from edge).
    Guards against chan_y_r drifting to 75.0 (board edge).
    """
    print("\n── BTN_R Edge Clearance Test ──")
    segs = _cached_segments()

    # BTN_R net=38; find its longest F.Cu horizontal segment
    net_btn_r = 38
    board_bottom = 75.0
    min_clearance = 0.5
    violations = []
    for s in segs:
        if s["net"] != net_btn_r or s["layer"] != "F.Cu":
            continue
        if abs(s["y1"] - s["y2"]) > 0.01:
            continue  # not horizontal
        y = s["y1"]
        clearance = board_bottom - y
        if clearance < min_clearance:
            violations.append(
                f"BTN_R F.Cu at y={y:.3f}mm: clearance to board edge = {clearance:.3f}mm < {min_clearance}mm"
            )

    check(
        "BTN_R F.Cu channel >= 0.5mm from board bottom edge (y <= 74.5mm)",
        len(violations) == 0,
        f"{len(violations)} violations: {violations[:3]}",
    )


def test_sd_gnd_via_clearance():
    """Test 25: SD routing B.Cu post_slot traces clear of SW5/SW7 GND vias.

    SW5 (BTN_A) and SW7 (BTN_X) GND vias land at x=143.5 (pads at x=145 offset
    1.5mm left).  SD routing post_slot B.Cu verticals at x=141,145,146,148 must
    all be >= 0.2mm (KiCad netclass clearance) from via ring at 143.5±0.45mm.

    Forbidden zone: x in [143.05, 143.95] (via ring ±0.45mm).
    Clearance requirement: trace half-width (0.1mm) + via radius (0.45mm) +
    clearance (0.2mm) = 0.75mm from via center.  So trace centerline must be
    outside [142.75, 144.25].

    Guards against post_slot_map assignments at x=143 or x=144 which caused
    0.05mm clearance violations in KiCad DRC.
    """
    print("\n── SD Post-Slot vs GND Via Clearance ──")
    segs = _cached_segments()

    # GND vias from SW5/SW7 routing are at x=143.5 (net=GND).
    # SD post_slot B.Cu verticals are net 20-23 (SD_MOSI,MISO,CLK,CS).
    # Any SD B.Cu segment with centerline in [142.75, 144.25] is a violation.
    FORBIDDEN_LO = 142.75
    FORBIDDEN_HI = 144.25
    SD_NETS = {20, 21, 22, 23}  # SD_MOSI, SD_MISO, SD_CLK, SD_CS

    violations = []
    for s in segs:
        if s["net"] not in SD_NETS or s["layer"] != "B.Cu":
            continue
        # Vertical segment: x1==x2
        if abs(s["x1"] - s["x2"]) > 0.01:
            continue
        x = s["x1"]
        if FORBIDDEN_LO < x < FORBIDDEN_HI:
            violations.append(
                f"SD net={s['net']} B.Cu vert at x={x:.3f} in forbidden zone "
                f"[{FORBIDDEN_LO},{FORBIDDEN_HI}]"
            )

    check(
        "SD post_slot B.Cu verticals avoid x=[142.75,144.25] (GND via clearance zone)",
        len(violations) == 0,
        f"{len(violations)} violations: {violations[:3]}",
    )


def test_bat_plus_via_vbus_clearance():
    """Test 26: BAT+ via at L1[1] clears VBUS F.Cu trace at x=111.0.

    The L1 boost inductor pin 1 BAT+ via is at (bat_via_x, bat_via_y).
    The VBUS F.Cu trace runs vertically at x=111.0 with width=0.5mm.
    Required clearance: 0.2mm (netclass default).

    Forbidden: via must not be within 0.75mm of x=111.0 (via_radius +
    trace_half + clearance = 0.45+0.25+0.2-0.25 = 0.65mm from trace center).
    More precisely: via_center_x - via_radius >= 111.25 + 0.2 → x >= 111.9mm.
    Guards against BAT+ via drifting back to (111.7, 49.5) which gives 0.0mm gap.
    """
    print("\n── BAT+ Via / VBUS Trace Clearance ──")
    with open(PCB_FILE) as f:
        content = f.read()

    import re as _re
    # Find BAT+ via (net=5) near y=49.5
    vias_raw = _re.findall(
        r'\(via\s+\(at\s+([-\d.]+)\s+([-\d.]+)\).*?\(size\s+([-\d.]+)\).*?\(drill\s+([-\d.]+)\).*?\(net\s+(\d+)\)',
        content, _re.DOTALL
    )
    # Find VBUS F.Cu vertical near x=111 (any segment with both endpoints at x≈111)
    vbus_net = 2
    vbus_trace_x = 111.0
    vbus_trace_hw = 0.25  # half-width of 0.5mm VBUS trace
    required_clearance = 0.2

    bat_net = 5
    violations = []
    for v in vias_raw:
        vx, vy, vsize, vdrill, vnet = float(v[0]), float(v[1]), float(v[2]), float(v[3]), int(v[4])
        if vnet != bat_net:
            continue
        # Only check the L1[1] BAT+ via — it's near x=111-113, y=48-51.
        # Other BAT+ vias (e.g. for JST connector, IP5306 BAT pins) are far from x=111.
        if not (110.0 < vx < 115.0 and 47.0 < vy < 52.0):
            continue
        # This via must be RIGHT of VBUS trace: via_left >= vbus_right + clearance.
        via_radius = float(vsize) / 2
        # VBUS trace right edge = vbus_trace_x + vbus_trace_hw = 111.25
        vbus_right = vbus_trace_x + vbus_trace_hw
        via_left = vx - via_radius
        gap = via_left - vbus_right
        if gap < required_clearance:
            violations.append(
                f"BAT+ L1 via at ({vx:.3f},{vy:.3f}) r={via_radius:.3f}: "
                f"gap to VBUS right edge={gap:.3f}mm < {required_clearance}mm"
            )

    check(
        "BAT+ L1 via clears VBUS F.Cu trace by >= 0.2mm",
        len(violations) == 0,
        f"{len(violations)} violations: {violations[:3]}",
    )


def test_mounting_holes_npth():
    """Test 27: All MountingHole footprints use np_thru_hole (NPTH).

    DFM: NPTH mounting holes have no copper annular ring, eliminating
    THT-to-SMD and pad spacing DANGER violations with nearby components.
    Guards against regression that restores PTH mounting holes.
    """
    print("\n── Mounting Holes NPTH Test ──")
    with open(PCB_FILE) as f:
        content = f.read()

    # Find all MountingHole footprint blocks and check pad type
    mh_blocks = re.findall(
        r'\(footprint "MountingHole[^"]*".*?\n(?:.*?\n)*?.*?\(pad[^)]*\)',
        content,
    )
    pth_count = 0
    npth_count = 0
    for block in mh_blocks:
        if 'np_thru_hole' in block:
            npth_count += 1
        elif 'thru_hole' in block:
            pth_count += 1

    # Also check with a simpler pattern for reliability
    npth_pattern = re.compile(
        r'\(footprint "MountingHole.*?'
        r'\(pad "" np_thru_hole',
        re.DOTALL,
    )
    pth_pattern = re.compile(
        r'\(footprint "MountingHole.*?'
        r'\(pad "" thru_hole',
        re.DOTALL,
    )
    npth_simple = len(npth_pattern.findall(content))
    pth_simple = len(pth_pattern.findall(content))

    check(
        "All MountingHole pads are np_thru_hole (NPTH)",
        pth_simple == 0 and npth_simple > 0,
        f"PTH={pth_simple}, NPTH={npth_simple} (expected 0 PTH, >0 NPTH)",
    )


def test_lx_bat_trace_spacing():
    """Test 28: LX and BAT+ B.Cu vertical columns have edge gap >= 0.25mm.

    LX (net=46) vertical at lx_col_x and BAT+ (net=5) vertical at bat_col_x
    must have sufficient spacing. Guards against LX column drifting right
    toward BAT+ column.
    """
    print("\n── LX vs BAT+ Trace Spacing Test ──")
    segs = _cached_segments()

    n_lx = 46   # NET_ID["LX"]
    n_bat = 5   # NET_ID["BAT+"]
    min_edge_gap = 0.25

    # Find B.Cu vertical segments for LX and BAT+
    lx_verts = [s for s in segs if s["net"] == n_lx and s["layer"] == "B.Cu"
                and abs(s["x1"] - s["x2"]) < 0.01]
    bat_verts = [s for s in segs if s["net"] == n_bat and s["layer"] == "B.Cu"
                 and abs(s["x1"] - s["x2"]) < 0.01]

    violations = []
    for lx in lx_verts:
        for bat in bat_verts:
            gap = _seg_min_dist(lx, bat)
            if gap is not None and gap < min_edge_gap:
                violations.append(
                    f"LX@x={lx['x1']:.3f} vs BAT+@x={bat['x1']:.3f}: "
                    f"edge gap={gap:.3f}mm < {min_edge_gap}mm"
                )

    check(
        f"LX vs BAT+ B.Cu vertical edge gap >= {min_edge_gap}mm",
        len(violations) == 0,
        f"{len(violations)} violations: {violations[:3]}",
    )


def test_lx_switch_node_width():
    """R27-MED-1 guard: the whole LX switch node runs at W_PWR_HIGH.

    Not a restatement of the generator's output. The expected width is
    IMPORTED from routing.W_PWR_HIGH — the constant that defines what a
    >=2.1A / 1oz / 10C-rise power trace is on this board — so:

      * routing LX at W_PWR (0.60) again fails, which is the regression
        this guards. Five of LX's seven segments sat at 0.60 until
        2026-07-26, justified by a comment claiming "~1.4A capacity ...
        adequate for pulsed LX" that contradicted W_PWR_HIGH three lines
        above it;
      * changing W_PWR_HIGH moves the requirement with it, instead of
        pinning a number that then has to be maintained in two places.

    verify_net_class_widths cannot cover this: its Power High minimum is
    0.50mm, a JLCPCB manufacturing floor rather than a thermal budget, so
    0.60 cleared it and nothing compared the copper to the design's intent.
    """
    print("\n── LX Switch-Node Width Test ──")
    # Import the constant rather than restate it. Reached via the repo root so
    # this works both as `python3 scripts/verify_dfm_v2.py` and as a module.
    import importlib
    _root = os.path.dirname(os.path.dirname(os.path.abspath(__file__)))
    if _root not in sys.path:
        sys.path.insert(0, _root)
    routing = importlib.import_module("scripts.generate_pcb.routing")
    required = routing.W_PWR_HIGH

    segs = _cached_segments()
    n_lx = 46   # NET_ID["LX"]
    lx = [s for s in segs if s["net"] == n_lx]

    check("LX has routed segments", len(lx) > 0, "no LX copper found")

    narrow = [s for s in lx if s["w"] < required - 1e-6]
    total = sum(math.dist((s["x1"], s["y1"]), (s["x2"], s["y2"])) for s in lx)
    thin = sum(math.dist((s["x1"], s["y1"]), (s["x2"], s["y2"])) for s in narrow)
    check(
        f"LX entirely at W_PWR_HIGH ({required}mm) — {total:.1f}mm of copper",
        not narrow,
        f"{len(narrow)} segment(s), {thin:.2f}mm below {required}mm: "
        + ", ".join(f"w={s['w']:.2f}@({s['x1']:.2f},{s['y1']:.2f})"
                    for s in narrow[:3]),
    )


def test_button_vx_spacing():
    """Test 29: Button B.Cu vertical columns have edge gap >= 0.15mm.

    All BTN_* (net 27-39) B.Cu vertical segments must maintain minimum
    spacing between different-net columns. Guards against button vx
    assignments that are too close.
    """
    print("\n── Button B.Cu Column Spacing Test ──")
    segs = _cached_segments()

    btn_nets = set(range(27, 40))  # BTN_UP(27) through BTN_MENU(39)
    min_edge_gap = 0.15

    btn_verts = [s for s in segs if s["net"] in btn_nets and s["layer"] == "B.Cu"
                 and abs(s["x1"] - s["x2"]) < 0.01]

    violations = []
    for i in range(len(btn_verts)):
        for j in range(i + 1, len(btn_verts)):
            s1, s2 = btn_verts[i], btn_verts[j]
            if s1["net"] == s2["net"]:
                continue
            gap = _seg_min_dist(s1, s2)
            if gap is not None and gap < min_edge_gap - 0.005:  # 5µm tolerance for FP
                violations.append(
                    f"net{s1['net']}@x={s1['x1']:.3f} vs net{s2['net']}@x={s2['x1']:.3f}: "
                    f"gap={gap:.3f}mm"
                )

    check(
        f"Button B.Cu vertical edge gap >= {min_edge_gap}mm ({len(btn_verts)} segments)",
        len(violations) == 0,
        f"{len(violations)} violations: {violations[:5]}",
    )


def test_gnd_lcd_d7_spacing():
    """Test 30: GND power trace vs LCD_D7 B.Cu gap >= 0.15mm.

    ESP32 GND thermal pad (net=1, w=0.5mm) B.Cu vertical must not approach
    LCD_D7 (net=13, w=0.2mm) B.Cu vertical. Guards against GND trace
    drifting back to x=81.5 (overlapping LCD_D7 at x=81.905).
    """
    print("\n── GND vs LCD_D7 Spacing Test ──")
    segs = _cached_segments()

    n_gnd = 1   # NET_ID["GND"]
    n_lcd_d7 = 13  # NET_ID["LCD_D7"]
    min_edge_gap = 0.15

    # GND power B.Cu verticals near ESP32 (x in 78..84, y in 28..35)
    gnd_verts = [s for s in segs if s["net"] == n_gnd and s["layer"] == "B.Cu"
                 and abs(s["x1"] - s["x2"]) < 0.01 and s["w"] >= 0.4
                 and 78 < s["x1"] < 84 and min(s["y1"], s["y2"]) < 35]
    lcd_d7_verts = [s for s in segs if s["net"] == n_lcd_d7 and s["layer"] == "B.Cu"
                    and abs(s["x1"] - s["x2"]) < 0.01]

    violations = []
    for g in gnd_verts:
        for l in lcd_d7_verts:
            gap = _seg_min_dist(g, l)
            if gap is not None and gap < min_edge_gap:
                violations.append(
                    f"GND@x={g['x1']:.3f} vs LCD_D7@x={l['x1']:.3f}: "
                    f"gap={gap:.3f}mm"
                )

    check(
        f"GND power vs LCD_D7 B.Cu edge gap >= {min_edge_gap}mm",
        len(violations) == 0,
        f"{len(violations)} violations: {violations[:3]}",
    )


def test_lcd_sd_approach_spacing():
    """Test 31: LCD approach columns vs SD traces edge gap >= 0.15mm.

    LCD B.Cu vertical approach columns (x in 134..141) must not overlap
    SD card routing B.Cu verticals (net 20-23). Guards against approach
    pitch or SD post_slot column being too close.
    """
    print("\n── LCD Approach vs SD Trace Spacing Test ──")
    segs = _cached_segments()

    lcd_nets = set(range(6, 18))  # LCD_D0(6)..LCD_WR(17)
    sd_nets = {20, 21, 22, 23}   # SD_MOSI, SD_MISO, SD_CLK, SD_CS
    min_edge_gap = 0.15

    # LCD B.Cu verticals in approach column range
    lcd_verts = [s for s in segs if s["net"] in lcd_nets and s["layer"] == "B.Cu"
                 and abs(s["x1"] - s["x2"]) < 0.01 and 133 < s["x1"] < 142]
    # SD B.Cu verticals in same x range
    sd_verts = [s for s in segs if s["net"] in sd_nets and s["layer"] == "B.Cu"
                and abs(s["x1"] - s["x2"]) < 0.01 and 133 < s["x1"] < 148]

    violations = []
    for lcd in lcd_verts:
        for sd in sd_verts:
            gap = _seg_min_dist(lcd, sd)
            if gap is not None and gap < min_edge_gap:
                violations.append(
                    f"LCD net{lcd['net']}@x={lcd['x1']:.3f} vs "
                    f"SD net{sd['net']}@x={sd['x1']:.3f}: gap={gap:.3f}mm"
                )

    check(
        f"LCD approach vs SD B.Cu edge gap >= {min_edge_gap}mm",
        len(violations) == 0,
        f"{len(violations)} violations: {violations[:5]}",
    )


def test_via_pad_spacing():
    """Test 32: All different-net via pairs have pad edge gap >= 0.15mm.

    Guards against via placement that creates overlapping pads on different
    nets. Excludes same-net pairs and vias within ESP32 module area.
    """
    print("\n── Via Pad Spacing Test ──")
    vias = _cached_vias()

    min_pad_gap = 0.15
    violations = []

    for i in range(len(vias)):
        for j in range(i + 1, len(vias)):
            v1, v2 = vias[i], vias[j]
            if v1["net"] == v2["net"]:
                continue
            dist = ((v1["x"] - v2["x"])**2 + (v1["y"] - v2["y"])**2)**0.5
            pad_gap = dist - (v1["size"] + v2["size"]) / 2
            if pad_gap < min_pad_gap:
                # Exclude ESP32 area (already handled by via_to_via_spacing)
                esp_cx, esp_cy = 80.0, 31.12
                on_esp = (abs(v1["x"] - esp_cx) < 10 and abs(v1["y"] - esp_cy) < 14
                          and abs(v2["x"] - esp_cx) < 10 and abs(v2["y"] - esp_cy) < 14)
                if on_esp:
                    continue
                # Exclude FPC J4 via-in-pad area (0.5mm pitch makes via-via
                # pad overlap inherent; hole-to-hole spacing is the real guard)
                fpc_x = 133.15
                on_fpc = (abs(v1["x"] - fpc_x) < 1.0 and 27.0 < v1["y"] < 34.0
                          and abs(v2["x"] - fpc_x) < 1.0 and 27.0 < v2["y"] < 34.0)
                if on_fpc:
                    continue
                violations.append(
                    f"net{v1['net']}@({v1['x']:.3f},{v1['y']:.3f}) vs "
                    f"net{v2['net']}@({v2['x']:.3f},{v2['y']:.3f}): "
                    f"pad gap={pad_gap:.3f}mm"
                )

    check(
        f"Via pad edge gap >= {min_pad_gap}mm ({len(vias)} vias)",
        len(violations) == 0,
        f"{len(violations)} violations: {violations[:5]}",
    )


def test_usb_cap_trace_spacing():
    """Test 40: USB D+/D- B.Cu traces maintain >= 0.10mm from GND cap traces.

    Guards against JLCPCB DANGER: B.Cu trace spacing in USB area (x=88-93).
    """
    print("\n── USB Cap Trace Spacing Test ──")
    segs = _cached_segments()

    # B.Cu segments in USB area
    usb_segs = [s for s in segs
                if s["layer"] == "B.Cu" and 88 <= s["x1"] <= 93 and 88 <= s["x2"] <= 93
                and 55 <= s["y1"] <= 75 and 55 <= s["y2"] <= 75]

    violations = []
    for i in range(len(usb_segs)):
        for j in range(i + 1, len(usb_segs)):
            s1, s2 = usb_segs[i], usb_segs[j]
            if s1["net"] == s2["net"]:
                continue
            gap = _seg_min_dist(s1, s2)
            if gap is not None and gap < 0.10:
                violations.append(
                    f"gap={gap:.3f}mm: ({s1['x1']},{s1['y1']})-({s1['x2']},{s1['y2']}) w={s1['w']} "
                    f"vs ({s2['x1']},{s2['y1']})-({s2['x2']},{s2['y2']}) w={s2['w']}"
                )

    check("USB B.Cu trace-to-cap spacing >= 0.10mm",
          len(violations) == 0,
          f"{len(violations)} violations: {violations[:3]}")


def test_usb_data_routed():
    """Test: USB D+/D- data lines routed from J1 (USB-C) to ESP32 GPIO19/20.

    Ensures firmware upload and debug via USB-C work. Verifies:
    1. USB_D+ (net 40) has traces connecting J1 pad 6 to U1 pin 14 (GPIO20)
    2. USB_D- (net 41) has traces connecting J1 pad 7 to U1 pin 13 (GPIO19)
    3. No shared GPIO19/20 with button or joystick nets
    4. BTN_R uses GPIO3 (pin 38), NOT GPIO19
    """
    print("\n── USB Data Line Routing Tests ──")
    segs = _cached_segments()
    vias = _cached_vias()

    sys.path.insert(0, os.path.join(BASE, "scripts"))
    from generate_pcb.primitives import NET_ID

    n_dp = NET_ID["USB_D+"]  # net 40
    n_dm = NET_ID["USB_D-"]  # net 41
    n_btn_r = NET_ID["BTN_R"]  # net 38

    # 1. USB_D+ traces exist (from J1 to ESP32)
    dp_segs = [s for s in segs if s["net"] == n_dp]
    check("USB_D+ (net 40) has routed traces",
          len(dp_segs) >= 3,
          f"only {len(dp_segs)} segments for USB_D+ — need J1→ESP32 route")

    # 2. USB_D- traces exist (from J1 to ESP32)
    dm_segs = [s for s in segs if s["net"] == n_dm]
    check("USB_D- (net 41) has routed traces",
          len(dm_segs) >= 3,
          f"only {len(dm_segs)} segments for USB_D- — need J1→ESP32 route")

    # 3. USB_D+ has vias (layer transitions J1→ESP32)
    dp_vias = [v for v in vias if v.get("net") == n_dp]
    check("USB_D+ has via transitions (B.Cu ↔ F.Cu)",
          len(dp_vias) >= 2,
          f"only {len(dp_vias)} vias for USB_D+ — need B.Cu/F.Cu hops")

    # 4. USB_D- has vias
    dm_vias = [v for v in vias if v.get("net") == n_dm]
    check("USB_D- has via transitions (B.Cu ↔ F.Cu)",
          len(dm_vias) >= 2,
          f"only {len(dm_vias)} vias for USB_D- — need B.Cu/F.Cu hops")

    # 5. BTN_R does NOT share GPIO19 (no net38 traces near GPIO19 pad position)
    #    GPIO19 is at ESP32 pin 13 (left column after B.Cu mirror, x≈88.75, y≈37.48)
    btn_r_at_gpio19 = any(
        s["net"] == n_btn_r
        and 87 < s["x1"] < 90 and 36 < s["y1"] < 39
        for s in segs
    ) or any(
        s["net"] == n_btn_r
        and 87 < s["x2"] < 90 and 36 < s["y2"] < 39
        for s in segs
    )
    check("BTN_R does NOT route to GPIO19 area (x≈88.75, y≈37.48)",
          not btn_r_at_gpio19,
          "BTN_R traces found near GPIO19 — should use GPIO3 instead")


def test_usb_pin_mapping():
    """Test: GPIO pin mapping correctness for USB and buttons.

    Verifies config.py GPIO_NETS and routing.py _PIN_TO_GPIO are consistent.
    Guards against pin mapping regressions that would break firmware upload.
    """
    print("\n── USB Pin Mapping Tests ──")
    sys.path.insert(0, os.path.join(BASE, "scripts"))
    from generate_schematics.config import GPIO_NETS

    # GPIO19 must be USB_D- (not BTN_R or any button)
    check("GPIO19 = USB_D- in config",
          GPIO_NETS.get(19) == "USB_D-",
          f"GPIO19 mapped to '{GPIO_NETS.get(19)}' — must be USB_D-")

    # GPIO20 must be USB_D+ (not JOY_X or any joystick)
    check("GPIO20 = USB_D+ in config",
          GPIO_NETS.get(20) == "USB_D+",
          f"GPIO20 mapped to '{GPIO_NETS.get(20)}' — must be USB_D+")

    # GPIO43 must be SD_MISO (reassigned from BTN_R for PSRAM fix)
    check("GPIO43 = SD_MISO in config",
          GPIO_NETS.get(43) == "SD_MISO",
          f"GPIO43 mapped to '{GPIO_NETS.get(43)}' — must be SD_MISO")

    # No joystick nets should exist
    check("No JOY_X/JOY_Y in GPIO_NETS",
          "JOY_X" not in GPIO_NETS.values() and "JOY_Y" not in GPIO_NETS.values(),
          "joystick nets still present — should be removed")

    # Verify _PIN_TO_GPIO has correct pin 36 = GPIO44 (swapped per datasheet)
    from generate_pcb.routing import _PIN_TO_GPIO
    check("Pin 36 = GPIO44 in _PIN_TO_GPIO",
          _PIN_TO_GPIO.get(36) == 44,
          f"pin 36 mapped to GPIO{_PIN_TO_GPIO.get(36)} — must be GPIO44 (RXD0)")

    # Pins 38/39 are IO2/IO1 — in that order — per the WROOM-1 datasheet
    # (R39-HIGH-1: the table had them swapped and the first article showed
    # D-pad RIGHT acting as A).
    check("Pin 38 = GPIO2 in _PIN_TO_GPIO",
          _PIN_TO_GPIO.get(38) == 2,
          f"pin 38 mapped to GPIO{_PIN_TO_GPIO.get(38)} — must be GPIO2 (IO2)")
    check("Pin 39 = GPIO1 in _PIN_TO_GPIO",
          _PIN_TO_GPIO.get(39) == 1,
          f"pin 39 mapped to GPIO{_PIN_TO_GPIO.get(39)} — must be GPIO1 (IO1)")


def test_firmware_gpio_sync():
    """Test: board_config.h GPIO defines match config.py mapping.

    Ensures firmware will correctly address the physical pins on the PCB.
    """
    print("\n── Firmware GPIO Sync Tests ──")
    board_config = os.path.join(BASE, "software", "main", "board_config.h")
    if not os.path.isfile(board_config):
        check("board_config.h exists", False, "file not found")
        return

    with open(board_config) as f:
        content = f.read()

    # BTN_R must use GPIO3 (reassigned for PSRAM fix)
    import re as _re
    _btn_r_match = _re.search(r'#define\s+BTN_R\s+GPIO_NUM_3\b', content)
    check("Firmware BTN_R = GPIO_NUM_3",
          _btn_r_match is not None,
          "BTN_R not assigned to GPIO_NUM_3 in board_config.h")

    # USB pins defined
    check("Firmware USB_DP = GPIO_NUM_20",
          "#define USB_DP" in content and "GPIO_NUM_20" in content,
          "USB_DP not defined as GPIO_NUM_20 in board_config.h")

    check("Firmware USB_DN = GPIO_NUM_19",
          "#define USB_DN" in content and "GPIO_NUM_19" in content,
          "USB_DN not defined as GPIO_NUM_19 in board_config.h")

    # No joystick defines
    check("No JOY_X/JOY_Y in firmware config",
          "JOY_X" not in content and "JOY_Y" not in content,
          "joystick defines still present in board_config.h")


def test_no_micro_vias():
    """Test: No vias with drill < 0.20mm (JLCPCB surcharge threshold).

    Guards against reintroducing micro-vias that trigger the 4-Wire Kelvin
    Test surcharge ($56.69). JLCPCB requires drill >= 0.20mm.
    """
    print("\n── Micro-Via Guard Test ──")
    vias = _cached_vias()

    micro_vias = [v for v in vias
                  if v.get("drill", 0.35) < 0.20]

    check(f"No micro-vias (drill < 0.20mm) in {len(vias)} vias",
          len(micro_vias) == 0,
          f"{len(micro_vias)} micro-vias found: "
          + ", ".join(f"({v['x']},{v['y']}) drill={v.get('drill',0.35)}"
                      for v in micro_vias[:5]))


def test_mounting_hole_trace_clearance():
    """Test 41: F.Cu traces maintain >= 0.18mm from MH(55,37.5) drill edge.

    Guards against JLCPCB DANGER: PTH-to-trace clearance near mounting holes.
    MH drill=2.5mm, so edge radius=1.25mm from center.
    """
    print("\n── Mounting Hole Trace Clearance Test ──")
    segs = _cached_segments()

    mh_x, mh_y = 55.0, 37.5
    mh_radius = 1.25  # drill=2.5mm
    min_clearance = 0.18  # JLCPCB minimum

    # F.Cu segments near the mounting hole (within 5mm box)
    nearby = [s for s in segs
              if s["layer"] == "F.Cu"
              and min(s["x1"], s["x2"]) < mh_x + 5
              and max(s["x1"], s["x2"]) > mh_x - 5
              and min(s["y1"], s["y2"]) < mh_y + 5
              and max(s["y1"], s["y2"]) > mh_y - 5]

    violations = []
    for s in nearby:
        # Distance from MH center to nearest point on segment
        # For axis-aligned segments:
        if abs(s["x1"] - s["x2"]) < 0.01:  # vertical
            dx = abs(s["x1"] - mh_x)
            sy_min, sy_max = min(s["y1"], s["y2"]), max(s["y1"], s["y2"])
            if sy_min <= mh_y <= sy_max:
                dist = dx
            else:
                dy = min(abs(mh_y - sy_min), abs(mh_y - sy_max))
                dist = (dx**2 + dy**2)**0.5
        elif abs(s["y1"] - s["y2"]) < 0.01:  # horizontal
            dy = abs(s["y1"] - mh_y)
            sx_min, sx_max = min(s["x1"], s["x2"]), max(s["x1"], s["x2"])
            if sx_min <= mh_x <= sx_max:
                dist = dy
            else:
                dx = min(abs(mh_x - sx_min), abs(mh_x - sx_max))
                dist = (dx**2 + dy**2)**0.5
        else:
            # Diagonal — use endpoint distances as conservative estimate
            d1 = ((s["x1"] - mh_x)**2 + (s["y1"] - mh_y)**2)**0.5
            d2 = ((s["x2"] - mh_x)**2 + (s["y2"] - mh_y)**2)**0.5
            dist = min(d1, d2)

        # Gap = center distance - MH radius - half trace width
        gap = dist - mh_radius - s["w"] / 2
        if gap < min_clearance:
            violations.append(
                f"gap={gap:.3f}mm: ({s['x1']},{s['y1']})-({s['x2']},{s['y2']}) w={s['w']}"
            )

    check(f"F.Cu traces >= {min_clearance}mm from MH(55,37.5) drill edge",
          len(violations) == 0,
          f"{len(violations)} violations: {violations[:3]}")


def test_drill_trace_clearance():
    """Test 42: No via/THT drill circle cuts across a different-net trace.

    JLCPCB error: "The indicated hole will cut off the trace."
    For every via and THT pad, checks that the drill edge maintains >= 0.15mm
    clearance from every different-net trace on the same copper layer.
    """
    print("\n── Drill-Trace Clearance Test ──")
    MIN_CLR = 0.15  # mm — JLCPCB minimum

    segs = _cached_segments()
    vias = _cached_vias()
    pads = _get_cache()["pads"]

    # Collect all drill items: (x, y, drill_r, net, layers)
    drill_items = []
    for v in vias:
        drill_items.append({
            "x": v["x"], "y": v["y"],
            "drill_r": v["drill"] / 2.0,
            "net": v["net"],
            "layers": {"F.Cu", "B.Cu"},
            "label": f"via@({v['x']},{v['y']})",
        })

    # THT pads (thru_hole, np_thru_hole) span *.Cu
    for p in pads:
        if p.get("type") not in ("thru_hole", "np_thru_hole"):
            continue
        if p.get("drill", 0) <= 0:
            continue
        drill_items.append({
            "x": p["x"], "y": p["y"],
            "drill_r": p["drill"] / 2.0,
            "net": p["net"],
            "layers": {"F.Cu", "B.Cu"},
            "label": f"{p['ref']}[{p['num']}]@({p['x']},{p['y']})",
        })

    # Deduplicate by position+drill (cache duplicates THT pads per layer)
    seen = set()
    unique_drills = []
    for item in drill_items:
        key = (round(item["x"], 3), round(item["y"], 3),
               round(item["drill_r"], 3))
        if key not in seen:
            seen.add(key)
            unique_drills.append(item)

    # Index segments by layer
    segs_by_layer = {}
    for s in segs:
        segs_by_layer.setdefault(s["layer"], []).append(s)

    violations = []
    for item in unique_drills:
        hx, hy = item["x"], item["y"]
        dr = item["drill_r"]
        h_net = item["net"]
        for layer in item["layers"]:
            for s in segs_by_layer.get(layer, []):
                # Skip same-net (intentional connection)
                if h_net != 0 and s["net"] != 0 and h_net == s["net"]:
                    continue
                dist = _point_to_segment_dist(hx, hy, s)
                gap = dist - dr - s["w"] / 2.0
                if gap < MIN_CLR:
                    violations.append(
                        f"{item['label']} drill_r={dr:.2f} net={h_net} vs "
                        f"{layer} net={s['net']} w={s['w']} "
                        f"({s['x1']},{s['y1']})-({s['x2']},{s['y2']}) "
                        f"gap={gap:.3f}mm"
                    )

    # Baseline reduced to 0: same-net filtering already present, all real
    # drill-to-trace violations resolved in routing.
    # History: 45 → 41 → 43 → 50 → 51 → 0 (routing cleanup)
    BASELINE = 0
    check(
        f"Drill-to-trace violations <= baseline {BASELINE} "
        f"({len(violations)} found, {len(unique_drills)} holes × {len(segs)} segs)",
        len(violations) <= BASELINE,
        f"{len(violations)} violations (baseline {BASELINE}): {violations[:5]}",
    )


def test_trace_pad_different_net_clearance():
    """Test 43: No trace overlaps a pad on a different net.

    JLCPCB error: "The pad and trace is connected, is that correct?"
    Skips if pads appear unnetted (>90% net=0) — run after pad net injection.
    """
    print("\n── Trace-Pad Different-Net Clearance Test ──")
    MIN_CLR = 0.10  # mm — JLCPCB recommended minimum trace-to-pad clearance

    segs = _cached_segments()
    pads = _get_cache()["pads"]

    # Sanity check: skip if pads don't have net assignments yet
    nonzero = sum(1 for p in pads if p["net"] != 0)
    if pads and (nonzero / len(pads)) < 0.10:
        print(f"  SKIP  Pads appear unnetted ({nonzero}/{len(pads)} "
              f"non-zero) — inject pad nets first (Action 2b)")
        return

    # Index pads by layer
    pads_by_layer = {}
    for p in pads:
        pads_by_layer.setdefault(p["layer"], []).append(p)

    violations = []
    for s in segs:
        if s["net"] == 0:
            continue
        sxmin = s["x1"] if s["x1"] < s["x2"] else s["x2"]
        sxmax = s["x1"] if s["x1"] > s["x2"] else s["x2"]
        symin = s["y1"] if s["y1"] < s["y2"] else s["y2"]
        symax = s["y1"] if s["y1"] > s["y2"] else s["y2"]
        shw = s["w"] / 2.0
        for p in pads_by_layer.get(s["layer"], []):
            if p["net"] == 0:
                continue
            if s["net"] == p["net"]:
                continue
            # Conservative reject: the exact segment-to-rect gap can never be
            # smaller than the per-axis gap between the segment's bbox and the
            # pad rect, minus the trace half-width. Skipping here can only
            # skip pairs whose true gap is >= MIN_CLR.
            hw, hh = p["w"] / 2.0, p["h"] / 2.0
            dxg = (p["x"] - hw) - sxmax
            t = sxmin - (p["x"] + hw)
            if t > dxg:
                dxg = t
            dyg = (p["y"] - hh) - symax
            t = symin - (p["y"] + hh)
            if t > dyg:
                dyg = t
            if (dxg if dxg > dyg else dyg) - shw >= MIN_CLR:
                continue
            # Use precise rectangular pad geometry instead of half-diagonal
            gap = _segment_to_rect_gap(s, p["x"], p["y"], p["w"], p["h"])
            if gap < MIN_CLR:
                violations.append(
                    f"seg net={s['net']} {s['layer']} "
                    f"({s['x1']},{s['y1']})-({s['x2']},{s['y2']}) "
                    f"vs {p['ref']}[{p['num']}] net={p['net']} "
                    f"@({p['x']},{p['y']}) gap={gap:.3f}mm"
                )

    # Metric upgraded from half-diagonal circle to exact rectangle distance.
    # History: 140 → 127 (half-diag) → reduced with rectangle metric.
    # Remaining violations are structural: FPC approach columns through J4 pads,
    # traces running between dense IC pins.
    BASELINE = 0
    check(
        f"Trace-to-pad violations <= baseline {BASELINE} "
        f"({len(violations)} found, {len(segs)} segs × {len(pads)} pads)",
        len(violations) <= BASELINE,
        f"{len(violations)} violations (baseline {BASELINE}): {violations[:5]}",
    )


def test_batch_pin_alignment():
    """Test 44: Batch verify all bottom-side IC/connector CPL alignment.

    For each component, verifies that the JLCPCB CPL rotation produces
    correct pin positions matching the PCB gerber copper.

    Algorithm (per component):
      1. Get raw footprint pads (local coordinates from footprints.py)
      2. Compute reference positions: rotate(kicad_rot) -> mirror_X -> translate
      3. Compute JLCPCB model: rotate(cpl_rot) -> mirror_X -> translate
      4. Per-pin max error < 0.1mm -> PASS

    The rotate->mirror order matches the PCB file generation (get_pads)
    and the routing module (_compute_pads).
    """
    print("\n── Batch Pin Alignment Tests ──")
    import math

    sys.path.insert(0, os.path.join(BASE, "scripts"))
    from generate_pcb import footprints as FP
    from generate_pcb.board import _component_placeholders

    REFS = {
        "U1": "ESP32-S3-WROOM-1-N16R8",
        "U2": "ESOP-8",
        "U3": "SOT-23-5",
        "U5": "SOP-16",
        "J1": "USB-C-16P",
        "J4": "FPC-40P-0.5mm",
        "U6": "TF-01A",
    }

    cpl = read_cpl()
    _, placements = _component_placeholders()

    # Build board position lookup: ref -> (x, y, kicad_rotation, layer)
    board_data = {}
    for ref, fp_name, fx, fy, rot, layer in placements:
        board_data[ref] = (fx, fy, rot, layer)

    def _transform_pad(lx, ly, rot_deg, fx, fy):
        """Apply rotate -> mirror_X -> translate (matches PCB file convention)."""
        rad = math.radians(rot_deg)
        cos_r, sin_r = math.cos(rad), math.sin(rad)
        # Rotate
        rx = lx * cos_r - ly * sin_r
        ry = lx * sin_r + ly * cos_r
        # Mirror X for B.Cu
        rx = -rx
        # Translate
        return (fx + rx, fy + ry)

    from generate_pcb.jlcpcb_export import (
        _JLCPCB_ROT_DELTAS, _jlcpcb_rotation,
    )

    for ref, fp_name in REFS.items():
        fx, fy, kicad_rot, layer = board_data[ref]
        cpl_rot = float(cpl[ref]["Rotation"])

        # What this asserts: the CPL FILE on disk carries the angle the
        # generator computes today. That is the stale-upload check — a
        # design-side rotation fix is not done until the CPL is regenerated
        # and re-uploaded.
        #
        # What it deliberately does NOT assert any more: that cpl_rot equals
        # kicad_rot. The previous version transformed every pad twice, once
        # with kicad_rot and once with cpl_rot, and required the two clouds to
        # coincide within 0.1mm — which is just `cpl_rot == kicad_rot` written
        # geometrically. For a bottom-side part the two are SUPPOSED to differ:
        # that difference is the whole purpose of _JLCPCB_ROT_CORRECTIONS. So
        # the check passed U1/U2/U3/J1/U6 by tautology (their correction
        # happens to net out to 0°) and needed a hand-maintained excuse list
        # for U5 and J4, the only two where it bit. A gate that has to be told
        # which parts not to look at proves nothing about those parts.
        #
        # Geometric correctness of the angle itself is proven positively, from
        # the EasyEDA reference land patterns, by
        # scripts/verify_cpl_rotation_law.py — one law per layer, no per-part
        # sign-off table.
        # _component_placeholders() reports KiCad layer names ("B.Cu"/"F.Cu");
        # _jlcpcb_rotation() speaks the CPL vocabulary ("bottom"/"top").
        # Passing the raw name silently takes the top-side branch and skips
        # the mirror + package correction entirely.
        side = "bottom" if layer in ("B.Cu", "bottom") else "top"
        expected = _jlcpcb_rotation(kicad_rot, side, fp_name, ref=ref)
        delta = _JLCPCB_ROT_DELTAS.get(ref)
        origin = (f"formula + {delta}° tape delta" if delta
                  else f"formula from KiCad {kicad_rot:.0f}°/{side}")
        check(
            f"{ref} ({fp_name}) CPL rotation = {expected:.0f}° ({origin})",
            cpl_rot == expected,
            f"CPL file has {cpl_rot:.0f}°, generator emits {expected:.0f}° — "
            f"regenerate and re-upload the CPL",
        )

    # Verify CPL position corrections match expected values
    print("\n── CPL Position Correction Tests ──")
    from generate_pcb.jlcpcb_export import _JLCPCB_POS_CORRECTIONS

    for ref in REFS:
        fx, fy, _, _ = board_data[ref]
        cpl_x = float(cpl[ref]["Mid X"].replace("mm", ""))
        cpl_y = float(cpl[ref]["Mid Y"].replace("mm", ""))
        dx, dy = _JLCPCB_POS_CORRECTIONS.get(ref, (0, 0))
        expected_x = fx + dx
        expected_y = fy + dy
        pos_err = math.hypot(cpl_x - expected_x, cpl_y - expected_y)
        check(
            f"{ref} CPL position correction (err={pos_err:.3f}mm)",
            pos_err < 0.01,
            f"CPL=({cpl_x},{cpl_y}) expected=({expected_x},{expected_y})",
        )


def test_batch_pin_net_assignment():
    """Test 45: Verify PCB pad net assignments match routing for all 7 ICs.

    Checks that each pad in the PCB file has the correct net as assigned by
    the routing module, ensuring no pin swaps from rotation/mirror errors.
    """
    print("\n── Pin Net Assignment Tests ──")
    import math

    sys.path.insert(0, os.path.join(BASE, "scripts"))
    from generate_pcb.board import _component_placeholders
    from generate_pcb.routing import _init_pads, get_pad_nets, generate_all_traces

    REFS = {"U1", "U2", "U3", "U5", "J1", "J4", "U6"}

    # Initialize routing to get net assignments
    _init_pads()
    generate_all_traces()
    pad_nets = get_pad_nets()

    # Parse PCB file for actual pad net assignments
    pcb_pad_nets = {}
    current_ref = None
    with open(PCB_FILE) as f:
        for line in f:
            # Track current footprint reference
            ref_m = re.search(
                r'\(property "Reference" "([^"]+)"', line)
            if ref_m:
                current_ref = ref_m.group(1)
            # Reset on footprint boundary
            if line.strip().startswith("(footprint "):
                current_ref = None
            # Parse pad with net
            pad_m = re.search(
                r'\(pad "([^"]*)".*\(net (\d+)', line)
            if pad_m and current_ref and current_ref in REFS:
                pin = pad_m.group(1)
                net_id = int(pad_m.group(2))
                pcb_pad_nets[(current_ref, pin)] = net_id

    # Compare routing net assignments vs PCB file
    for ref in sorted(REFS):
        mismatches = []
        total_routed = 0
        for (r, pin), routing_net in sorted(pad_nets.items()):
            if r != ref:
                continue
            total_routed += 1
            pcb_net = pcb_pad_nets.get((r, pin), 0)
            if pcb_net != routing_net:
                mismatches.append(
                    f"pin {pin}: routing={routing_net} pcb={pcb_net}")
        if total_routed > 0:
            check(
                f"{ref} net assignments ({total_routed} routed pins)",
                len(mismatches) == 0,
                "; ".join(mismatches[:5]),
            )


def test_j4_fpc_orientation():
    """Test: J4 FPC connector cable insertion side faces toward FPC slot.

    Bottom-contact FPC connector: signal pads = cable insertion side.
    Signal pads must be at lower X (closer to FPC slot at X≈127) than
    mounting pads (latch side) for the ribbon cable to reach from the slot.
    Also verifies CPL rotation produces correct pick-and-place orientation.
    """
    print("\n── J4 FPC Orientation Tests ──")

    with open(PCB_FILE) as f:
        pcb = f.read()

    # Find J4 FPC footprint block
    j4_start = pcb.find('(footprint "FPC-40P-0.5mm"')
    if j4_start < 0:
        check("J4 FPC footprint found in PCB", False, "not found")
        return
    depth = 0
    j4_end = j4_start
    for i in range(j4_start, len(pcb)):
        if pcb[i] == '(':
            depth += 1
        elif pcb[i] == ')':
            depth -= 1
            if depth == 0:
                j4_end = i + 1
                break
    j4_block = pcb[j4_start:j4_end]

    # Get J4 center
    at_m = re.search(r'\(at\s+([\d.]+)\s+([\d.]+)', j4_block)
    j4_cx = float(at_m.group(1))

    # Collect signal pad X positions (pins 1-40) and mounting pad X (pins 41-42)
    signal_xs = []
    mount_xs = []
    for pm in re.finditer(
        r'\(pad "(\d+)" smd \w+ \(at ([-\d.]+) [-\d.]+\)', j4_block
    ):
        pnum = int(pm.group(1))
        gx = j4_cx + float(pm.group(2))
        if pnum <= 40:
            signal_xs.append(gx)
        else:
            mount_xs.append(gx)

    if not signal_xs or not mount_xs:
        check("J4 pads parsed", False, f"signal={len(signal_xs)} mount={len(mount_xs)}")
        return

    avg_sig_x = sum(signal_xs) / len(signal_xs)
    avg_mnt_x = sum(mount_xs) / len(mount_xs)

    # PCB test: signal pads must be closer to slot (lower X) than mounting pads
    # FPC slot right edge is at X=128.5
    slot_right_x = 128.5
    check(
        "J4 signal pads face toward FPC slot (signal X < mount X)",
        avg_sig_x < avg_mnt_x,
        f"signal avg X={avg_sig_x:.2f}, mount avg X={avg_mnt_x:.2f}",
    )
    check(
        "J4 signal pads between slot and center",
        slot_right_x < avg_sig_x < j4_cx,
        f"slot={slot_right_x}, signal={avg_sig_x:.2f}, center={j4_cx}",
    )
    check(
        "J4 cable bridge distance < 8mm",
        0 < (avg_sig_x - slot_right_x) < 8,
        f"gap={avg_sig_x - slot_right_x:.1f}mm",
    )

    # CPL test: the pick-and-place angle must obey the per-layer rotation law.
    #
    # This used to assert `j4_rot == 270` against a hand-written comment. That
    # is a tautology, not a test: it restated the number the generator already
    # emitted, so it could only ever fail if someone changed the generator —
    # and when the 270 turned out to be wrong (an eyeballed 3D overlay, see
    # jlcpcb_export._JLCPCB_ROT_DELTAS) this assertion defended the bug instead
    # of catching it. Deriving the expected angle instead means this check
    # tracks the law, and a future placement change moves both together.
    cpl = read_cpl()
    j4_rot = int(cpl["J4"]["Rotation"]) % 360
    law = _load_rotation_law()
    j4_law = next((r for r in law.evaluate() if r["ref"] == "J4"), None)
    check(
        "J4 CPL rotation obeys the bottom-layer rotation law",
        j4_law is not None and j4_law["status"] in ("OK", "EXCEPTION"),
        (f"got {j4_rot}deg, law wants "
         f"{j4_law['law_cpl']:.0f}deg" if j4_law and j4_law.get("law_cpl") is not None
         else f"got {j4_rot}deg, J4 not evaluable by the law"),
    )


def test_j4_display_pin_reversal():
    """Test: J4 connector pad nets match display pin reversal (41-N mapping).

    The ILI9488 display in landscape (CCW rotation) has its FPC cable
    passing straight through the PCB slot.  Display pin N physically
    contacts connector pad (41-N).  Verify that each connector pad
    carries the correct net for the display pin it mates with.
    """
    print("\n── J4 Display Pin Reversal Tests ──")

    with open(PCB_FILE) as f:
        pcb = f.read()

    # Find J4 block
    j4_start = pcb.find('(footprint "FPC-40P-0.5mm"')
    if j4_start < 0:
        check("J4 found", False, "not found")
        return
    depth = 0
    j4_end = j4_start
    for i in range(j4_start, len(pcb)):
        if pcb[i] == '(':
            depth += 1
        elif pcb[i] == ')':
            depth -= 1
            if depth == 0:
                j4_end = i + 1
                break
    j4_block = pcb[j4_start:j4_end]

    # Extract pad -> net mapping
    pad_nets = {}
    for m in re.finditer(
        r'\(pad "(\d+)" smd \w+ \(at [-\d.]+ [-\d.]+\).*?'
        r'\(net (\d+) "([^"]*)"\)', j4_block
    ):
        pad_nets[int(m.group(1))] = m.group(3)

    # Expected display pin -> signal mapping (ILI9488 datasheet)
    display_pin_signal = {
        5: "GND", 6: "+3V3", 7: "+3V3",
        9: "LCD_CS", 10: "LCD_DC", 11: "LCD_WR",
        # Pin 12 (LCD_RD): NC on PCB, tied HIGH on display module
        # Pin 33 (LCD_BL): NC on PCB, powered by display module
        15: "LCD_RST", 16: "GND",
        17: "LCD_D0", 18: "LCD_D1", 19: "LCD_D2", 20: "LCD_D3",
        21: "LCD_D4", 22: "LCD_D5", 23: "LCD_D6", 24: "LCD_D7",
        34: "GND", 35: "GND", 36: "GND", 37: "GND",
        38: "+3V3", 39: "+3V3", 40: "GND",
    }

    # Verify: display pin N -> connector pad (41-N) -> correct net
    errors = []
    for disp_pin, expected_net in sorted(display_pin_signal.items()):
        conn_pad = 41 - disp_pin
        actual_net = pad_nets.get(conn_pad, "")
        if actual_net != expected_net:
            errors.append(
                f"Display pin {disp_pin} ({expected_net}) -> "
                f"conn pad {conn_pad}: got '{actual_net}'"
            )

    check(
        f"J4 display pin reversal (41-N): {len(display_pin_signal)} signals",
        len(errors) == 0,
        "; ".join(errors[:5]) if errors else "all correct",
    )

    # Verify pin ordering: connector pad 1 (north) = display pin 40 (south)
    # and connector pad 40 (south) = display pin 1 (north)
    j4_at = re.search(r'\(at\s+([\d.]+)\s+([\d.]+)', j4_block)
    j4_cy = float(j4_at.group(2))

    # Get Y positions of key pads
    pad_ys = {}
    for m in re.finditer(
        r'\(pad "(\d+)" smd \w+ \(at [-\d.]+ ([-\d.]+)\)', j4_block
    ):
        pad_ys[int(m.group(1))] = j4_cy + float(m.group(2))

    # Pad 1 should be NORTH (low Y), pad 40 should be SOUTH (high Y)
    if 1 in pad_ys and 40 in pad_ys:
        check(
            "J4 pad 1 (display pin 40) at NORTH, pad 40 (display pin 1) at SOUTH",
            pad_ys[1] < pad_ys[40],
            f"pad1 Y={pad_ys[1]:.2f}, pad40 Y={pad_ys[40]:.2f}",
        )

    # Verify data bus order: D0 on south side, D7 on north side
    # (display D0=pin17 -> conn pad 24 at south, D7=pin24 -> conn pad 17 at north)
    if 17 in pad_ys and 24 in pad_ys:
        check(
            "J4 data bus: LCD_D7 (conn pad 17) north of LCD_D0 (conn pad 24)",
            pad_ys[17] < pad_ys[24],
            f"D7@pad17 Y={pad_ys[17]:.2f}, D0@pad24 Y={pad_ys[24]:.2f}",
        )

    # Verify ctrl signals south of data bus
    # CS=display pin 9 -> conn pad 32 should be south of D0=conn pad 24
    if 32 in pad_ys and 24 in pad_ys:
        check(
            "J4 ctrl (LCD_CS pad 32) south of data (LCD_D0 pad 24)",
            pad_ys[32] > pad_ys[24],
            f"CS@pad32 Y={pad_ys[32]:.2f}, D0@pad24 Y={pad_ys[24]:.2f}",
        )


def test_via_annular_ring_trace_clearance():
    """Test: Via annular ring copper maintains clearance from different-net traces.

    CRITICAL FIX: test_drill_trace_clearance (test 42) uses drill radius
    (via["drill"]/2) but the COPPER extends to via["size"]/2. For our standard
    0.9/0.35 vias, the annular ring extends 0.275mm beyond the drill edge.
    A trace can pass test 42 yet physically overlap the copper by 0.275mm.

    This test uses the actual copper radius (via_size/2) to check clearance.
    """
    print("\n── Via Annular Ring to Trace Clearance Test ──")
    MIN_CLR = 0.10  # mm — JLCPCB minimum copper-to-copper

    segs = _cached_segments()
    vias = _cached_vias()

    # Index segments by layer
    segs_by_layer = {}
    for s in segs:
        segs_by_layer.setdefault(s["layer"], []).append(s)

    violations = []
    for v in vias:
        vx, vy = v["x"], v["y"]
        copper_r = v["size"] / 2.0  # annular ring radius (NOT drill radius)
        v_net = v["net"]
        if v_net == 0:
            continue
        # Vias have copper on F.Cu and B.Cu
        for layer in ("F.Cu", "B.Cu"):
            for s in segs_by_layer.get(layer, []):
                if s["net"] == 0 or s["net"] == v_net:
                    continue
                dist = _point_to_segment_dist(vx, vy, s)
                gap = dist - copper_r - s["w"] / 2.0
                if gap < MIN_CLR:
                    violations.append(
                        f"via@({vx:.1f},{vy:.1f}) sz={v['size']} net={v_net} "
                        f"vs {layer} net={s['net']} "
                        f"({s['x1']:.1f},{s['y1']:.1f})-"
                        f"({s['x2']:.1f},{s['y2']:.1f}) w={s['w']} "
                        f"gap={gap:.3f}mm"
                    )

    # Baseline: current design has some inherent proximity in dense areas.
    # This catches the 0.275mm blind spot from test 42 (drill vs copper).
    BASELINE = 0
    check(
        f"Via annular ring to trace gap >= {MIN_CLR}mm "
        f"({len(violations)} violations)",
        len(violations) <= BASELINE,
        f"{len(violations)} violations (baseline {BASELINE}): "
        + "; ".join(violations[:5]),
    )


def test_signal_power_via_overlap():
    """Test: No signal trace overlaps ANY power via annular ring (single-net).

    Complement to test_power_bridge_detection which requires 2+ different power
    nets. This test catches the simpler case: a signal trace touching even ONE
    power via creates a signal-to-power short. For example, BTN_Y overlapping
    a +3V3 via makes the button permanently read HIGH.
    """
    print("\n── Signal-to-Power Via Overlap Test ──")

    segs = _cached_segments()
    vias = _cached_vias()

    # Read net names from PCB file
    net_names = {}
    with open(PCB_FILE) as f:
        for m in re.finditer(r'\(net\s+(\d+)\s+"([^"]*)"\)', f.read()):
            net_names[int(m.group(1))] = m.group(2)

    POWER_NETS = {"GND", "VBUS", "+5V", "+3V3", "BAT+"}
    power_net_ids = {nid for nid, name in net_names.items() if name in POWER_NETS}
    power_vias = [v for v in vias if v["net"] in power_net_ids]

    violations = []
    for seg in segs:
        seg_net = seg["net"]
        if seg_net == 0 or seg_net in power_net_ids:
            continue  # skip unnetted and power-net traces

        seg_name = net_names.get(seg_net, f"net{seg_net}")

        for via in power_vias:
            if via["net"] == seg_net:
                continue
            vr = via["size"] / 2.0
            sw = seg["w"] / 2.0
            dist = _point_to_segment_dist(via["x"], via["y"], seg)
            gap = dist - vr - sw
            if gap < 0:
                via_name = net_names.get(via["net"], f"net{via['net']}")
                violations.append(
                    f"{seg['layer']} {seg_name} "
                    f"({seg['x1']:.1f},{seg['y1']:.1f})->"
                    f"({seg['x2']:.1f},{seg['y2']:.1f}) "
                    f"overlaps {via_name} via "
                    f"({via['x']:.1f},{via['y']:.1f}) "
                    f"gap={gap:.3f}mm"
                )

    check(
        f"No signal traces overlap power via copper "
        f"({len(violations)} overlaps found)",
        len(violations) == 0,
        f"Signal-power overlaps:\n" + "\n".join(f"    {v}" for v in violations[:10])
        if violations else "",
    )


def test_trace_through_ic_pad():
    """Test: No trace passes through an IC/connector pad on a different net.

    Catches traces routed through component pad areas that will create
    short circuits when the component is soldered. This includes:
    - Active pads (net != 0) overlapped by different-net traces (CRITICAL)
    - NC pads (net == 0) of ICs/connectors overlapped by traces (HIGH)

    NC pads of passive components (R, C, L) are excluded because their
    pad-to-trace overlaps are typically intended connections where the
    pad net assignment is missing from the PCB file.
    """
    print("\n── Trace Through IC/Connector Pad Test ──")

    segs = _cached_segments()
    pads = _get_cache()["pads"]

    # Only check IC, connector, and switch footprints (not passives)
    IC_PREFIXES = ("U", "J", "SW")
    ic_pads = [p for p in pads if any(p["ref"].startswith(pfx) for pfx in IC_PREFIXES)]

    # Read net names from PCB file
    net_names = {}
    with open(PCB_FILE) as f:
        for m in re.finditer(r'\(net\s+(\d+)\s+"([^"]*)"\)', f.read()):
            net_names[int(m.group(1))] = m.group(2)

    # Known safe NC pins (internally disconnected per datasheet, or
    # intended same-net connections with missing net assignment in PCB).
    SAFE_NC = {
        # PAM8403 (U5): pins 2, 9, 12 are true NC per datasheet
        ("U5", "2"), ("U5", "9"), ("U5", "12"),
        # PAM8403 (U5): pin 8 = VREF output, PAM_VREF trace is intended connection
        ("U5", "8"),
        # FPC J4: pin 42 is mounting pad (no internal connection)
        ("J4", "42"),
        # FPC J4: pin 37 is NC per display datasheet (GND plane connects via zone)
        ("J4", "37"),
        # ESP32-S3 (U1): pin 1 = 3V3 power (config.py), net not assigned in PCB
        ("U1", "1"),
        # IP5306 (U2): pins 3, 4 are true NC per datasheet
        ("U2", "3"), ("U2", "4"),
        # AMS1117 (U3): pin 2 = Vout (+3V3), trace is intended connection
        ("U3", "2"),
        # SD socket (U6): pad 8 = DAT1, unused in SPI mode; pad 9 = Cd, the
        # socket's own card-detect contact, which this design does not read
        ("U6", "8"), ("U6", "9"),
        # MSK12C02 power switch (SW16): shell/mounting pads, no internal connection
        ("SW16", "4a"), ("SW16", "4b"), ("SW16", "4c"), ("SW16", "4d"),
    }

    # Index pads by layer
    pads_by_layer: dict[str, list] = {}
    for p in ic_pads:
        pads_by_layer.setdefault(p["layer"], []).append(p)

    # Also check vias (they exist on all layers)
    vias = _cached_vias()

    critical = []
    high = []

    for s in segs:
        s_net = s["net"]
        if s_net == 0:
            continue
        sw = s["w"]
        sx1, sy1, sx2, sy2 = s["x1"], s["y1"], s["x2"], s["y2"]
        seg_xmin = min(sx1, sx2) - sw / 2
        seg_xmax = max(sx1, sx2) + sw / 2
        seg_ymin = min(sy1, sy2) - sw / 2
        seg_ymax = max(sy1, sy2) + sw / 2

        for p in pads_by_layer.get(s["layer"], []):
            if s_net == p["net"] and p["net"] != 0:
                continue  # same net = intended connection
            px, py, pw, ph = p["x"], p["y"], p["w"], p["h"]
            pad_xmin = px - pw / 2
            pad_xmax = px + pw / 2
            pad_ymin = py - ph / 2
            pad_ymax = py + ph / 2

            # AABB overlap. The segment AABB equals the trace copper
            # exactly while the segment is axis-aligned, which is true of
            # almost every trace on this board. For a diagonal it is the
            # bounding box of the capsule and overstates the copper near
            # the corners, so confirm with the exact capsule-vs-rect
            # distance before reporting.
            if (seg_xmax > pad_xmin and seg_xmin < pad_xmax and
                    seg_ymax > pad_ymin and seg_ymin < pad_ymax):
                if (abs(sx2 - sx1) > 1e-6 and abs(sy2 - sy1) > 1e-6
                        and _capsule_rect_gap(sx1, sy1, sx2, sy2, sw / 2,
                                              pad_xmin, pad_ymin,
                                              pad_xmax, pad_ymax) >= 0.0):
                    continue
                s_name = net_names.get(s_net, f"net{s_net}")
                p_name = net_names.get(p["net"], "NC") if p["net"] != 0 else "NC"
                entry = (f"{p['ref']}[{p['num']}]({p_name}) "
                         f"← {s_name} {s['layer']}")

                if p["net"] != 0:
                    critical.append(entry)
                elif (p["ref"], p["num"]) not in SAFE_NC:
                    high.append(entry)

    # Deduplicate
    critical = sorted(set(critical))
    high = sorted(set(high))

    if critical:
        for v in critical[:10]:
            print(f"    CRITICAL: {v}")
    if high:
        for v in high[:10]:
            print(f"    HIGH: {v}")

    check(
        f"No traces through IC/connector pads (different-net) "
        f"({len(critical)} critical, {len(high)} high)",
        len(critical) == 0 and len(high) == 0,
        f"{len(critical)} critical + {len(high)} high violations",
    )


def test_trace_crossing_same_layer():
    """Test: No two different-net traces cross on the same copper layer.

    Existing test_trace_spacing uses _seg_min_dist() which only handles
    PARALLEL axis-aligned segments. Perpendicular crossings (e.g., a horizontal
    trace crossing a vertical trace) are completely invisible to that check.
    This test detects actual 2D segment intersections.
    """
    print("\n── Trace Crossing Same Layer Test ──")

    segs = _cached_segments()

    by_layer = {}
    for s in segs:
        if "Cu" in s["layer"]:
            by_layer.setdefault(s["layer"], []).append(s)

    def segments_cross(s1, s2):
        """Check if two segments' copper areas overlap (2D intersection
        accounting for trace width)."""
        # For axis-aligned segments, use direct geometry
        tol = 0.01
        s1_horiz = abs(s1["y1"] - s1["y2"]) < tol
        s1_vert = abs(s1["x1"] - s1["x2"]) < tol
        s2_horiz = abs(s2["y1"] - s2["y2"]) < tol
        s2_vert = abs(s2["x1"] - s2["x2"]) < tol

        # Horizontal vs Vertical crossing (most common case)
        if s1_horiz and s2_vert:
            h, v = s1, s2
        elif s1_vert and s2_horiz:
            h, v = s2, s1
        else:
            return None  # skip parallel or diagonal (handled elsewhere)

        hx_lo = min(h["x1"], h["x2"])
        hx_hi = max(h["x1"], h["x2"])
        hy = h["y1"]
        hw = h["w"] / 2.0

        vx = v["x1"]
        vy_lo = min(v["y1"], v["y2"])
        vy_hi = max(v["y1"], v["y2"])
        vw = v["w"] / 2.0

        # Check if intersection point is within both segments (with width)
        if (hx_lo - vw <= vx <= hx_hi + vw and
                vy_lo - hw <= hy <= vy_hi + hw):
            # Compute copper-to-copper gap at crossing point
            x_gap = min(abs(vx - hx_lo), abs(vx - hx_hi))
            y_gap = min(abs(hy - vy_lo), abs(hy - vy_hi))
            # If the crossing point is INSIDE both segments (not just at ends)
            if hx_lo <= vx <= hx_hi and vy_lo <= hy <= vy_hi:
                return 0.0  # direct overlap at crossing
            # Near-miss at segment endpoint
            gap_x = max(0, max(hx_lo - vx, vx - hx_hi)) - vw
            gap_y = max(0, max(vy_lo - hy, hy - vy_hi)) - hw
            return max(gap_x, gap_y)

        return None  # no crossing

    violations = []
    for layer, layer_segs in by_layer.items():
        n = len(layer_segs)
        for i in range(n):
            for j in range(i + 1, n):
                s1, s2 = layer_segs[i], layer_segs[j]
                if s1["net"] == 0 or s2["net"] == 0:
                    continue
                if s1["net"] == s2["net"]:
                    continue
                gap = segments_cross(s1, s2)
                if gap is not None and gap <= 0:
                    violations.append(
                        f"{layer}: net{s1['net']} "
                        f"({s1['x1']:.1f},{s1['y1']:.1f})->"
                        f"({s1['x2']:.1f},{s1['y2']:.1f}) "
                        f"crosses net{s2['net']} "
                        f"({s2['x1']:.1f},{s2['y1']:.1f})->"
                        f"({s2['x2']:.1f},{s2['y2']:.1f})"
                    )

    check(
        f"No different-net trace crossings on same layer "
        f"({len(violations)} crossings found)",
        len(violations) == 0,
        f"Crossings:\n" + "\n".join(f"    {v}" for v in violations[:10])
        if violations else "",
    )


def test_power_bridge_detection():
    """Test: No signal trace bridges two different power-net vias.

    A signal trace that overlaps via_A (net=VBUS) AND via_B (net=GND) creates
    a direct power-to-power short through the signal copper, even though the
    trace itself is a signal net. This is the root cause of BUG #3 (LCD_RST
    bridging VBUS and GND on F.Cu) which was missed by pairwise checks.

    For every trace segment, collects all power vias it overlaps (gap < 0).
    If a single segment touches vias from 2+ different power nets, it's a
    CRITICAL bridge — the board will have a power short.
    """
    print("\n── Power Bridge Detection Test ──")

    segs = _cached_segments()
    vias = _cached_vias()

    # Read net names from PCB file
    net_names = {}
    with open(PCB_FILE) as f:
        for m in re.finditer(r'\(net\s+(\d+)\s+"([^"]*)"\)', f.read()):
            net_names[int(m.group(1))] = m.group(2)

    POWER_NETS = {"GND", "VBUS", "+5V", "+3V3", "BAT+"}
    power_net_ids = {nid for nid, name in net_names.items() if name in POWER_NETS}

    # Collect power vias
    power_vias = [v for v in vias if v["net"] in power_net_ids]

    def seg_via_overlap(seg, via):
        """Return gap (negative = overlap) between segment and via annular ring."""
        vx, vy = via["x"], via["y"]
        vr = via["size"] / 2.0
        sw = seg["w"] / 2.0
        dist = _point_to_segment_dist(vx, vy, seg)
        return dist - sw - vr

    # For each segment, find all power vias it overlaps (gap < 0)
    bridges = []
    for seg in segs:
        seg_net = seg["net"]
        if seg_net in power_net_ids:
            continue  # power trace touching power via = expected
        if seg_net == 0:
            continue

        touched_power = {}  # power_net_name -> list of via details
        for via in power_vias:
            if via["net"] == seg_net:
                continue  # same net
            # Vias span all layers, so check regardless of segment layer
            gap = seg_via_overlap(seg, via)
            if gap < 0:
                via_name = net_names.get(via["net"], f"net{via['net']}")
                if via_name not in touched_power:
                    touched_power[via_name] = []
                touched_power[via_name].append({
                    "x": via["x"], "y": via["y"],
                    "gap": gap,
                })

        if len(touched_power) >= 2:
            seg_name = net_names.get(seg_net, f"net{seg_net}")
            nets_bridged = sorted(touched_power.keys())
            details = []
            for pn in nets_bridged:
                for v in touched_power[pn]:
                    details.append(f"{pn}@({v['x']:.1f},{v['y']:.1f}) "
                                   f"gap={v['gap']:.3f}")
            bridges.append(
                f"{seg['layer']} {seg_name} "
                f"({seg['x1']:.1f},{seg['y1']:.1f})->"
                f"({seg['x2']:.1f},{seg['y2']:.1f}) "
                f"bridges {' + '.join(nets_bridged)}: "
                f"{'; '.join(details)}"
            )

    check(
        f"No signal traces bridge 2+ power nets "
        f"({len(bridges)} bridges found)",
        len(bridges) == 0,
        f"CRITICAL bridges:\n" + "\n".join(f"    {b}" for b in bridges)
        if bridges else "",
    )


# ══════════════════════════════════════════════════════════════════════
# JLCDFM Manufacturing Rules — Comprehensive Board-Wide Tests
# ══════════════════════════════════════════════════════════════════════
#
# These tests implement EVERY JLCDFM manufacturing rule, checking ALL
# components, traces, vias, and pads on the entire board.  Thresholds
# are JLCPCB standard process capabilities (not advanced).
#
# Board geometry:
#   - 160 x 75 mm, origin at (0,0) top-left
#   - 6mm corner radius
#   - FPC slot cutout: (125.5, 23.5) to (128.5, 47.5)
#   - Board edges: x=0, x=160, y=0, y=75 (with arcs at corners)


def _board_edge_distance(px, py):
    """Minimum distance from a point to the nearest board edge.

    Considers straight edges and FPC slot edges. Does NOT account for
    corner arcs (conservative: corner arcs are further away than the
    straight-line extension, so we undercount slightly at corners).
    """
    import math
    # Outer board edges
    d_left = px
    d_right = 160.0 - px
    d_top = py
    d_bottom = 75.0 - py

    d_min = min(d_left, d_right, d_top, d_bottom)

    # FPC slot cutout: rectangle (125.5, 23.5) to (128.5, 47.5)
    # Only check if point is near the slot
    if 120.0 < px < 134.0 and 18.0 < py < 53.0:
        # Distance to each slot edge (only if point is "facing" that edge)
        if 125.5 <= px <= 128.5 and 23.5 <= py <= 47.5:
            # Point is INSIDE the slot (shouldn't happen for copper)
            d_min = 0.0
        else:
            # Left edge of slot (x=125.5) — only if point is left of slot
            if px < 125.5 and 23.5 <= py <= 47.5:
                d_min = min(d_min, 125.5 - px)
            # Right edge of slot (x=128.5) — only if point is right of slot
            if px > 128.5 and 23.5 <= py <= 47.5:
                d_min = min(d_min, px - 128.5)
            # Top edge of slot (y=23.5) — only if point is above slot
            if py < 23.5 and 125.5 <= px <= 128.5:
                d_min = min(d_min, 23.5 - py)
            # Bottom edge of slot (y=47.5) — only if point is below slot
            if py > 47.5 and 125.5 <= px <= 128.5:
                d_min = min(d_min, py - 47.5)
            # Corner distances to slot corners
            for cx, cy in [(125.5, 23.5), (128.5, 23.5),
                           (125.5, 47.5), (128.5, 47.5)]:
                d_min = min(d_min, math.hypot(px - cx, py - cy))

    return d_min


# ── Fine-pitch / tight-pitch component refs: violations between these pads are
# structural (inherent to the component package, not a routing error).
# ESP32 QFN (0.5mm pitch), FPC 40P (0.5mm pitch), USB-C 16P (tight shield),
# IP5306 ESOP-8 (1.27mm + EP), PAM8403 SOP-16 (1.27mm), TF-01A SD slot (1.1mm).
# L1 inductor (large pads, conservative half-diagonal overstates overlap).
# SPK1 speaker (large 3.6mm pads, traces routed underneath).
# C3/C4 bypass caps (placed tight to ESP32), C17 (IP5306 bypass),
# R20/R21/C21 (PAM8403 passives, placed tight to IC),
# U4 (USBLC6-2SC6 SOT-23-6, 0.95mm pitch), R22/R23 (22Ω 0402 inline).
# JLCPCB routinely manufactures these packages — their DFM review accepts them.
_FINE_PITCH_REFS = {"U1", "U2", "U4", "U5", "U6", "J4", "J3", "J1", "L1", "SPK1",
                    "C3", "C4", "C17", "R20", "R21", "C21", "R22", "R23"}


def _pad_pair_gap(p1, p2):
    """Exact edge-to-edge gap between two axis-aligned rectangular pads.

    Every pad emitted by generate_pcb/footprints.py is axis-aligned: pads are
    pre-rotated at generation time and 90/270 deg rotations swap (w, h), so
    the stored (x, y, w, h) is already an axis-aligned bounding box.

    The pad-spacing and soldermask-bridge tests used to approximate this with
    the half-diagonal circumscribed radius, which over-reports badly for
    elongated pads: an SOT-23-5 pin row (pads 1.10 x 0.60 at 0.95 pitch) has a
    real 0.35 mm gap but a half-diagonal "gap" of -0.30 mm, and the two pads of
    a 4x4 inductor (1.50 x 4.00 at 3.60 pitch) have a real 2.10 mm gap but a
    half-diagonal "gap" of -0.67 mm. That systematic error is why those tests
    needed the _FINE_PITCH_REFS bypass to pass at all — the bypass was hiding
    the measurement bug, and along with it every genuine pad-spacing problem on
    U1/U2/U5/J1/J4/U6. With the exact geometry the bypass is unnecessary: the
    whole board reports 0 violations with no refs excluded.
    """
    dx = abs(p1["x"] - p2["x"]) - (p1["w"] + p2["w"]) / 2
    dy = abs(p1["y"] - p2["y"]) - (p1["h"] + p2["h"]) / 2
    if dx > 0 and dy > 0:
        return math.hypot(dx, dy)   # diagonal separation
    return max(dx, dy)              # overlapping in one axis (or both)


def test_jlcdfm_trace_spacing():
    """JLCDFM: Minimum trace-to-trace spacing >= 0.15mm on ALL layers.

    Checks every pair of trace segments on the same copper layer with
    different nets.  Uses both parallel (axis-aligned) and perpendicular
    crossing detection for comprehensive coverage.
    """
    print("\n── JLCDFM: Trace-to-Trace Spacing (0.15mm) ──")
    MIN_GAP = 0.15
    segs = _cached_segments()

    by_layer = {}
    for s in segs:
        if "Cu" in s["layer"]:
            by_layer.setdefault(s["layer"], []).append(s)

    violations = []
    for layer, layer_segs in by_layer.items():
        n = len(layer_segs)
        for i in range(n):
            for j in range(i + 1, n):
                s1, s2 = layer_segs[i], layer_segs[j]
                if s1["net"] == s2["net"] or s1["net"] == 0 or s2["net"] == 0:
                    continue
                gap = _seg_min_dist(s1, s2)
                if gap is not None and gap < MIN_GAP:
                    violations.append(
                        f"{layer}: net{s1['net']} vs net{s2['net']} "
                        f"gap={gap:.3f}mm at "
                        f"({s1['x1']:.1f},{s1['y1']:.1f})-({s1['x2']:.1f},{s1['y2']:.1f}) vs "
                        f"({s2['x1']:.1f},{s2['y1']:.1f})-({s2['x2']:.1f},{s2['y2']:.1f})"
                    )

    # Report all violations with coordinates
    if violations:
        for v in violations[:20]:
            print(f"    VIOLATION: {v}")
        if len(violations) > 20:
            print(f"    ... and {len(violations) - 20} more")

    check(f"JLCDFM trace spacing >= {MIN_GAP}mm ({len(violations)} violations in {len(segs)} segs)",
          len(violations) == 0,
          f"{len(violations)} violations found")


def test_jlcdfm_annular_ring():
    """JLCDFM: Via annular ring >= 0.13mm for ALL vias.

    annular_ring = (size - drill) / 2.  JLCPCB standard minimum is 0.13mm.
    """
    print("\n── JLCDFM: Via Annular Ring (0.13mm) ──")
    MIN_RING = 0.13
    vias = _cached_vias()

    violations = []
    for v in vias:
        ring = (v["size"] - v["drill"]) / 2.0
        if ring < MIN_RING - 0.001:  # 1um tolerance for FP rounding
            violations.append(
                f"via@({v['x']:.2f},{v['y']:.2f}) size={v['size']} "
                f"drill={v['drill']} ring={ring:.3f}mm < {MIN_RING}mm"
            )

    if violations:
        for v in violations:
            print(f"    VIOLATION: {v}")

    check(f"JLCDFM annular ring >= {MIN_RING}mm ({len(vias)} vias)",
          len(violations) == 0,
          f"{len(violations)} violations")


def test_jlcdfm_trace_width():
    """JLCDFM: Every trace segment width >= 0.15mm (JLCPCB standard min)."""
    print("\n── JLCDFM: Minimum Trace Width (0.15mm) ──")
    MIN_WIDTH = 0.15
    segs = _cached_segments()

    violations = []
    for s in segs:
        w = s.get("width", s.get("w", 0))
        if w < MIN_WIDTH - 0.001:
            violations.append(
                f"{s['layer']}: width={w:.3f}mm at "
                f"({s['x1']:.2f},{s['y1']:.2f})-({s['x2']:.2f},{s['y2']:.2f})"
            )

    if violations:
        for v in violations:
            print(f"    VIOLATION: {v}")

    check(f"JLCDFM trace width >= {MIN_WIDTH}mm ({len(segs)} segments)",
          len(violations) == 0,
          f"{len(violations)} violations")


def test_jlcdfm_pad_to_board_edge():
    """JLCDFM: Every pad at least 0.3mm from nearest board edge.

    Checks all pads (SMD and THT) against outer board edges and FPC slot.
    """
    print("\n── JLCDFM: Pad-to-Board-Edge (0.3mm) ──")
    MIN_DIST = 0.3
    pads = _get_cache()["pads"]

    violations = []
    seen = set()  # dedupe by (ref, num) since cache duplicates per layer
    for p in pads:
        key = (p["ref"], p["num"])
        if key in seen:
            continue
        seen.add(key)
        # Pad edge distance = center distance - half pad size
        half_w = p["w"] / 2.0
        half_h = p["h"] / 2.0
        pad_radius = max(half_w, half_h)  # conservative: largest extent
        center_dist = _board_edge_distance(p["x"], p["y"])
        edge_dist = center_dist - pad_radius
        if edge_dist < MIN_DIST:
            violations.append(
                f"{p['ref']}[{p['num']}] @({p['x']:.2f},{p['y']:.2f}) "
                f"edge_dist={edge_dist:.3f}mm (center={center_dist:.3f}, "
                f"pad_r={pad_radius:.2f})"
            )

    if violations:
        for v in violations[:20]:
            print(f"    VIOLATION: {v}")
        if len(violations) > 20:
            print(f"    ... and {len(violations) - 20} more")

    check(f"JLCDFM pad-to-edge >= {MIN_DIST}mm ({len(seen)} unique pads)",
          len(violations) == 0,
          f"{len(violations)} violations")


def test_jlcdfm_pad_spacing():
    """JLCDFM: All pad pairs on same layer, different nets, gap >= 0.15mm.

    Iterates over ALL pads grouped by layer and measures the exact
    edge-to-edge gap between axis-aligned pad rectangles (_pad_pair_gap).
    NO refs are excluded: the previous _FINE_PITCH_REFS bypass only existed
    to absorb the half-diagonal approximation error, and with exact geometry
    the whole board passes with every ref measured.
    """
    print("\n── JLCDFM: Pad-to-Pad Spacing (0.15mm) ──")
    MIN_GAP = 0.15
    pads = _get_cache()["pads"]

    # Group by layer
    by_layer = {}
    for p in pads:
        by_layer.setdefault(p["layer"], []).append(p)

    violations = []
    for layer, lpads in by_layer.items():
        if "Cu" not in layer:
            continue
        n = len(lpads)
        for i in range(n):
            for j in range(i + 1, n):
                p1, p2 = lpads[i], lpads[j]
                if p1["net"] == p2["net"] or p1["net"] == 0 or p2["net"] == 0:
                    continue
                gap = _pad_pair_gap(p1, p2)
                if gap < MIN_GAP:
                    violations.append(
                        f"{layer}: {p1['ref']}[{p1['num']}] net{p1['net']} "
                        f"@({p1['x']:.2f},{p1['y']:.2f}) vs "
                        f"{p2['ref']}[{p2['num']}] net{p2['net']} "
                        f"@({p2['x']:.2f},{p2['y']:.2f}) "
                        f"gap={gap:.3f}mm"
                    )

    if violations:
        for v in violations[:20]:
            print(f"    VIOLATION: {v}")
        if len(violations) > 20:
            print(f"    ... and {len(violations) - 20} more")

    check(f"JLCDFM pad spacing >= {MIN_GAP}mm ({sum(len(v) for v in by_layer.values())} pads)",
          len(violations) == 0,
          f"{len(violations)} violations")


def test_jlcdfm_via_to_smd_clearance():
    """JLCDFM: Every via drill edge to nearest SMD pad edge (diff net) >= 0.15mm.

    Excludes vias near fine-pitch connector pads (J4 FPC) where power/GND vias
    must be placed within the 0.5mm pitch pad array — structural constraint.
    """
    print("\n── JLCDFM: Via-to-SMD Clearance (0.15mm) ──")
    import math
    MIN_CLR = 0.15
    vias = _cached_vias()
    pads = _get_cache()["pads"]

    # SMD pads only
    smd_pads = [p for p in pads if p.get("type") == "smd"]

    violations = []
    structural = 0
    for v in vias:
        vx, vy = v["x"], v["y"]
        drill_r = v["drill"] / 2.0
        v_net = v["net"]
        if v_net == 0:
            continue
        for p in smd_pads:
            if p["net"] == 0 or p["net"] == v_net:
                continue
            # Via is on F.Cu+B.Cu; check if pad layer matches
            if p["layer"] not in ("F.Cu", "B.Cu"):
                continue
            # Rectangular pad proximity: distance from via center to nearest
            # pad edge, minus drill radius.  Old circular method used pad diagonal
            # as radius, over-reporting violations for non-square pads.
            dx = max(0.0, abs(vx - p["x"]) - p["w"] / 2)
            dy = max(0.0, abs(vy - p["y"]) - p["h"] / 2)
            edge_dist = math.hypot(dx, dy)
            gap = edge_dist - drill_r
            if gap < MIN_CLR:
                # Structural: via near fine-pitch connector pad
                if p["ref"] in _FINE_PITCH_REFS:
                    structural += 1
                    continue
                violations.append(
                    f"via@({vx:.2f},{vy:.2f}) net{v_net} drill_r={drill_r:.2f} "
                    f"vs {p['ref']}[{p['num']}] net{p['net']} "
                    f"@({p['x']:.2f},{p['y']:.2f}) gap={gap:.3f}mm"
                )

    if violations:
        for v in violations[:20]:
            print(f"    VIOLATION: {v}")
        if len(violations) > 20:
            print(f"    ... and {len(violations) - 20} more")
    if structural:
        print(f"    (excluded {structural} structural fine-pitch via-pad pairs)")

    check(f"JLCDFM via-to-SMD >= {MIN_CLR}mm ({len(vias)} vias x {len(smd_pads)} SMD pads)",
          len(violations) == 0,
          f"{len(violations)} violations")


def test_jlcdfm_via_to_pad_clearance():
    """JLCDFM: Via annular ring edge to nearest pad edge (diff net) >= 0.10mm.

    Uses AABB distance (via circle to pad rectangle) for accurate gap calculation.
    Excludes vias near fine-pitch connector/IC pads (structural constraint).
    Also excludes vias near EP (exposed pad) of power ICs where thermal vias
    are intentionally placed close.
    """
    print("\n── JLCDFM: Via Annular Ring to Pad (0.10mm) ──")
    import math
    MIN_CLR = 0.10
    vias = _cached_vias()
    pads = _get_cache()["pads"]

    def _via_to_rect_gap(vx, vy, copper_r, px, py, pw, ph):
        """Distance from via copper circle edge to rectangular pad edge."""
        # Find closest point on rectangle to via center
        half_w, half_h = pw / 2.0, ph / 2.0
        cx = max(px - half_w, min(vx, px + half_w))
        cy = max(py - half_h, min(vy, py + half_h))
        dist = math.hypot(vx - cx, vy - cy)
        return dist - copper_r

    violations = []
    structural = 0
    for v in vias:
        vx, vy = v["x"], v["y"]
        copper_r = v["size"] / 2.0  # annular ring edge
        v_net = v["net"]
        if v_net == 0:
            continue
        for p in pads:
            if p["net"] == 0 or p["net"] == v_net:
                continue
            if p["layer"] not in ("F.Cu", "B.Cu"):
                continue
            gap = _via_to_rect_gap(vx, vy, copper_r, p["x"], p["y"], p["w"], p["h"])
            if gap < MIN_CLR:
                # Structural: via near fine-pitch pad or EP (exposed pad)
                if p["ref"] in _FINE_PITCH_REFS or p["num"] == "EP":
                    structural += 1
                    continue
                violations.append(
                    f"via@({vx:.2f},{vy:.2f}) net{v_net} copper_r={copper_r:.2f} "
                    f"vs {p['ref']}[{p['num']}] net{p['net']} "
                    f"@({p['x']:.2f},{p['y']:.2f}) gap={gap:.3f}mm"
                )

    if violations:
        for v in violations[:20]:
            print(f"    VIOLATION: {v}")
        if len(violations) > 20:
            print(f"    ... and {len(violations) - 20} more")
    if structural:
        print(f"    (excluded {structural} structural fine-pitch/EP via-pad pairs)")

    check(f"JLCDFM via ring-to-pad >= {MIN_CLR}mm ({len(vias)} vias x {len(pads)} pads)",
          len(violations) == 0,
          f"{len(violations)} violations")


def test_jlcdfm_pth_to_trace_clearance():
    """JLCDFM: Every PTH drill edge to nearest trace (diff net) >= 0.15mm.

    Excludes PTH pads on fine-pitch connectors (J1 USB-C shield legs) where
    traces must cross under the connector body — structural constraint.
    """
    print("\n── JLCDFM: PTH-to-Trace Clearance (0.15mm) ──")
    MIN_CLR = 0.15
    segs = _cached_segments()
    pads = _get_cache()["pads"]

    # Collect PTH pads (thru_hole only, not np_thru_hole which have no copper)
    pth_pads = []
    seen = set()
    for p in pads:
        if p.get("type") != "thru_hole":
            continue
        if p.get("drill", 0) <= 0:
            continue
        key = (round(p["x"], 3), round(p["y"], 3))
        if key in seen:
            continue
        seen.add(key)
        pth_pads.append(p)

    segs_by_layer = {}
    for s in segs:
        segs_by_layer.setdefault(s["layer"], []).append(s)

    violations = []
    structural = 0
    for p in pth_pads:
        px, py = p["x"], p["y"]
        drill_r = p["drill"] / 2.0
        p_net = p["net"]
        for layer in ("F.Cu", "B.Cu"):
            for s in segs_by_layer.get(layer, []):
                if p_net != 0 and s["net"] != 0 and p_net == s["net"]:
                    continue
                dist = _point_to_segment_dist(px, py, s)
                gap = dist - drill_r - s.get("width", s.get("w", 0)) / 2.0
                if gap < MIN_CLR:
                    # Structural: USB-C shield PTH legs (traces cross under connector)
                    if p["ref"] in _FINE_PITCH_REFS:
                        structural += 1
                        continue
                    violations.append(
                        f"{p['ref']}[{p['num']}] @({px:.2f},{py:.2f}) "
                        f"drill_r={drill_r:.2f} net{p_net} vs "
                        f"{layer} net{s['net']} gap={gap:.3f}mm"
                    )

    if violations:
        for v in violations[:15]:
            print(f"    VIOLATION: {v}")
        if len(violations) > 15:
            print(f"    ... and {len(violations) - 15} more")
    if structural:
        print(f"    (excluded {structural} structural USB-C shield leg crossings)")

    check(f"JLCDFM PTH-to-trace >= {MIN_CLR}mm ({len(pth_pads)} PTH pads)",
          len(violations) == 0,
          f"{len(violations)} violations")


def test_jlcdfm_fiducial_present():
    """JLCDFM: Board fiducial marks (optional — JLCPCB uses panel fiducials)."""
    print("\n── JLCDFM: Fiducial Marks ──")
    refs = _get_cache()["refs"]
    fid_refs = [r for r in refs if r.startswith("FID")]
    with open(PCB_FILE) as f:
        content = f.read()
    fid_fps = len(re.findall(r'\(footprint "Fiducial"', content))
    n = max(fid_fps, len(fid_refs))
    # Board fiducials are optional — JLCPCB uses panel-level fiducials.
    check(f"Fiducial marks: {n} present (panel fiducials used if 0)", True)


def test_jlcdfm_via_in_pad():
    """JLCDFM: No via drill center falls inside a component pad (different net).

    Via-in-pad on same net is acceptable (intentional connections).
    Via-in-pad on different net is a manufacturing defect / short risk.
    """
    print("\n── JLCDFM: Via-in-Pad Check ──")
    import math
    vias = _cached_vias()
    pads = _get_cache()["pads"]

    # Only SMD pads (THT pads already have holes, not relevant)
    smd_pads = [p for p in pads if p.get("type") == "smd"]

    violations = []
    for v in vias:
        vx, vy = v["x"], v["y"]
        v_net = v["net"]
        for p in smd_pads:
            if p["net"] == v_net:
                continue  # same net = intentional via-in-pad
            if p["net"] == 0 or v_net == 0:
                continue
            # Check if via center is within pad rectangle
            # (conservative: use half-width/half-height as rectangular extent)
            dx = abs(vx - p["x"])
            dy = abs(vy - p["y"])
            if dx <= p["w"] / 2.0 and dy <= p["h"] / 2.0:
                violations.append(
                    f"via@({vx:.2f},{vy:.2f}) net{v_net} inside "
                    f"{p['ref']}[{p['num']}] net{p['net']} "
                    f"@({p['x']:.2f},{p['y']:.2f}) size=({p['w']:.2f}x{p['h']:.2f})"
                )

    if violations:
        for v in violations[:10]:
            print(f"    VIOLATION: {v}")

    check(f"JLCDFM no different-net via-in-pad ({len(vias)} vias x {len(smd_pads)} SMD pads)",
          len(violations) == 0,
          f"{len(violations)} violations")


def test_jlcdfm_trace_to_board_edge():
    """JLCDFM: Every trace segment endpoint at least 0.2mm from board edge."""
    print("\n── JLCDFM: Trace-to-Board-Edge (0.2mm) ──")
    MIN_DIST = 0.2
    segs = _cached_segments()

    violations = []
    for s in segs:
        w = s.get("width", s.get("w", 0))
        half_w = w / 2.0
        for px, py in [(s["x1"], s["y1"]), (s["x2"], s["y2"])]:
            center_dist = _board_edge_distance(px, py)
            edge_dist = center_dist - half_w
            if edge_dist < MIN_DIST:
                violations.append(
                    f"{s['layer']}: ({px:.2f},{py:.2f}) w={w:.2f} "
                    f"edge_dist={edge_dist:.3f}mm"
                )

    if violations:
        for v in violations[:20]:
            print(f"    VIOLATION: {v}")
        if len(violations) > 20:
            print(f"    ... and {len(violations) - 20} more")

    check(f"JLCDFM trace-to-edge >= {MIN_DIST}mm ({len(segs)} segments)",
          len(violations) == 0,
          f"{len(violations)} violations")
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
