pjcau/esp32-emu-turbo/scripts/verify_enclosure_stl.py

#!/usr/bin/env python3
"""The OTHER road: measure the exported STLs, not the scad.

The three enclosure gates read enclosure.scad's constants and trust
OpenSCAD to turn them into geometry. This gate starts from the files that
go to the printer — 3d_case/*.stl (+ hardware/enclosure/reference/) — cuts
them with OpenSCAD `import()` + `projection(cut=true)` at chosen heights,
measures every hole, ring and pocket in the slice, and compares against
sources that are NOT the scad: board.py placements (switches, LEDs, mount
holes, J3), the panel and insert datasheets, the measured cell and the
user's requirements. If a constant, a module or the exporter is wrong,
the numbers here disagree with the design numbers; agreement is the
"does it add up" the user asked for.

Checks (S = STL)
  S0  the viewer shows the print files: each 3d_case/*.stl, moved by
      viewer/placement.json (pure rotation + offset), lands exactly on the
      scad assembly copy in hardware/enclosure/reference/
  S1  shell envelopes: top 170 x 85 x 10.6, bottom 170 x 85 x 18 (with lip)
  S2  front-face cutouts vs board placements: 4 ABXY circles (Ø >= 9),
      D-pad cross (24 x 24, arms >= 6.5), Start/Select/Menu pills, six LED
      light pipes — each centred on its switch/LED within 0.15 mm
  S3  viewport = panel active area + 0.6 (datasheet 83.52 x 55.68), y = 2
  S4  glass pocket (frame walls) = outline 60.88 + 0.6 in Y; equal gaps to
      the Select and Y cap bodies (>= 0.4)
  S5  top bosses at the 4 corner mount holes: socket Ø3.1 (insert OD 3.5
      - 0.4) in the last 4.5 mm (insert L 4.0 + 0.5), relief Ø2.8 above,
      boss Ø7.2 (>= 2 mm wall), front wall closed
  S6  bottom: counterbores Ø5 on the mount holes; columns with a Ø2.8
      bore; contact half-column keeps off SW11/SW12 (x >= 68.55 at Z 15.5)
  S7  battery pocket >= 95 x 50 (measured cell 90 x 50 + 5 leads), not over
      J3 (JST y <= -20.7); strap posts present
  S8  V3 edge openings measured in the walls: L/R cap windows in the +Y
      wall (14.3 wide, open to the split), the power slider slot (6 wide)
      and the USB-C recess (2 deep) and SD slit (16 wide) in the -Y wall
  S9  speaker grille centroid in -X/+Y (player's left, D-pad side)
  S10 parts: every cap centred on its switch (viewer STL bbox), height
      9.3 (2 mm proud); L/R caps 2.5 proud of the +Y face at Z 8..16;
      L/R levers: arm top 14.3 (TS-1187A tip - 0.2), end edge on the
      SW11/SW12 centre line from board.py, bump 0..0.1 behind the flange;
      slider 1 proud of the -Y face, tab to Z 17.4; straps 5 x 1.2
      outside the ESP32 footprint; display part 94.57 x 60.88 x 3.9 with
      its top at the ceiling (Z 24.6)
  S11 thin walls on the STL slices themselves: erode/dilate by 0.6
  S12 solidity: every print STL is watertight (vertices merged within a
      tolerance, every edge then used by exactly two triangles in
      opposite directions), exactly one connected body, volume > 0 — a
      mesh property, not a dimension; a CSG operand exactly coincident or
      tangent with another leaves zero-volume degenerate sheets that the
      other S-checks (which measure cut profiles, not mesh closure) don't
      see. numpy only (no trimesh — this runs under the system python3).
  S13 top-boss gussets: at each boss's 8 rib angles (all around, every
      45 deg), a point at radius boss_r + reach/2 (5.1, or 4.3 for the
      one rib shortened for Menu-cap clearance) is material at z=2.3
      (near the root) and empty at z=8.7 (past where even the tallest
      rib ends at 8.5, the boss tip minus 0.5) — the ribs are on the mesh, not only
      claimed by the scad's own constants

Exit codes: 0 pass · 1 mismatch · 2 cannot evaluate (Docker, files).
"""

from __future__ import annotations

import math
import os
import re
import shutil
import subprocess
import sys
from pathlib import Path

import numpy as np

BASE = Path(__file__).resolve().parent.parent
sys.path.insert(0, str(BASE))
OUT_DIR = BASE / "website" / "static" / "img" / "renders"      # docker /output
WORK = OUT_DIR / "_stlcheck"
CASE = BASE / "3d_case"
REF = BASE / "hardware" / "enclosure" / "reference"   # scad assembly copies
PARTS = CASE / "viewer" / "parts"                        # display, pcb

TOL_POS = 0.15
MIN_WALL = 1.2
PANEL_ACTIVE = (83.52, 55.68)       # vendor spec (datasheet image)
PANEL_OUTLINE = (94.57, 60.88, 3.90)
INSERT = (3.5, 4.0)                 # HANGLIFE M2.5 x D3.5 x L4
MEASURED_CELL = (90.0, 50.0, 10.0)


class Structural(RuntimeError):
    pass


# ── geometry helpers ─────────────────────────────────────────────────────

def stl_vertices(path: Path):
    for line in path.read_text().splitlines():
        s = line.strip()
        if s.startswith("vertex"):
            yield tuple(float(v) for v in s.split()[1:4])


def bbox(path: Path):
    xs, ys, zs = zip(*stl_vertices(path))
    return (min(xs), max(xs), min(ys), max(ys), min(zs), max(zs))


MERGE_TOL = 1e-4   # mm — vertex-merge grid for the S12 solidity check


def mesh_solidity(path: Path, merge_tol: float = MERGE_TOL) -> dict:
    """Watertight / single-body / positive-volume, numpy only.

    Raw STL carries no shared vertex indices: every triangle writes its
    own copy of each corner, so two triangles meeting at the "same" point
    only test as equal once rounded onto a tolerance grid first — skip
    that and every triangle looks like its own disconnected body. Once
    merged: every undirected edge must be used by exactly two triangles,
    once in each direction (consistent winding, and no exact duplicate
    face); the mesh must be a single connected component (union-find over
    shared vertices); its signed volume (divergence theorem, raw
    unmerged coordinates) must be positive and non-trivial.
    """
    verts = list(stl_vertices(path))
    if not verts or len(verts) % 3 != 0:
        return dict(watertight=False, bodies=0, bad_edges=-1, volume=0.0, n_faces=0)
    tris = np.array(verts, dtype=float).reshape(-1, 3, 3)
    flat = tris.reshape(-1, 3)
    keys = np.round(flat / merge_tol).astype(np.int64)
    _, inv = np.unique(keys, axis=0, return_inverse=True)
    idx = inv.reshape(-1, 3)

    edges: dict[tuple[int, int], list[tuple[int, int]]] = {}
    for a, b, c in idx:
        for u, v in ((a, b), (b, c), (c, a)):
            key = (int(u), int(v)) if u < v else (int(v), int(u))
            edges.setdefault(key, []).append((int(u), int(v)))
    bad_edges = sum(1 for d in edges.values() if len(d) != 2 or d[0] == d[1])

    n_verts = int(idx.max()) + 1
    parent = list(range(n_verts))

    def find(x):
        while parent[x] != x:
            parent[x] = parent[parent[x]]
            x = parent[x]
        return x

    for a, b, c in idx:
        a, b, c = int(a), int(b), int(c)
        ra, rb, rc = find(a), find(b), find(c)
        if ra != rb:
            parent[ra] = rb
        rb = find(b)
        if rb != rc:
            parent[rb] = rc
    roots = {find(v) for tri in idx for v in tri}

    v0, v1, v2 = tris[:, 0], tris[:, 1], tris[:, 2]
    volume = abs(float(np.sum(np.einsum("ij,ij->i", v0, np.cross(v1, v2))))) / 6.0

    return dict(watertight=bad_edges == 0, bodies=len(roots),
                bad_edges=bad_edges, volume=volume, n_faces=len(idx))


_CALLS = [0]


def openscad(scad_text: str, out_name: str, **defs) -> Path:
    """One OpenSCAD run in the container. Every call writes a NEW output
    name: re-using one name means unlinking it just before the container
    opens it, and on the OrbStack bind mount that race shows up as
    "Can't open file for export" (seen 2026-10-08 on the S11 slices)."""
    WORK.mkdir(parents=True, exist_ok=True)
    scad = WORK / "slice.scad"
    if not scad.exists() or scad.read_text() != scad_text:
        scad.write_text(scad_text)
    _CALLS[0] += 1
    out_name = f"{_CALLS[0]:04d}_{out_name}"
    out = WORK / out_name
    cmd = ["docker", "compose", "-f", str(BASE / "docker-compose.yml"), "run",
           "--rm", "--user", f"{os.getuid()}:{os.getgid()}", "openscad",
           "-o", f"/output/_stlcheck/{out_name}"]
    for k, v in defs.items():
        cmd += ["-D", f"{k}={v}"]
    cmd.append("/output/_stlcheck/slice.scad")
    try:
        r = subprocess.run(cmd, capture_output=True, text=True, timeout=600)
    except (OSError, subprocess.TimeoutExpired) as e:
        raise Structural(f"cannot run the OpenSCAD container: {e}")
    if r.returncode != 0 or not out.exists():
        raise Structural("OpenSCAD failed:\n" + (r.stderr or r.stdout)[-1500:])
    return out


SLICE_SCAD = """
zc = 0; thin = 0; src = "/output/_stlcheck/part.stl";
module m() { projection(cut=true) translate([0, 0, -zc]) import(src); }
if (thin == 0) m();
else intersection() { m(); difference() { m(); offset(r=0.58) offset(r=-0.58) m(); } }
"""


def slice_svg(stl: Path, z: float, thin: bool = False):
    WORK.mkdir(parents=True, exist_ok=True)
    part = WORK / f"part_{stl.stem}.stl"      # one copy per source, never rewritten
    if not part.exists() or part.read_bytes() != stl.read_bytes():
        shutil.copy(stl, part)
    svg = openscad(SLICE_SCAD, "slice.svg", zc=z, thin=1 if thin else 0,
                   src=f'"/output/_stlcheck/{part.name}"')
    cs = contours(svg)
    svg.unlink(missing_ok=True)
    return cs


def front_view(cs):
    """Print-frame slice of the top shell -> assembly XY.

    The top prints face-down, i.e. the assembly copy turned 180° about X,
    so assembly (x, y) sits at print (x, -y). Measuring the print file
    directly in assembly XY (as this gate did before 2026-09-23) only
    passes on the MIRROR IMAGE of the top — which is what got printed."""
    out = []
    for pts, area, bb, depth in cs:
        out.append(([(x, -y) for x, y in pts], area,
                    (bb[0], bb[1], -bb[3], -bb[2]), depth))
    return out


def contours(svg: Path):
    """[(pts, area, bbox, depth)] — depth odd = hole."""
    txt = svg.read_text()
    polys = []
    for d in re.findall(r'd="([^"]+)"', txt):
        for sub in re.findall(r"M([^Mz]+)z", d):
            pts = [(float(a), -float(b)) for a, b in
                   re.findall(r"(-?[\d.]+),(-?[\d.]+)", sub)]
            if len(pts) < 3:
                continue
            a = 0.0
            for i in range(len(pts)):
                x1, y1 = pts[i]
                x2, y2 = pts[(i + 1) % len(pts)]
                a += x1 * y2 - x2 * y1
            xs = [p[0] for p in pts]
            ys = [p[1] for p in pts]
            polys.append([pts, abs(a) / 2, (min(xs), max(xs), min(ys), max(ys))])

    def inside(pt, poly):
        x, y = pt
        n = len(poly)
        c = False
        for i in range(n):
            x1, y1 = poly[i]
            x2, y2 = poly[(i + 1) % n]
            if (y1 > y) != (y2 > y) and x < (x2 - x1) * (y - y1) / (y2 - y1) + x1:
                c = not c
        return c

    out = []
    for i, (pts, area, bb) in enumerate(polys):
        depth = sum(1 for j, (p2, a2, b2) in enumerate(polys)
                    if j != i and a2 > area and inside(pts[0], p2))
        out.append((pts, area, bb, depth))
    return out


def holes(cs):
    return [c for c in cs if c[3] % 2 == 1]


def solids(cs):
    return [c for c in cs if c[3] % 2 == 0]


def near(cs, x, y, r=1.5):
    """contours whose bbox centre lies within r of (x, y)"""
    return [c for c in cs
            if math.hypot((c[2][0] + c[2][1]) / 2 - x, (c[2][2] + c[2][3]) / 2 - y) <= r]


def size(c):
    return c[2][1] - c[2][0], c[2][3] - c[2][2]


def centre(c):
    return (c[2][0] + c[2][1]) / 2, (c[2][2] + c[2][3]) / 2


def first_material(cs, x0, y0, dx, dy, maxd, step=0.05):
    """distance from (x0,y0) along (dx,dy) to the first point in material"""
    d = 0.0
    while d <= maxd:
        if point_in_material(cs, x0 + dx * d, y0 + dy * d):
            return d
        d += step
    return float("nan")


def point_in_material(cs, x, y):
    n = 0
    for pts, _a, _b, _d in cs:
        c = False
        for i in range(len(pts)):
            x1, y1 = pts[i]
            x2, y2 = pts[(i + 1) % len(pts)]
            if (y1 > y) != (y2 > y) and x < (x2 - x1) * (y - y1) / (y2 - y1) + x1:
                c = not c
        n += c
    return n % 2 == 1


# ── main ─────────────────────────────────────────────────────────────────

def main() -> int:
    print("=" * 72)
    print("ENCLOSURE STL AUDIT — measured from 3d_case/*.stl, compared with board.py,")
    print("datasheets and the user's requirements (no enclosure.scad constants)")
    print("=" * 72)
    try:
        from scripts.generate_pcb import board as B
        from scripts import generate_enclosure_pcb as GEP
    except Exception as e:
        raise Structural(f"cannot import board sources: {e}")
    parts = GEP.parts()
    P = {r[0]: r for r in parts}
    scad_mtime = max(p.stat().st_mtime for p in
                     (BASE / "hardware" / "enclosure").glob("*.scad"))
    for f in ("case_top.stl", "case_bottom.stl", "lr_cap_x2.stl", "power_slider.stl",
              "lr_lever_l.stl", "lr_lever_r.stl",
              "battery_strap_x2.stl", "viewer/parts/part_display.stl"):
        if not (CASE / f).exists():
            raise Structural(f"3d_case/{f} missing — run make export-enclosure-stl")
        if (CASE / f).stat().st_mtime < scad_mtime:
            raise Structural(f"3d_case/{f} is older than the scad sources — "
                             "run make export-enclosure-stl first")
    results = []

    def check(code, name, ok, detail):
        results.append(ok)
        print(f"  {'PASS' if ok else 'FAIL'}  {code} {name}: {detail}")

    top, bot = CASE / "case_top.stl", CASE / "case_bottom.stl"

    def top_slice(z):
        return front_view(slice_svg(top, z))

    # S0 the viewer shows the print files: every 3d_case/*.stl instance,
    # placed by viewer/placement.json (what viewer.html applies), must be a
    # rotation (det +1) and reproduce the scad assembly reference exactly
    import json
    from scripts import enclosure_placement as EP
    pj = CASE / "viewer" / "placement.json"
    if not pj.exists() or pj.stat().st_mtime < scad_mtime:
        raise Structural("3d_case/viewer/placement.json missing or stale — "
                         "run make export-enclosure-stl")
    shipped = json.loads(pj.read_text())
    bad = [f"{p['file']}: det {EP.det(p['rot'])}" for p in shipped if EP.det(p["rot"]) != 1]
    fresh = EP.compute()
    def norm(ps):
        return [(p["file"], json.dumps(p["rot"]), json.dumps(list(p["t"]))) for p in ps]
    if norm(fresh) != norm(shipped):
        bad.append("placement.json differs from the print files — regenerate it")
    for rf, frac, extra in EP.check([dict(p, t=tuple(p["t"]), ref=f["ref"])
                                     for p, f in zip(shipped, fresh)]):
        if frac < 0.999 or extra:
            bad.append(f"{rf}: {frac:.1%} reproduced, {extra} vertices elsewhere")
    printed = {f.name for f in CASE.glob("*.stl")}
    unplaced = printed - {p["file"] for p in shipped}
    if unplaced:
        bad.append(f"print files the viewer never shows: {sorted(unplaced)}")
    check("S0", "viewer-shows-the-print-files",
          not bad,
          f"{len(shipped)} placed instances of {len(printed)} print files, all pure "
          "rotations, each lands exactly on the design's assembly position"
          + (": " + "; ".join(bad) if bad else ""))

    # S1 envelopes
    bt, bb_ = bbox(top), bbox(bot)
    tw, th, td = bt[1] - bt[0], bt[3] - bt[2], bt[5] - bt[4]
    bw, bh, bd = bb_[1] - bb_[0], bb_[3] - bb_[2], bb_[5] - bb_[4]
    # top: 2 front wall + 7.0 display stack + 1.6 PCB = 10.6, plus the 0.6 mm
    # cosmetic bezel proud of the face; bottom: 16 to the split + 2 mm lip
    check("S1", "shell-envelopes",
          abs(tw - 170) < 0.05 and abs(th - 85) < 0.05 and abs(td - 11.2) < 0.05
          and abs(bw - 170) < 0.05 and abs(bh - 85) < 0.05 and abs(bd - 18) < 0.05,
          f"top {tw:.2f}x{th:.2f}x{td:.2f} (want 170x85x11.2: 2 wall + 7.0 "
          f"stack + 1.6 PCB + 0.6 bezel), bottom {bw:.2f}x{bh:.2f}x{bd:.2f} "
          f"(want 170x85x18: 16 + 2 lip)")

    # S2 front face cutouts (slice through the front wall)
    face = top_slice(1.0)
    fh = holes(face)
    bad = []
    sw_pos = {r: (P[r][1], P[r][2]) for r in P if r.startswith("SW") and P[r][4] == "top"}
    abxy = {"A": "SW5", "B": "SW6", "X": "SW7", "Y": "SW8"}
    for name, ref in abxy.items():
        x, y = sw_pos[ref]
        h = near(fh, x, y, 1.0)
        if len(h) != 1:
            bad.append(f"{name}: {len(h)} holes at {ref}")
            continue
        w, hh = size(h[0])
        cx, cy = centre(h[0])
        if abs(w - hh) > 0.1 or w < 9 - 0.05 or math.hypot(cx - x, cy - y) > TOL_POS:
            bad.append(f"{name}: Ø{w:.2f}x{hh:.2f} at ({cx:.2f},{cy:.2f}) vs {ref} ({x},{y})")
    dx, dy = B.DPAD_ENC
    h = near(fh, dx, dy, 1.0)
    if len(h) != 1:
        bad.append(f"D-pad: {len(h)} holes")
    else:
        w, hh = size(h[0])
        # arm width = the narrow dimension of the cross: sample the contour
        pts = h[0][0]
        arm = max(p[1] for p in pts if abs(p[0] - dx) > 9) - \
            min(p[1] for p in pts if abs(p[0] - dx) > 9)
        cx, cy = centre(h[0])
        if abs(w - 24) > 0.1 or abs(hh - 24) > 0.1 or arm < 6.5 - 0.05 \
                or math.hypot(cx - dx, cy - dy) > TOL_POS:
            bad.append(f"D-pad {w:.2f}x{hh:.2f} arms {arm:.2f} at ({cx:.2f},{cy:.2f})")
    for name, ref, wmin, hmin in (("Start", "SW9", 10, 5), ("Select", "SW10", 10, 5),
                                  ("Menu", "SW13", 12, 3.8)):
        x, y = sw_pos[ref]
        h = near(fh, x, y, 1.0)
        if len(h) != 1:
            bad.append(f"{name}: {len(h)} holes")
            continue
        w, hh = size(h[0])
        cx, cy = centre(h[0])
        if w < wmin - 0.05 or hh < hmin - 0.05 or math.hypot(cx - x, cy - y) > TOL_POS:
            bad.append(f"{name} {w:.2f}x{hh:.2f} at ({cx:.2f},{cy:.2f}) vs ({x},{y})")
    for n in range(1, 7):
        x, y = P[f"LED{n}"][1], P[f"LED{n}"][2]
        h = near(fh, x, y, 1.0)
        if len(h) != 1:
            bad.append(f"LED{n}: {len(h)} holes")
            continue
        w, hh = size(h[0])
        want = 2.0 if n <= 2 else 1.2
        if abs(w - want) > 0.1 or math.hypot(*[a - b for a, b in zip(centre(h[0]), (x, y))]) > TOL_POS:
            bad.append(f"LED{n} Ø{w:.2f} (want {want})")
    check("S2", "front-cutouts-vs-board",
          not bad,
          f"{len(fh)} holes in the front wall; ABXY/D-pad/Start/Select/Menu/LED1-6 "
          "on their placements" + (": " + "; ".join(bad) if bad else ""))

    # S3 viewport
    big = max(fh, key=lambda c: c[1])
    vw, vh = size(big)
    vcx, vcy = centre(big)
    check("S3", "viewport-is-active-area",
          abs(vw - PANEL_ACTIVE[0] - 0.6) < 0.1 and abs(vh - PANEL_ACTIVE[1] - 0.6) < 0.1
          and abs(vcy - B.DISPLAY_ENC[1]) < 0.1,
          f"viewport {vw:.2f}x{vh:.2f} at ({vcx:.2f},{vcy:.2f}) vs active "
          f"{PANEL_ACTIVE[0]}x{PANEL_ACTIVE[1]} + 0.6, y {B.DISPLAY_ENC[1]}")

    # S4 glass pocket: scan from the centre of the viewport to the frame's
    # inner faces (Y both ways at x = 0; +X at y = 20 hits the stub; the
    # tail side is open, so the -X edge follows from the outline length)
    mid = top_slice(6.0)
    up = first_material(mid, 0, 2, 0, 1, 45)
    dn = first_material(mid, 0, 2, 0, -1, 45)
    pocket_h = up + dn
    px1 = first_material(mid, 0, 20, 1, 0, 80)
    sel_hole = near(fh, *sw_pos["SW10"], 1.0)[0]
    y_hole = near(fh, *sw_pos["SW8"], 1.0)[0]
    sel_body_edge = sel_hole[2][1] - 0.3
    y_body_edge = y_hole[2][0] + 0.3
    gap_r = y_body_edge - px1
    px0 = px1 - (PANEL_OUTLINE[0] + 0.6)
    gap_l = px0 - sel_body_edge
    check("S4", "glass-pocket",
          abs(pocket_h - PANEL_OUTLINE[1] - 0.6) < 0.1 and gap_r >= 0.4
          and gap_l >= 0.4 and abs(gap_l - gap_r) < 0.1,
          f"frame inner span Y {pocket_h:.2f} (want {PANEL_OUTLINE[1]} + 0.6); "
          f"pocket x[{px0:.2f}, {px1:.2f}] ({PANEL_OUTLINE[0]} + 0.6); gap to the "
          f"Y cap body {gap_r:.2f}, to the Select cap body {gap_l:.2f} (equal, >= 0.4)")

    # S5 top bosses: slices at 0.4 above the boss end (8.6) and inside the relief (3.0)
    end = top_slice(8.8)      # 0.2 below the boss end (9.0 = PCB top face)
    rel = top_slice(3.0)
    face0 = top_slice(1.0)
    corners = [(x, y) for x, y in B.MOUNT_HOLES_ENC if abs(x) > 50]
    bad = []
    for x, y in corners:
        sock = near(holes(end), x, y, 0.5)
        ring = near(solids(end), x, y, 0.5)
        r_rel = near(holes(rel), x, y, 0.5)
        f = near(holes(face0), x, y, 3.0)
        if len(sock) != 1 or len(ring) != 1 or len(r_rel) != 1 or f:
            bad.append(f"({x},{y}): socket {len(sock)} ring {len(ring)} relief {len(r_rel)} face-holes {len(f)}")
            continue
        ds, dr, dq = size(sock[0])[0], size(ring[0])[0], size(r_rel[0])[0]
        wall = (dr - ds) / 2
        if abs(ds - (INSERT[0] - 0.4)) > 0.08 or wall < 2.0 - 0.05 or abs(dq - 2.8) > 0.08:
            bad.append(f"({x},{y}): socket Ø{ds:.2f} ring Ø{dr:.2f} wall {wall:.2f} relief Ø{dq:.2f}")
    # socket depth: the socket Ø must still be present at 4.4 below the end and gone at 4.6
    d1 = near(holes(top_slice(9.0 - 4.4)), *corners[0], 0.5)
    d2 = near(holes(top_slice(9.0 - 4.6)), *corners[0], 0.5)
    depth_ok = d1 and abs(size(d1[0])[0] - 3.1) < 0.08 and d2 and abs(size(d2[0])[0] - 2.8) < 0.08
    check("S5", "insert-bosses",
          not bad and depth_ok,
          f"4 corner bosses: socket Ø3.1 for OD {INSERT[0]} x L {INSERT[1]} insert, "
          f">= 2 mm wall, Ø2.8 relief, socket depth 4.5 (3.1 at -4.4, 2.8 at -4.6: "
          f"{'ok' if depth_ok else 'WRONG'}), front face closed"
          + (": " + "; ".join(bad) if bad else ""))

    # S6 bottom counterbores, bores, half-columns
    fl = slice_svg(bot, 1.0)
    col = slice_svg(bot, 8.0)
    half = slice_svg(bot, 15.5)
    bad = []
    for x, y in corners:
        cb = near(holes(fl), x, y, 0.5)
        bore = near(holes(col), x, y, 0.5)
        if len(cb) != 1 or abs(size(cb[0])[0] - 5.0) > 0.1:
            bad.append(f"counterbore at ({x},{y}): {[size(c)[0] for c in cb]}")
        if len(bore) != 1 or abs(size(bore[0])[0] - 2.8) > 0.1:
            bad.append(f"bore at ({x},{y}): {[size(c)[0] for c in bore]}")
        inner = x - 1.5 * (1 if x > 0 else -1)
        if point_in_material(half, inner, y) or not point_in_material(half, x + 2.2 * (1 if x > 0 else -1), y):
            bad.append(f"half-column at ({x},{y}): material at x={inner} or none at outer side")
    sw11 = P["SW11"]
    check("S6", "bottom-columns",
          not bad,
          f"counterbores Ø5, bores Ø2.8, contact half-columns open toward the board "
          f"centre (SW11/SW12 body edge {abs(sw11[1]) + 2.55:.2f}, pads to 68.25)"
          + (": " + "; ".join(bad) if bad else ""))

    # S7 pocket: the border ring is open at the lead notch and the hinge
    # corners, so scan from the pocket centre to its inner faces at Z 8
    j3 = P["J3"]
    j3_ymax = j3[2] + 8.6 / 2
    cxp, cyp = -1.5, 5.0                 # anywhere inside the pocket
    xl = first_material(col, cxp, cyp, -1, 0, 60)
    xr = first_material(col, cxp, cyp, 1, 0, 60)
    yd = first_material(col, cxp, cyp, 0, -1, 40)
    yu = first_material(col, cxp, cyp, 0, 1, 40)
    pw, ph = xl + xr, yd + yu
    y0 = cyp - yd
    posts = [c for c in holes(slice_svg(bot, 10.5))
             if 2.5 < size(c)[0] < 2.9 and 2.5 < size(c)[1] < 2.9
             and abs(centre(c)[0]) < 60]          # not the corner screw bores
    check("S7", "battery-pocket",
          pw >= MEASURED_CELL[0] + 5 - 0.1 and ph >= MEASURED_CELL[1] - 0.1
          and y0 >= j3_ymax - 1e-6 and len(posts) == 4,
          f"pocket {pw:.2f}x{ph:.2f} (measured cell {MEASURED_CELL[0]}x{MEASURED_CELL[1]} "
          f"+ 5 leads), bottom edge y={y0:.2f} vs J3 top {j3_ymax:.2f}, "
          f"{len(posts)} strap peg holes")

    # S8 V3 edge openings, measured in wall slices
    bad = []
    mid = slice_svg(bot, 12.0)            # L/R cap axis
    for sgn in (-1, 1):
        x = 57.5 * sgn
        if point_in_material(mid, x, 41.2):
            bad.append(f"no L/R window at x={x}")
            continue
        wl = first_material(mid, x, 41.2, -1, 0, 20)
        wr = first_material(mid, x, 41.2, 1, 0, 20)
        if abs(wl + wr - 14.3) > 0.15:
            bad.append(f"L/R window at x={x}: {wl + wr:.2f} wide (want 14.3)")
    top_z = slice_svg(bot, 15.9)          # just under the split: still open
    if point_in_material(top_z, 57.5, 41.2) or point_in_material(top_z, -57.5, 41.2):
        bad.append("L/R window closed before the split")
    pw = slice_svg(bot, 14.0)
    if point_in_material(pw, -40, -41.2):
        bad.append("no power slider slot")
    else:
        sw_ = first_material(pw, -40, -41.2, -1, 0, 10) + first_material(pw, -40, -41.2, 1, 0, 10)
        if abs(sw_ - 6.0) > 0.15:
            bad.append(f"slider slot {sw_:.2f} wide (want 6)")
    # the slider guide at Z 12: channel (air) 1.3 inside the wall face, lip
    # in front of it, end stops 12.2 apart
    gd = slice_svg(bot, 12.0)
    if point_in_material(gd, -40, -39.3) or not point_in_material(gd, -40, -38.0):
        bad.append("slider guide: no channel/lip at Z 12")
    else:
        cl = first_material(gd, -40, -39.3, -1, 0, 12) + first_material(gd, -40, -39.3, 1, 0, 12)
        if abs(cl - 12.2) > 0.15:
            bad.append(f"slider guide channel {cl:.2f} long (want 12.2)")
    usb = slice_svg(bot, 14.4)
    d_rec = first_material(usb, 7.5, -45, 0, 1, 10)     # inside the recess, outside the opening
    d_face = first_material(usb, 25, -45, 0, 1, 10)     # plain wall
    if not (abs(d_face - 2.5) < 0.1 and abs(d_rec - d_face - 2.0) < 0.1):
        bad.append(f"USB-C recess: face at {d_face:.2f}, recess floor at {d_rec:.2f} (want +2.0)")
    # SD: the V2.1 16 x 3.5 slit through the wall (the V3 20 mm window
    # was reverted by the user 2026-10-08) — measure its width
    sdw = slice_svg(bot, 14.2)
    if any(point_in_material(sdw, 60, y) for y in (-42.3, -41, -40.2)):
        bad.append("SD slit not open through the wall at Z 14.2")
    else:
        sw_sd = first_material(sdw, 60, -41, -1, 0, 15) + first_material(sdw, 60, -41, 1, 0, 15)
        if abs(sw_sd - 16.0) > 0.15:
            bad.append(f"SD slit {sw_sd:.2f} wide (want the V2.1 16)")
    check("S8", "edge-openings", not bad,
          "L/R windows 14.3 wide open to the split, slider slot 6 + guide channel 12.2, "
          "USB-C recess 2 deep, SD slit 16 through the wall" + (": " + "; ".join(bad) if bad else ""))

    # S9 grille
    small = [c for c in holes(fl) if size(c)[0] < 2]
    gx = sum(centre(c)[0] for c in small) / len(small) if small else 0
    gy = sum(centre(c)[1] for c in small) / len(small) if small else 0
    check("S9", "speaker-grille", len(small) >= 20 and gx < -40 and gy > 0,
          f"{len(small)} grille holes, centroid ({gx:.1f},{gy:.1f}) — -X/+Y = the player's left")

    # S10 parts
    bad = []
    capmap = {"part_btn_a": "SW5", "part_btn_b": "SW6", "part_btn_x": "SW7",
              "part_btn_y": "SW8", "part_start": "SW9", "part_select": "SW10",
              "part_menu": "SW13"}
    for fn, ref in capmap.items():
        b = bbox(REF / f"{fn}.stl")
        cx, cy = (b[0] + b[1]) / 2, (b[2] + b[3]) / 2
        hgt = b[5] - b[4]
        # flange is asymmetric on Select/Y: use the stem (lowest 1 mm) for the centre
        low = [(x, y) for x, y, z in stl_vertices(REF / f"{fn}.stl") if z < b[4] + 0.5]
        scx = (min(p[0] for p in low) + max(p[0] for p in low)) / 2
        scy = (min(p[1] for p in low) + max(p[1] for p in low)) / 2
        if math.hypot(scx - P[ref][1], scy - P[ref][2]) > TOL_POS or abs(hgt - 9.3) > 0.05:
            bad.append(f"{fn}: stem at ({scx:.2f},{scy:.2f}) vs {ref} ({P[ref][1]},{P[ref][2]}), height {hgt:.2f}")
    # L/R caps: 2.5 proud of the +Y face (85/2 + 2.5 = 45), top edge 0.15
    # under the split (16 - half the 0.3 window clearance = 15.85), one each
    # side of x = 0 — both in part_lr_caps.stl
    lb = bbox(REF / "part_lr_caps.stl")
    lx = sorted({round(x, 1) for x, y, z in stl_vertices(REF / "part_lr_caps.stl")})
    if abs(lb[3] - 45.0) > 0.05 or abs(lb[5] - 15.85) > 0.05 or lb[0] > -60 or lb[1] < 60 \
            or any(-45 < x < 45 for x in lx):
        bad.append(f"L/R caps: y max {lb[3]:.2f} (want 45), Z top {lb[5]:.2f} (want 15.85), "
                   f"x span {lb[0]:.1f}..{lb[1]:.1f}")
    # L/R levers, measured against the BOARD (SW11/SW12 placement) and the
    # TS-1187A drawing, not the scad: the upper arm's flat top is the
    # actuator tip (PCB bottom 16 - 1.5) less the 0.2 pretravel, its end
    # edge on the switch centre line, centred on it in X; the bump on the
    # lower arm 0..0.1 behind the cap flange (part_lr_caps y min)
    cap_back = min(y for x, y, z in stl_vertices(REF / "part_lr_caps.stl"))
    for ref, fn in (("SW11", "part_lr_lever_l"), ("SW12", "part_lr_lever_r")):
        vs = list(stl_vertices(REF / f"{fn}.stl"))
        sx_, sy_ = P[ref][1], P[ref][2]
        arm = [(x, y, z) for x, y, z in vs if abs(x - sx_) < 2.5 and y < sy_ + 3]
        if not arm:
            bad.append(f"{fn}: no upper arm near {ref} ({sx_},{sy_})")
            continue
        a_top = max(z for x, y, z in arm)
        a_end = min(y for x, y, z in arm)
        a_cx = (min(x for x, y, z in arm) + max(x for x, y, z in arm)) / 2
        bump = max(y for x, y, z in vs)
        if abs(a_top - (16.0 - 1.5 - 0.2)) > 0.02 or abs(a_end - sy_) > 0.02 \
                or abs(a_cx - sx_) > 0.05 or not 0 < cap_back - bump <= 0.1 + 1e-6:
            bad.append(f"{fn}: arm top {a_top:.2f} (want 14.3), end y {a_end:.2f} (want "
                       f"{sy_}), centre x {a_cx:.2f} (want {sx_}); bump {cap_back - bump:.2f} "
                       f"behind the cap flange")
    pb = bbox(REF / "part_power_slider.stl")
    if abs(pb[2] + 43.5) > 0.05 or abs(pb[5] - 17.4) > 0.05 or abs((pb[0] + pb[1]) / 2 + 40) > 0.1:
        bad.append(f"slider: y min {pb[2]:.2f} (want -43.5), Z top {pb[5]:.2f} (want 17.4), "
                   f"x centre {(pb[0] + pb[1]) / 2:.2f} (want -40)")
    sb = bbox(REF / "part_straps.stl")
    esp = P["U1"]
    strap_ok = abs(sb[5] - 13.2) < 0.05 and abs(sb[4] - 9.0) < 0.05   # pegs 3 mm into the posts
    strap_x = sorted({round(x, 1) for x, y, z in stl_vertices(REF / "part_straps.stl") if z > 13.1})
    inside_esp = [x for x in strap_x if esp[1] - esp[5] / 2 < x < esp[1] + esp[5] / 2]
    if not strap_ok or inside_esp:
        bad.append(f"straps Z {sb[4]:.2f}..{sb[5]:.2f}, x over the ESP32: {inside_esp[:3]}")
    db = bbox(PARTS / "part_display.stl")
    if abs(db[5] - 24.6) > 0.05 or (db[3] - db[2]) < PANEL_OUTLINE[1] - 0.05:
        bad.append(f"display part top Z {db[5]:.2f} (ceiling 24.6), Y span {db[3] - db[2]:.2f}")
    check("S10", "parts-aligned-to-board", not bad,
          "7 caps on their switches (9.3 tall), L/R caps 2.5 proud at the split, "
          "L/R lever arms on SW11/SW12 at 14.3 with the bump 0.05 behind the flange, "
          "slider 1 proud with its tab to 17.4, straps at Z 12..13.2 off the module, "
          "glass top at the ceiling"
          + (": " + "; ".join(bad) if bad else ""))

    # S11 thin walls measured on the STL slices
    thin = []
    for stl, zs, tag in ((top, (1.0, 3.0, 4.5, 6.0, 8.9), "top"),
                         (bot, (1.0, 5.0, 9.0, 13.0, 15.5, 17.0), "bottom"),
                         (CASE / "lr_cap_x2.stl", (0.5, 2.0, 4.0), "lr cap"),
                         (CASE / "power_slider.stl", (0.5, 1.5, 2.5), "slider"),
                         (CASE / "lr_lever_l.stl", (0.5, 1.5, 3.0, 5.0, 6.8), "L lever"),
                         (CASE / "lr_lever_r.stl", (0.5, 1.5, 3.0, 5.0, 6.8), "R lever")):
        for z in zs:
            for c in slice_svg(stl, z, thin=True):
                if c[1] > 0.3:
                    thin.append(f"{tag} z={z} {size(c)[0]:.1f}x{size(c)[1]:.1f} at "
                                f"({centre(c)[0]:.1f},{centre(c)[1]:.1f})")
    check("S11", "thin-walls-on-stl", not thin,
          f"27 STL slices eroded by 0.6: " + ("; ".join(thin[:6]) if thin else "nothing under 1.2 mm"))

    # S12 solidity: every print STL is a single watertight, positive-volume
    # body (numpy only — see mesh_solidity; 2026-10-10 meshcheck found
    # case_top.stl not a closed manifold: euler -21, 12 edges used by more
    # than two faces, 7 zero-volume two-triangle sheets where a cutter's
    # XY boundary sat exactly on another CSG operand's face)
    stl_files = sorted(CASE.glob("*.stl"))
    bad = []
    for f in stl_files:
        s = mesh_solidity(f)
        if not (s["watertight"] and s["bodies"] == 1 and s["volume"] > 1e-6):
            bad.append(f"{f.name}: watertight={s['watertight']} bodies={s['bodies']} "
                       f"bad_edges={s['bad_edges']} volume={s['volume']:.4g}")
    check("S12", "stl-solidity", not bad,
          f"{len(stl_files)} print STLs: watertight (vertices merged within "
          f"{MERGE_TOL} mm, every edge then used by exactly two triangles), "
          "exactly 1 body, volume > 0"
          + (": " + "; ".join(bad) if bad else ""))

    # S13 top-boss gussets (user 2026-10-10; height corrected, grown to
    # all-around n=8, then one rib shortened in BOTH h and reach for
    # clearance to the Menu cap under travel+rattle, same day): sample
    # one point per rib direction -- 8 angles every 45 deg all the way
    # around each boss -- at radius boss_r + reach/2 from each boss
    # centre (reach defaults to 3.0, i.e. sample radius 5.1, but is 1.4
    # for the one shortened rib, back-right boss 135 deg, reach 5.0 ->
    # sample radius 4.3): at z=2.3 (near the root, inside every rib's
    # own height) that point must be material; at z=8.7 (past where even
    # the tallest default rib ends at 8.5, still before the insert-boss
    # "end" slice at 8.8) the bare boss alone (radius 3.6) cannot reach
    # any of these sample radii, so it must be empty. An area-based
    # check (sum of blob area near the boss) was tried first and is NOT
    # used: at the back-right boss the slice merges with the
    # neighbouring Menu well into one contour, which swamps the area
    # signal; sampling the known rib directions directly is immune to
    # that pre-existing merge.
    RIB_REACH_OVERRIDE = {(70, -30.5, 135): 5.0}   # must track scad's
                                                    # top_boss_gusset_overrides
    gusset_z = top_slice(2.3)
    past_z = top_slice(8.7)
    bad = []
    for x, y in corners:
        for i in range(8):
            ang = 45 * i
            reach = RIB_REACH_OVERRIDE.get((x, y, ang), 3.0)
            r = 3.6 + reach / 2    # boss radius (Ø7.2, S5) + half the rib reach
            px = x + r * math.cos(math.radians(ang))
            py = y + r * math.sin(math.radians(ang))
            g_ok = point_in_material(gusset_z, px, py)
            p_ok = point_in_material(past_z, px, py)
            if not (g_ok and not p_ok):
                bad.append(f"({x},{y}) ang {ang:.1f}: material at z=2.3 "
                           f"{g_ok}, at z=8.7 {p_ok}")
    check("S13", "top-boss-gussets",
          not bad,
          "4 bosses x 8 ribs, all around: material at z=2.3 (near the root) "
          "at each rib's own angle and reach, gone by z=8.7 (past where even "
          "the tallest default rib ends at 8.5)"
          + (": " + "; ".join(bad) if bad else ""))

    shutil.rmtree(WORK, ignore_errors=True)
    print("-" * 72)
    fails = results.count(False)
    if fails:
        print(f"Results: FAIL — {fails}/{len(results)} STL measurements disagree with the sources")
        return 1
    print(f"Results: PASS — {len(results)}/{len(results)} STL measurements agree with board.py, "
          "the datasheets and the requirements")
    return 0


if __name__ == "__main__":
    try:
        sys.exit(main())
    except Structural as e:
        print(f"STRUCTURAL ERROR: {e}", file=sys.stderr)
        sys.exit(2)
