pjcau/esp32-emu-turbo/scripts/verify_enclosure_sync.py

#!/usr/bin/env python3
"""Enclosure <-> PCB mechanical sync gate — the shell must fit the board.

`hardware/enclosure/enclosure.scad` and `scripts/generate_pcb/board.py`
describe the same object from two sides, and until this gate nothing
compared them: the battery pocket held a cell that was no longer the
spec'd one, three button groups had drifted from their switches, and the
engraved A/B/X/Y labels named the wrong nets. Every check here reads the
scad's constants block (a CONTRACT: a constant this gate expects but
cannot parse is a structural error, never a skip) and compares it against
the board-side source of truth:

  outline / margins    board.py BOARD_W/H, CORNER_R
  screw bosses         board.py MOUNT_HOLES_ENC (the deliberate 4-of-6
                       subset: bosses must sit ON holes)
  edge cutouts (X)     board.py USBC_ENC / SD_ENC / PWR_SWITCH_ENC
  display viewport     board.py PANEL_ACTIVE_W/H (the viewport IS the
                       active area), PANEL_OUTLINE/PANEL_T, DISPLAY_ENC y;
                       the border split must add up to the outline; the
                       glass-centring references are the Select and Y cap
                       bodies computed from board SS/ABXY constants
  PCB model            hardware/enclosure/pcb_parts.scad is FRESH (it is
                       generated from board.py by generate_enclosure_pcb)
  buttons + LEDs       board.py DPAD/ABXY/SS/MENU/SHOULDER constants and
                       the six top-side LED placements (LED1-LED6)
  buttons + LEDs       board.py DPAD/ABXY/SS/MENU/LED/SHOULDER constants
                       (ABXY compared per-offset — DFM shifts included)
  ESP32 module         board.py ESP32_ENC cross-checked against the U1
                       placement; module envelope from the WROOM-1
                       datasheet (25.5 x 18.0 x 3.1 mm)
  battery pocket       scripts/vbench/models/bt1_lp105080.py `dims`
                       (10 x 50 x 80 mm) — axis map: length->X, width->Y,
                       thickness->Z
  Z stack              pcb_z == bot_d == boss top; body_d == bot_d + top_d;
                       top interior == panel thickness + cable riser; the
                       face-cap stem computed from that stack must still
                       reach the switch (SW_DATASHEET: TS-1187A code A,
                       1.5 mm); battery top clears every tall bottom-side
                       part (ESP32 module, J3 JST S2B-PH-SM4-TB 5.5 mm) by
                       >= MIN_Z_CLEAR wherever the pocket overlaps it in XY
  boss/pocket fit      no screw boss may stand inside the battery pocket
  L/R levers (V3)      edge caps press the ON-BOARD SW11/SW12 through a
                       printed bell-crank lever per side: the arm's end
                       edge on the board's switch centre, its top =
                       actuator tip - pretravel, arms giving a 0.8..1.25
                       ratio, the swing never above the actuator tip (the
                       TS-1187A cover from SW_DATASHEET), the beam clear
                       of the cap flange at full travel, the pin held in
                       its slot, lever and blocks clear of the pocket
                       border, the columns and every other bottom part;
                       the bottom column's half-column contact face
                       clears the SW11/SW12 pads
  -Y edge (V3)         SW16 knob (board PWR_SWITCH_ENC + MSK12C02) inside
                       the slider's fork; SD slit passes the 11 mm card
                       and the TF-01A housing front (U6) sets the card
                       reach; USB-C recess pad clears J1

Scalar constants are parsed with a COLUMN-0-anchored regex (a tolerant
anchor would bind module-local variables of the same name); vector
constants (`screw_positions`, `abxy_offsets`) go through a small
bracket-balanced reader. Expressions are evaluated over the constants
parsed so far (so `bot_d = body_d - top_d` works).

Output contract: every failing check prints a line starting with FAIL —
open_issues_report.py extracts exactly that shape.

Exit codes: 0 in sync · 1 mismatch(es) · 2 structural error (scad
contract broken, board module unimportable).
"""

from __future__ import annotations

import ast
import re
import sys
from pathlib import Path

BASE = Path(__file__).resolve().parent.parent
sys.path.insert(0, str(BASE))

SCAD = BASE / "hardware" / "enclosure" / "enclosure.scad"

TOL = 0.1          # mm — position/dimension agreement
MIN_Z_CLEAR = 0.5  # mm — battery top to ESP32 module underside
BOSS_R = 3.0       # mm — screw boss outer radius (screw_d_outer / 2)

# ESP32-S3-WROOM-1 module envelope, datasheet section 10 (dimensions):
# 25.5 x 18.0 x 3.1 mm
ESP_DATASHEET = {"w": 25.5, "h": 18.0, "d": 3.1}

# PCB thickness: JLCPCB 4-layer 1.6 mm stackup (verify_stackup's subject)
PCB_THICKNESS = 1.6

# Tactile switch C318884 = XKB TS-1187A-B-A-B, datasheet
# website/static/datasheets/SW1-SW13_Tact-Switch_C318884.pdf: height code
# A = 1.5 mm, body 5.1 x 5.1, travel 0.25 mm; the drawing: cover face
# 1.2 above the board, actuator o2.0, operating force code B = 160 gf
SW_DATASHEET = {"h": 1.5, "body": 5.1, "cover": 1.2, "act_d": 2.0,
                "travel": 0.25, "force_gf": 160}

# J3 = JST S2B-PH-SM4-TB, hardware/datasheets/J3_JST-PH-2P-SMD_C295747.pdf
# p.4 "Side entry type": height 5.5 mm, B = 7.9 mm (2 circuits); 6.0 mm
# body + 2.6 mm mouth along the mating axis
J3_DATASHEET = {"w": 7.9, "h": 8.6, "d": 5.5}

MIN_STEM = 1.0     # mm — a face-cap stem shorter than this cannot be printed

# SW16 = MSK12C02 (hardware/datasheets/SW16_Slide-Switch_C431540.pdf):
# body 1.4 tall, knob 1.6 wide and 1.5 long on the -Y face, travel 1.6
PWR_DATASHEET = {"body_d": 2.8, "body_h": 1.4, "knob_w": 1.6, "knob_l": 1.5,
                 "travel": 1.6}
# U6 = TF-01A: housing 14.5 x 15 (pcb_parts BODY_BY_PACKAGE), front edge
# at SD_ENC y - 7.5

# board.py:46-47 record the body relation: 170mm body = 160 + 2x5mm
BODY_MARGIN = 5.0


class Structural(RuntimeError):
    """The scad constants contract or a source of truth is broken."""


# ─── scad parsing ────────────────────────────────────────────────────────

_SCALAR_RE = re.compile(r"^([a-z][a-z0-9_]*) = ([^;]+);", re.MULTILINE)


def _eval_expr(expr: str, env: dict) -> float:
    """Evaluate a scad constant expression (numbers, names, + - * /)."""
    try:
        node = ast.parse(expr, mode="eval").body
    except SyntaxError:
        raise Structural(f"unparseable scad expression: {expr!r}")

    def ev(n):
        if isinstance(n, ast.Constant) and isinstance(n.value, (int, float)):
            return float(n.value)
        if isinstance(n, ast.Name):
            if n.id in env and isinstance(env[n.id], float):
                return env[n.id]
            raise Structural(f"unknown name {n.id!r} in scad expression "
                             f"{expr!r} — constant moved or renamed?")
        if isinstance(n, ast.BinOp):
            a, b = ev(n.left), ev(n.right)
            if isinstance(n.op, ast.Add):
                return a + b
            if isinstance(n.op, ast.Sub):
                return a - b
            if isinstance(n.op, ast.Mult):
                return a * b
            if isinstance(n.op, ast.Div):
                return a / b
        if isinstance(n, ast.UnaryOp) and isinstance(n.op, ast.USub):
            return -ev(n.operand)
        raise Structural(f"unsupported scad expression: {expr!r}")

    return ev(node)


def parse_scalars(text: str) -> dict:
    """Column-0 `name = value;` constants, evaluated in file order."""
    env: dict = {}
    for m in _SCALAR_RE.finditer(text):
        name, raw = m.group(1), m.group(2).strip()
        if raw.startswith('"'):
            env[name] = raw.strip('"')       # e.g. part = "assembly"
            continue
        if raw.startswith("["):
            continue                          # vectors: dedicated reader
        env[name] = _eval_expr(raw, env)
    return env


def parse_vector(text: str, name: str, env: dict) -> list:
    """Bracket-balanced reader for `name = [ [x, y], ... ];` at column 0."""
    m = re.search(r"^%s = \[" % re.escape(name), text, re.MULTILINE)
    if not m:
        raise Structural(f"vector constant {name!r} not found at column 0 "
                         "in enclosure.scad — the constants contract moved")
    i = m.end() - 1
    depth = 0
    for j in range(i, len(text)):
        if text[j] == "[":
            depth += 1
        elif text[j] == "]":
            depth -= 1
            if depth == 0:
                break
    else:
        raise Structural(f"unbalanced brackets in {name!r}")
    body = re.sub(r"//[^\n]*", "", text[i + 1:j])
    pairs = []
    for chunk in re.findall(r"\[([^\[\]]+)\]", body):
        parts = [p.strip() for p in chunk.split(",") if p.strip()]
        if len(parts) != 2:
            raise Structural(f"{name!r} entry is not an [x, y] pair: "
                             f"{chunk!r}")
        pairs.append(tuple(_eval_expr(p, env) for p in parts))
    if not pairs:
        raise Structural(f"{name!r} parsed empty")
    return pairs


def need(env: dict, *names: str) -> list:
    missing = [n for n in names if n not in env
               or not isinstance(env[n], float)]
    if missing:
        raise Structural("scad constants missing or non-numeric: "
                         + ", ".join(missing)
                         + " — the constants contract moved")
    return [env[n] for n in names]


# ─── checks ──────────────────────────────────────────────────────────────
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
