pjcau/esp32-emu-turbo/website/scripts/gen_dynarec_svgs.py

#!/usr/bin/env python3
"""Draw the SVG figures of the GBA dynarec page (merged into docs/software/optimizations.md on 2026-10-08; the figures are no longer shown).

Hand-placed boxes and arrows, one palette, one font stack: the figures stay
vector, readable in both site themes (each has its own card background) and
reproducible. Run: python3 website/scripts/gen_dynarec_svgs.py
Output: website/static/img/gba-dynarec/*.svg
"""
import os

from svgfig import C, INK, MUTED, Svg

OUT = os.path.join(os.path.dirname(__file__), "..", "static", "img", "gba-dynarec")

Svg.out_dir = OUT


# ---------------------------------------------------------------------------
def interp_vs_dynarec():
    s = Svg(1000, 330, "Interpreter vs dynarec")
    s.group(20, 20, 470, 290, "Interpreter  ·  execute_arm", "gray")
    s.text(255, 60, "pays fetch + decode + dispatch on EVERY instruction, every frame", 12, color=MUTED)
    s.box(60, 90, 170, 64, "fetch", ["next ARM/Thumb opcode"], "gray")
    s.box(280, 90, 170, 64, "decode", ["big switch in C"], "gray")
    s.box(170, 210, 170, 64, "execute", ["C code per opcode"], "gray")
    s.arrow([(230, 122), (278, 122)])
    s.arrow([(365, 156), (300, 208)])
    s.arrow([(200, 208), (140, 158)])
    s.group(510, 20, 470, 290, "Dynarec  ·  execute_arm_translate", "green")
    s.text(745, 60, "pays them ONCE per block, then runs native Xtensa code", 12, color=MUTED)
    s.box(540, 90, 410, 64, "first time a block is reached", ["decode it once, write Xtensa code into the cache"],
          "orange")
    s.box(540, 210, 410, 64, "every other time", ["jump straight into the generated code (blocks chain)"], "green")
    s.arrow([(745, 156), (745, 208)], "translate once", lx=745, ly=182)
    s.save("interp-vs-dynarec.svg")


def stack():
    s = Svg(1000, 690, "The stack, layer by layer")
    rows = [
        ("GBA game", "gray", [("ARM7TDMI code in the cartridge ROM", "", 700)]),
        ("retro-go", "blue", [("launcher", "pick a game · resume/save states", 300),
                              ("gbsp app", "frame loop · input · display · audio · menus", 390)]),
        ("gpSP core", "teal", [("GBA hardware model", "memory map · DMA · timers · IRQ · sound · renderer", 380),
                               ("CPU", "interpreter (cpu.cpp)  or  translator (cpu_threaded.c)", 310)]),
        ("Xtensa dynarec", "orange", [("backend", "xtensa_emit*.h · xtensa_stub.c: what each op becomes", 380),
                                      ("xjit core", "encoders · labels · executable memory", 310)]),
        ("ESP-IDF 5.4", "purple", [("FreeRTOS + drivers", "2 cores · esp_mmu_map (PSRAM exec) · cache sync · heap caps", 700)]),
        ("ESP32-S3 N16R8", "gray", [("2 × Xtensa LX7 240 MHz", "32 KB I-cache shared · 64 KB D-cache", 340),
                                    ("memory", "~190 KB internal free · 8 MB PSRAM · 16 MB flash", 350)]),
    ]
    y = 24
    for i, (label, col, items) in enumerate(rows):
        stroke, bg, tx = C[col]
        h = 88
        s.add(f'<rect x="24" y="{y}" width="952" height="{h}" rx="14" fill="{bg}" stroke="{stroke}" stroke-width="1.4"/>')
        s.add(f'<rect x="24" y="{y}" width="170" height="{h}" rx="14" fill="{stroke}"/>')
        s.add(f'<rect x="180" y="{y}" width="14" height="{h}" fill="{stroke}"/>')
        s.text(109, y + h / 2 + 5, label, 15, 700, "#ffffff")
        x = 214
        for title, sub, w in items:
            s.box(x, y + 12, w, h - 24, title, [sub] if sub else [], col, title_size=13.5, row_size=12)
            x += w + 18
        if col == "orange":
            s.badge(900, y - 10, "NEW")
        if i < len(rows) - 1:
            s.arrow([(500, y + h + 1), (500, y + h + 17)], head=True)
        y += h + 18
    s.save("stack.svg")
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
